0-Alchemist-0/Game_Consoles/Assets/RPSLS_game/ChatGPT Image May 15, 2026, 11_23_18 PM (2).png

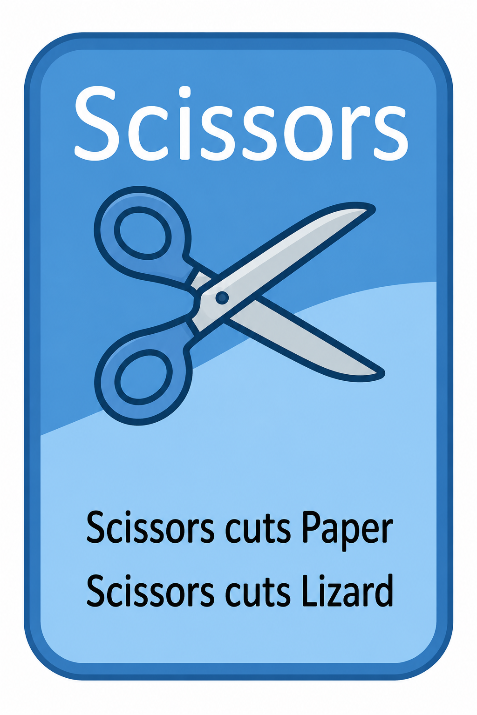
Assets/RPSLS_game/ChatGPT Image May 15, 2026, 11_23_18 PM (2).png
