0-Alchemist-0/Game_Consoles/Assets/RPSLS_game/Gemini_Generated_Image_hztmo1hztmo1hztm.png

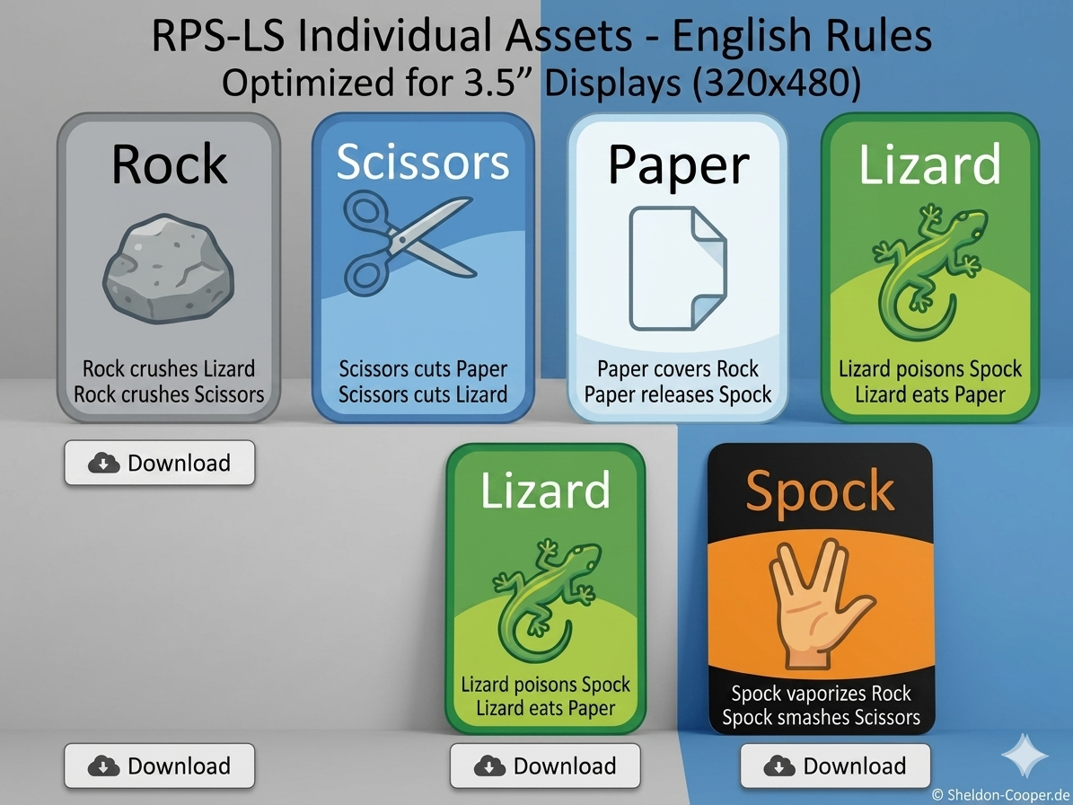
Assets/RPSLS_game/Gemini_Generated_Image_hztmo1hztmo1hztm.png
