0-Alchemist-0/Game_Consoles/CAD/Reference 18650 Cell - 1029881/images/18650_Refrence_Cell.png

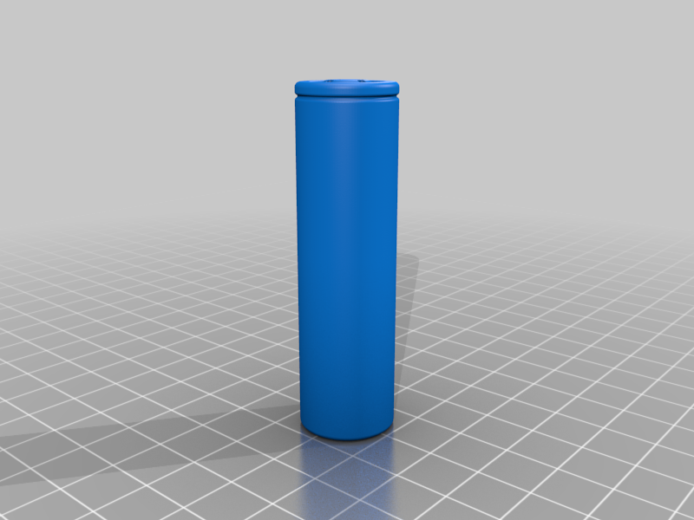
CAD/Reference 18650 Cell - 1029881/images/18650_Refrence_Cell.png
