0-Alchemist-0/Game_Consoles/CAD/Reference 18650 Cell - 1029881/images/ice_screenshot_20150923-011706.png

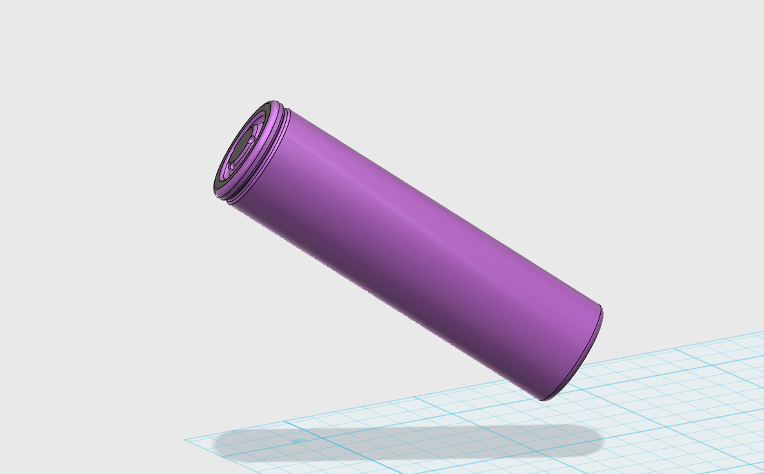
CAD/Reference 18650 Cell - 1029881/images/ice_screenshot_20150923-011706.png
