0-Alchemist-0/Game_Consoles/Pics&Videos/00002_LowerCase.png

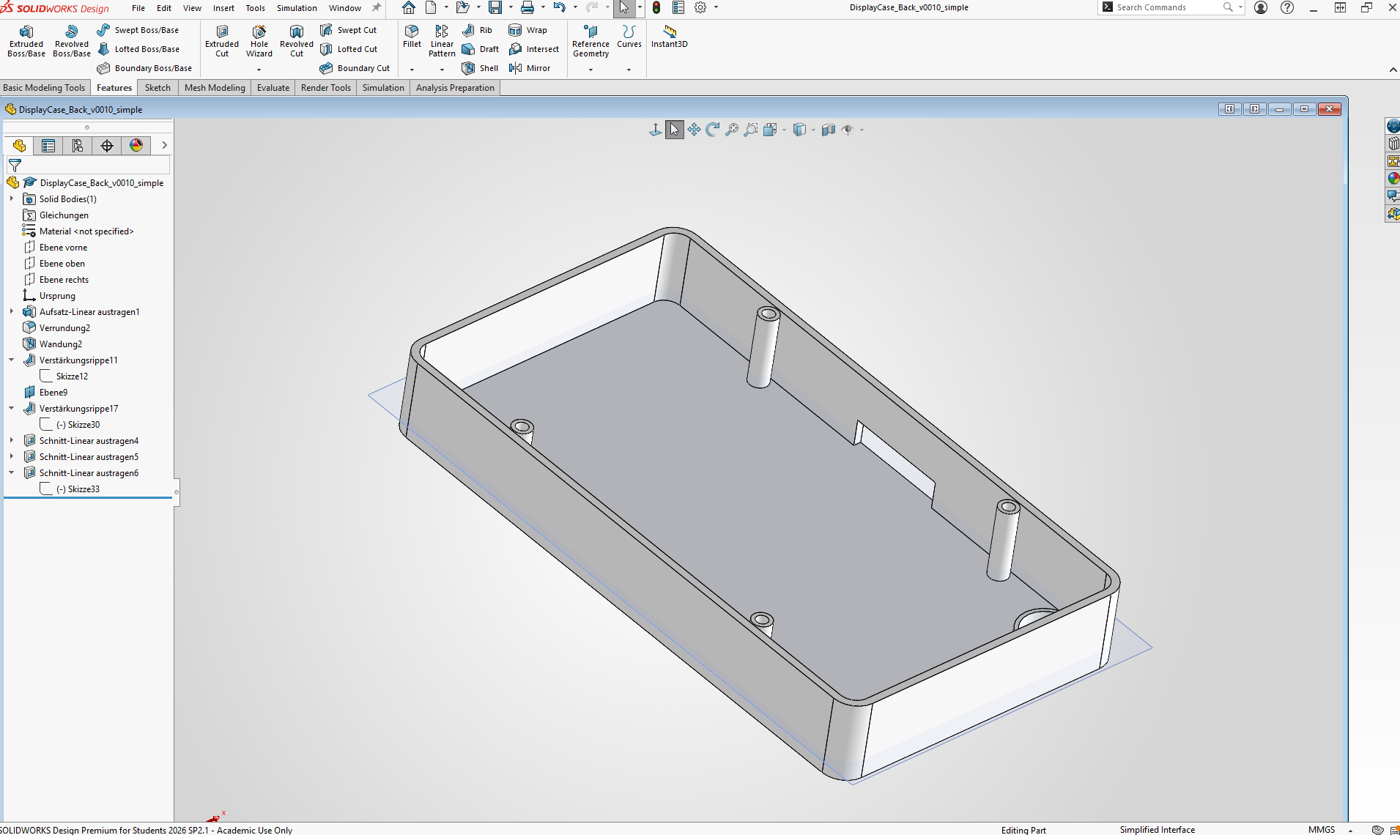
Pics&Videos/00002_LowerCase.png
