0-Alchemist-0/Game_Consoles/Pics&Videos/00003_TopCoverCase.png

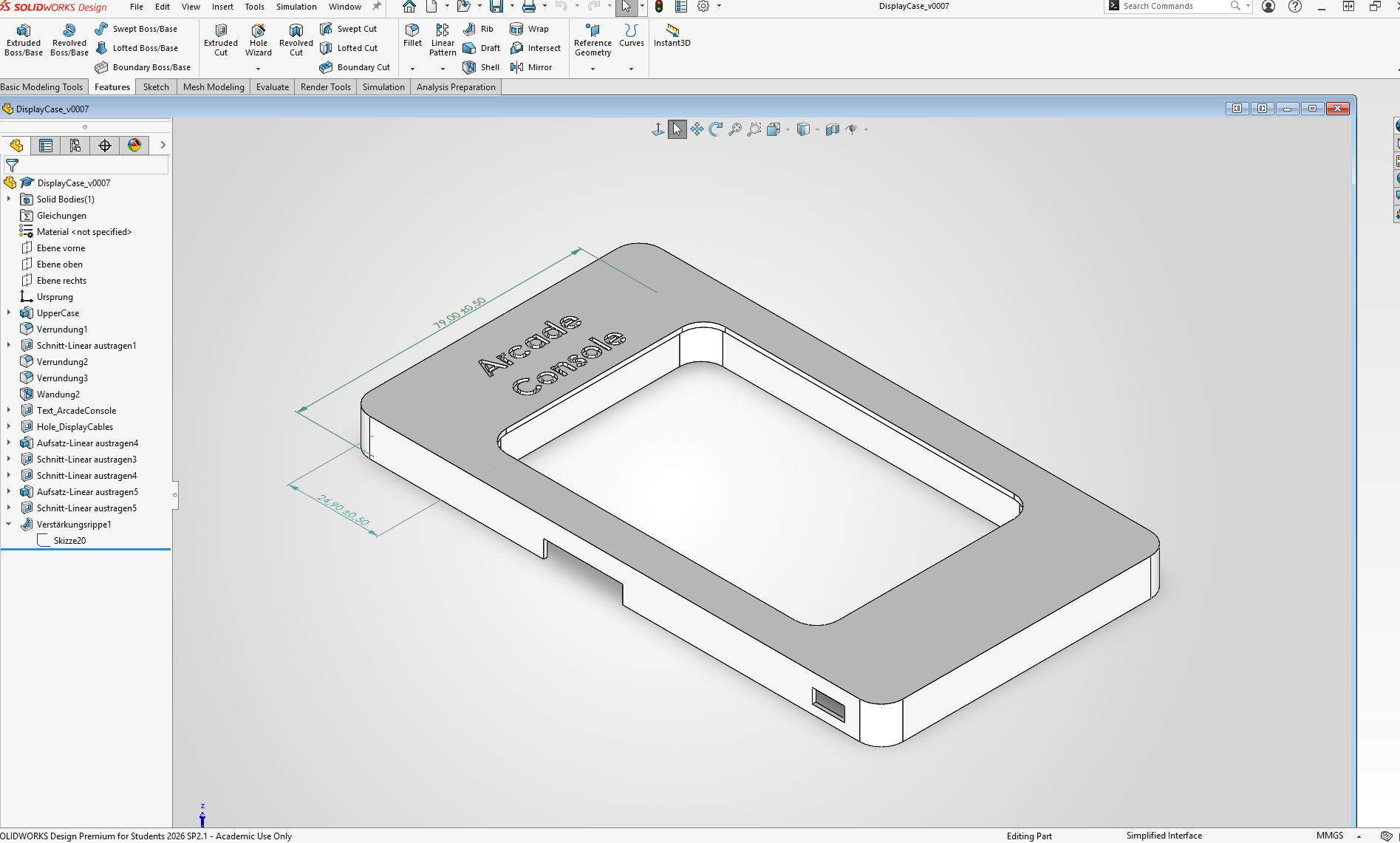
Pics&Videos/00003_TopCoverCase.png
