0-Alchemist-0/Game_Consoles/Pics&Videos/0004_Internal 18650 battery holder.png

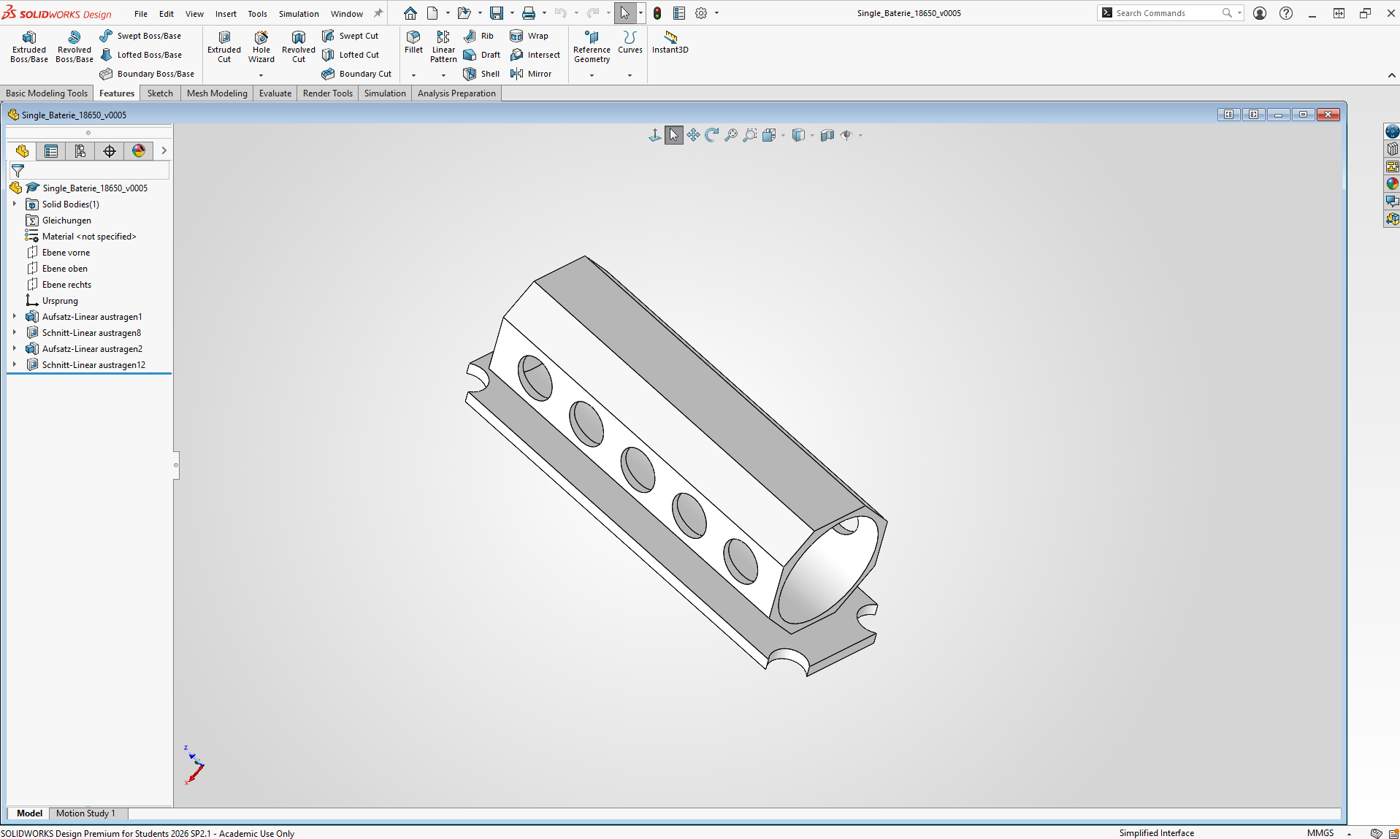
Pics&Videos/0004_Internal 18650 battery holder.png
