0-Alchemist-0/Game_Consoles/Pics&Videos/0005_PCB_Supprt.png

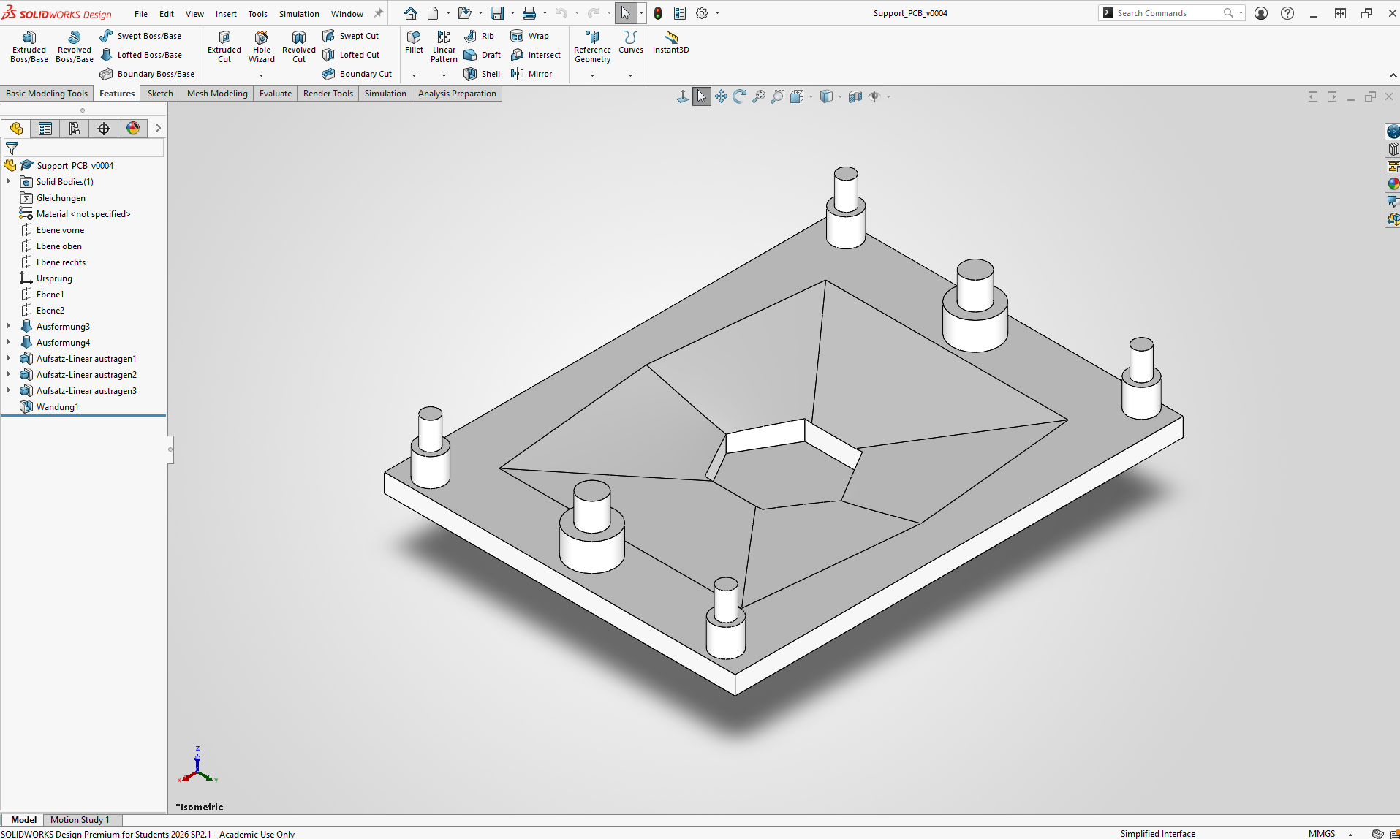
Pics&Videos/0005_PCB_Supprt.png
