0-Alchemist-0/Game_Consoles/Pics&Videos/0006_Support part for the Arduino Nano ESP32 board.png

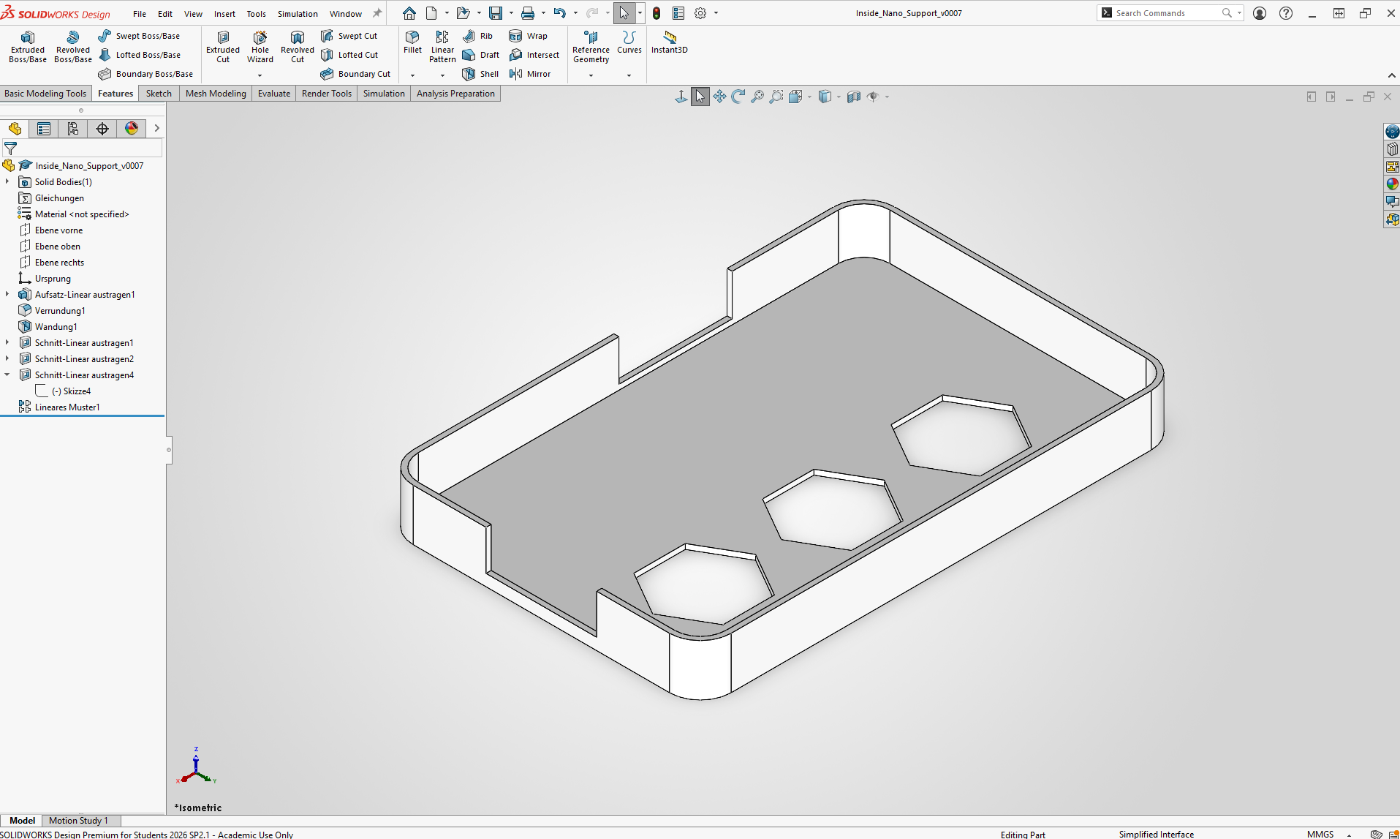
Pics&Videos/0006_Support part for the Arduino Nano ESP32 board.png
