0-Alchemist-0/Game_Consoles/Pics&Videos/0009_Top-down open view of the console.jpeg

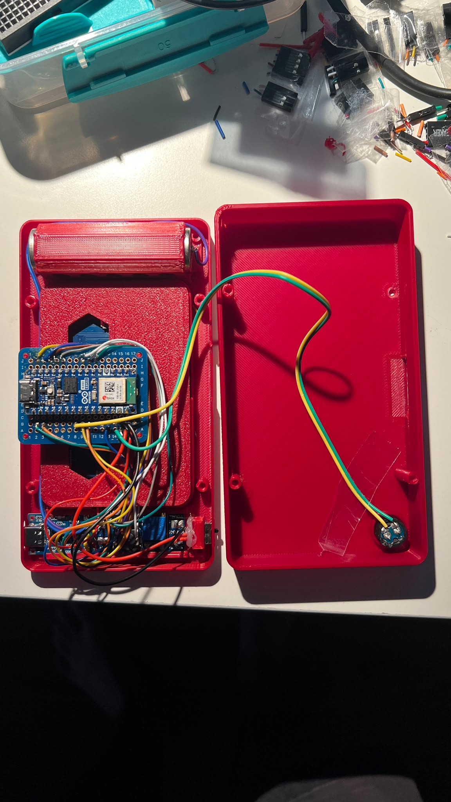
Pics&Videos/0009_Top-down open view of the console.jpeg
