0-Alchemist-0/Game_Consoles/SD_card/games_screen/games_background.png

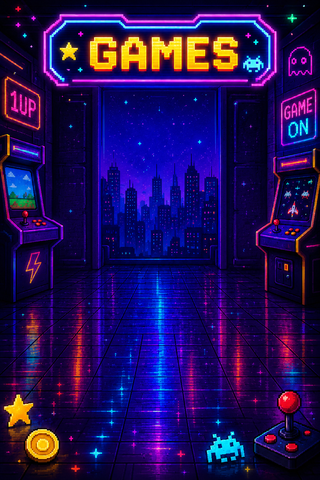
SD_card/games_screen/games_background.png
