0-Alchemist-0/Game_Consoles/SD_card/home_screen/background_preview.png

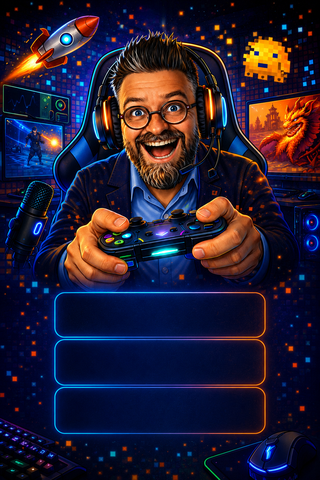
SD_card/home_screen/background_preview.png
