0-Alchemist-0/Game_Consoles/SD_card/intro/frame_000_preview.png

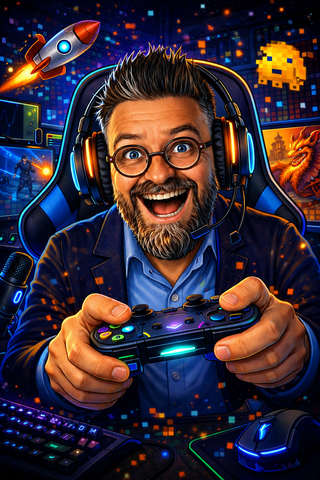
SD_card/intro/frame_000_preview.png
