0-Alchemist-0/Game_Consoles/SD_card/RPSLS_game/general/RockPapercissors.png

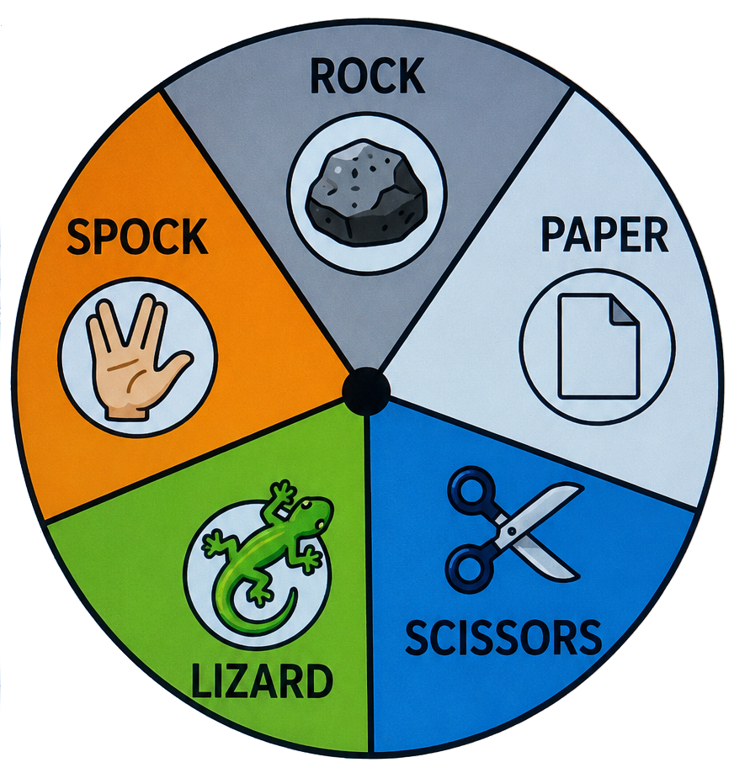
SD_card/RPSLS_game/general/RockPapercissors.png
