0-Alchemist-0/Game_Consoles/SD_card/RPSLS_game/general/rpsls_wheel_preview.png

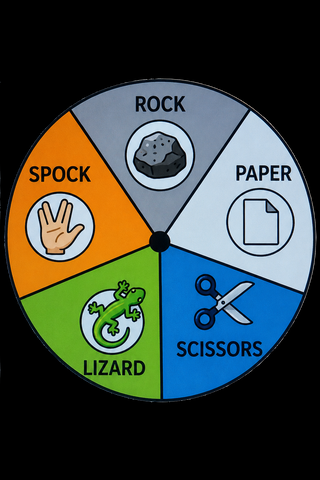
SD_card/RPSLS_game/general/rpsls_wheel_preview.png
