0-Alchemist-0/Game_Consoles/SD_card/RPSLS_game/local/draw/draw_spock_preview.png

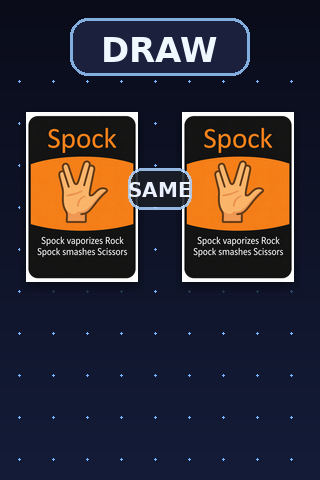
SD_card/RPSLS_game/local/draw/draw_spock_preview.png
