0-Alchemist-0/Game_Consoles/SD_card/RPSLS_game/local/player1_wins/win_lizard_eats_paper_preview.png

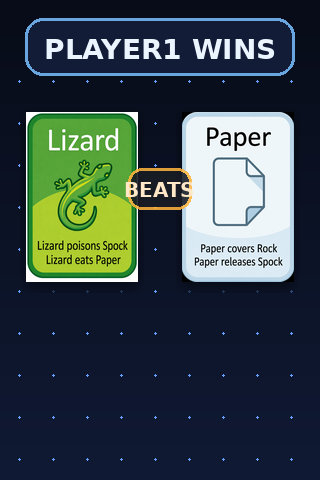
SD_card/RPSLS_game/local/player1_wins/win_lizard_eats_paper_preview.png
