0-Alchemist-0/Game_Consoles/SD_card/RPSLS_game/lose/lose_lizard_to_rock_preview.png

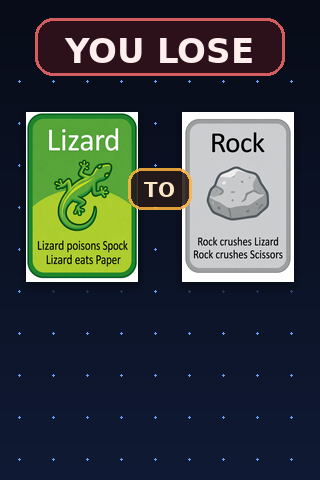
SD_card/RPSLS_game/lose/lose_lizard_to_rock_preview.png
