0-Alchemist-0/Game_Consoles/SD_card/RPSLS_game/lose/lose_rock_to_spock_preview.png

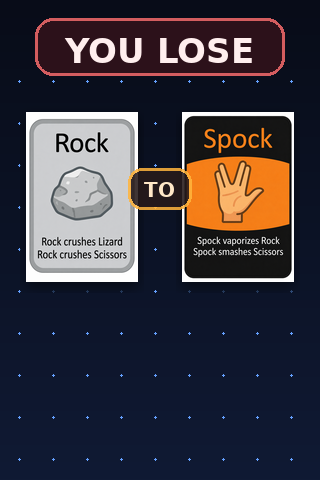
SD_card/RPSLS_game/lose/lose_rock_to_spock_preview.png
