0-Alchemist-0/Game_Consoles/SD_card/RPSLS_game/lose/lose_spock_to_lizard_preview.png

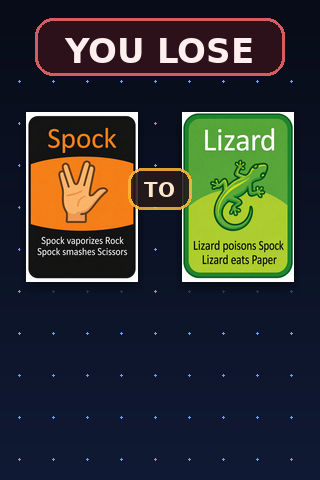
SD_card/RPSLS_game/lose/lose_spock_to_lizard_preview.png
