0-Alchemist-0/Game_Consoles/SD_card/RPSLS_game/main_screen/rock_paper_scissors_background.png

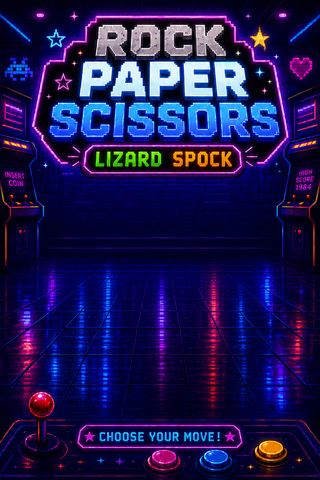
SD_card/RPSLS_game/main_screen/rock_paper_scissors_background.png
