0-Alchemist-0/Game_Consoles/SD_card/tictactoe_game/tictactoe_background.png

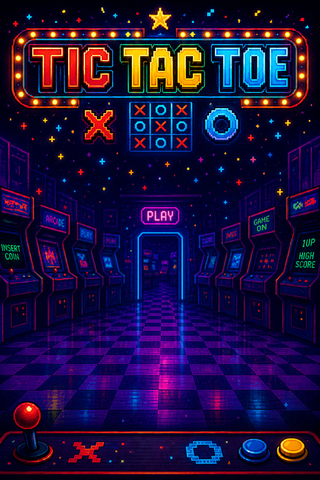
SD_card/tictactoe_game/tictactoe_background.png
