0-Alchemist-0/Game_Consoles/CAD/Carcasa_v0001-BodyFillet.step

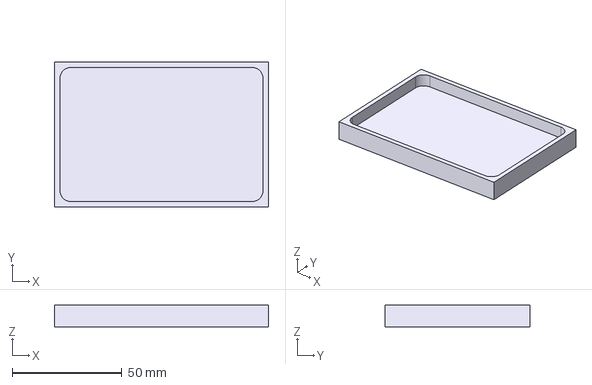
[picture p62: CAD file, 2026-05-14]
CAD/Carcasa_v0001-BodyFillet.step
97.6 x 66.2 x 10.0 mm
