0-Alchemist-0/Game_Consoles/SolidWorks/DisplayCase_Back_v0011_simple.SLDPRT

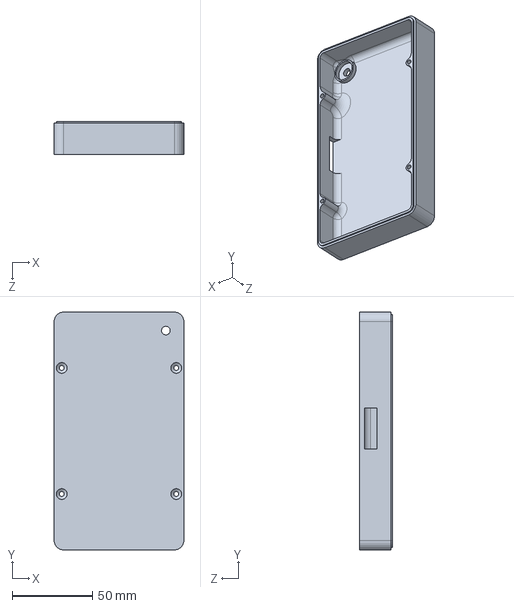
[picture p63: CAD file, 2026-07-01]
SolidWorks/DisplayCase_Back_v0011_simple.SLDPRT
81.0 x 148.4 x 20.6 mm
