0-Alchemist-0/Game_Consoles/SolidWorks/DisplayCase_v0008.SLDPRT

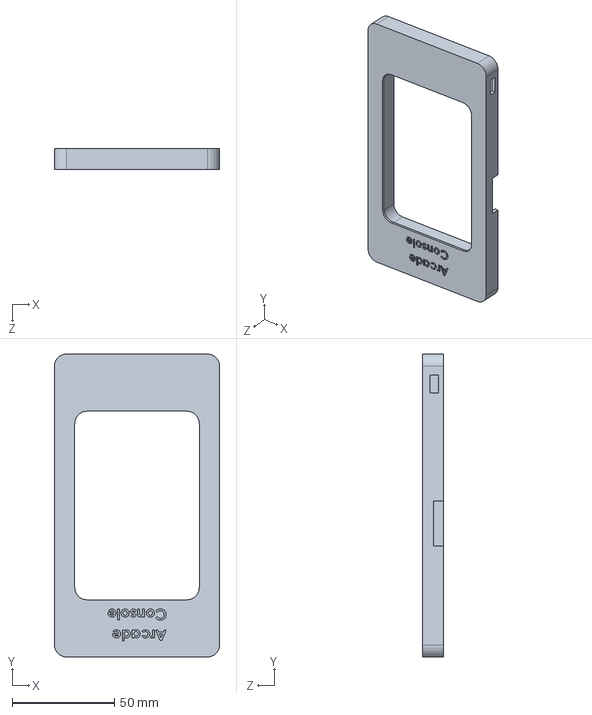
[picture p64: CAD file, 2026-07-01]
SolidWorks/DisplayCase_v0008.SLDPRT
81.0 x 148.4 x 10.3 mm
