0-Alchemist-0/Game_Consoles/SolidWorks/Single_Baterie_18650_v0006_simple.SLDPRT

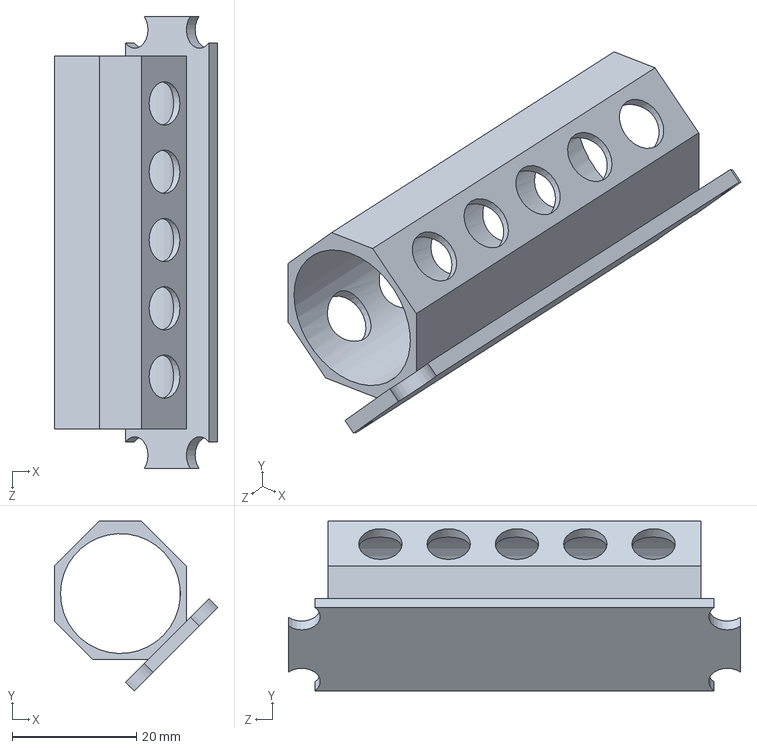
[picture p66: CAD file, 2026-07-01]
SolidWorks/Single_Baterie_18650_v0006_simple.SLDPRT
26.3 x 27.3 x 72.8 mm
