0-Alchemist-0/Game_Consoles/SolidWorks/DisplayCase_v0010_simple.SLDPRT

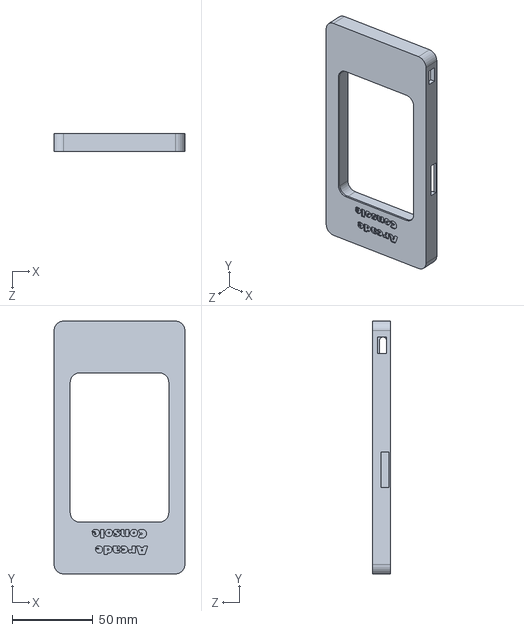
[picture p67: CAD file, 2026-07-01]
SolidWorks/DisplayCase_v0010_simple.SLDPRT
81.0 x 156.4 x 11.3 mm
