0-Alchemist-0/Game_Consoles/SolidWorks/MT3608_4056_v0002.SLDPRT

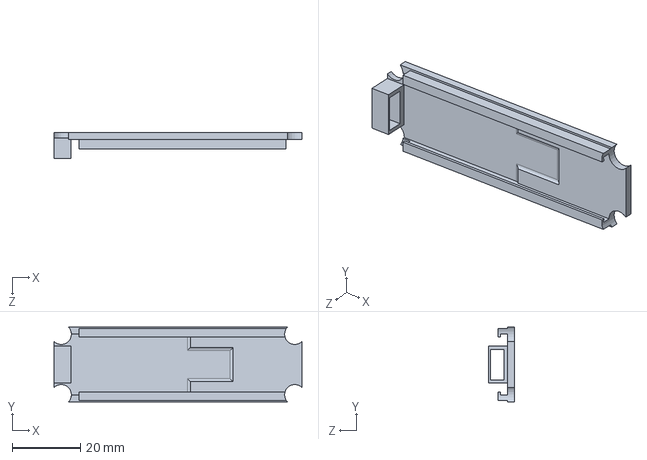
[picture p68: CAD file, 2026-06-27]
SolidWorks/MT3608_4056_v0002.SLDPRT
72.8 x 22.0 x 7.50 mm
