0-Alchemist-0/Game_Consoles/SolidWorks/Support_PCB_v0003.SLDPRT

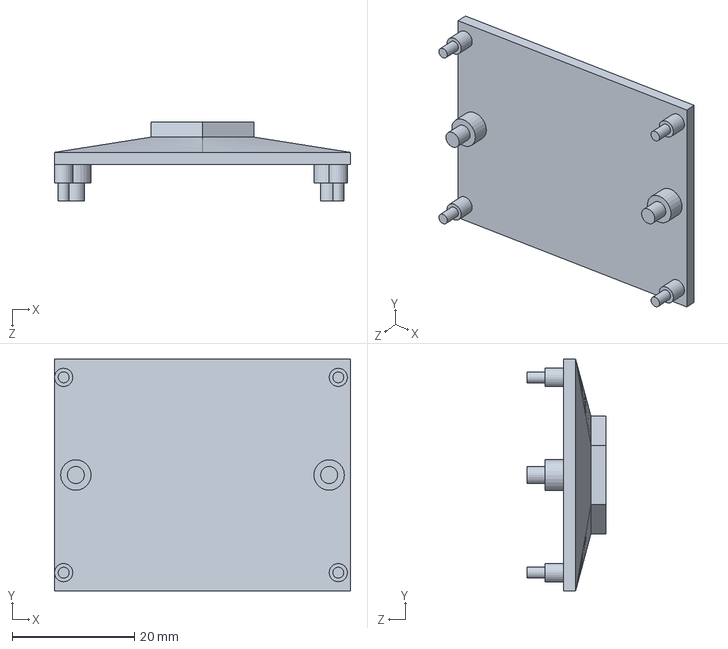
[picture p69: CAD file, 2026-06-27]
SolidWorks/Support_PCB_v0003.SLDPRT
48.5 x 38.0 x 13.0 mm
