0-Alchemist-0/Game_Consoles/SolidWorks/016_Suport_OLED_PCB-PCB_EPȘZON.step

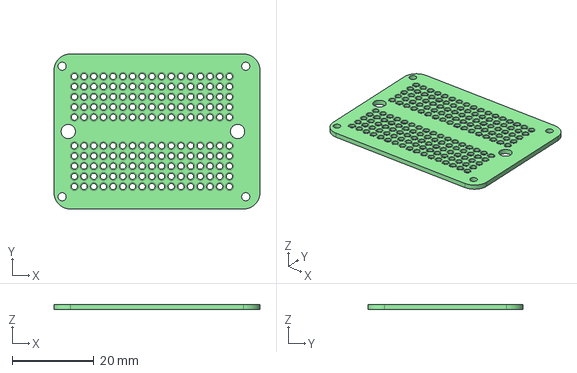
[picture p70: CAD file, 2026-06-27]
SolidWorks/016_Suport_OLED_PCB-PCB_EPȘZON.step
50.5 x 38.0 x 1.30 mm
