0-Alchemist-0/Game_Consoles/SolidWorks/Single_Baterie_18650_v0005.SLDPRT

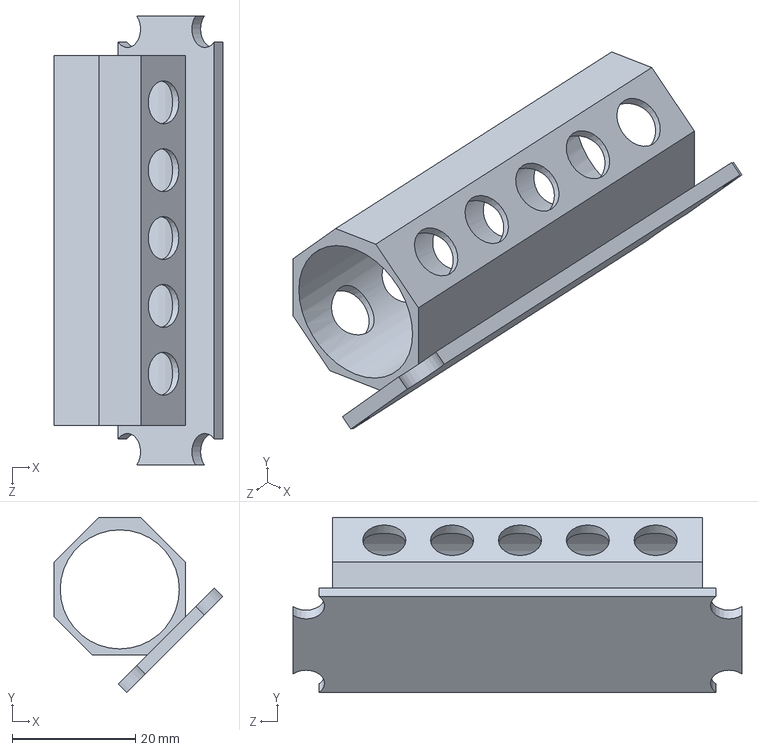
[picture p71: CAD file, 2026-06-27]
SolidWorks/Single_Baterie_18650_v0005.SLDPRT
27.4 x 28.4 x 72.8 mm
