0-Alchemist-0/Game_Consoles/SolidWorks/MT3608_4056_v0001.SLDPRT

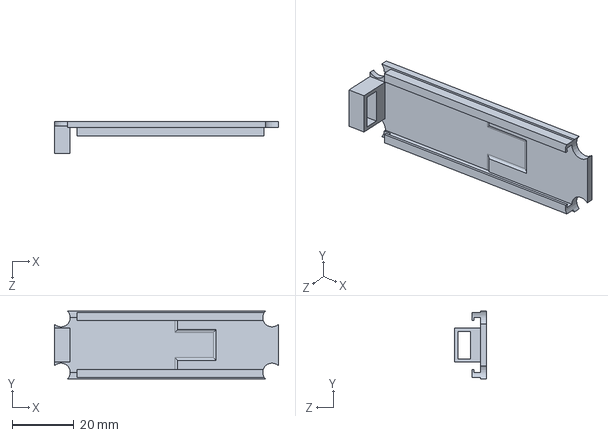
[picture p72: CAD file, 2026-06-27]
SolidWorks/MT3608_4056_v0001.SLDPRT
72.8 x 22.0 x 10.5 mm
