0-Alchemist-0/Game_Consoles/SolidWorks/DisplayCase_v0003.SLDPRT

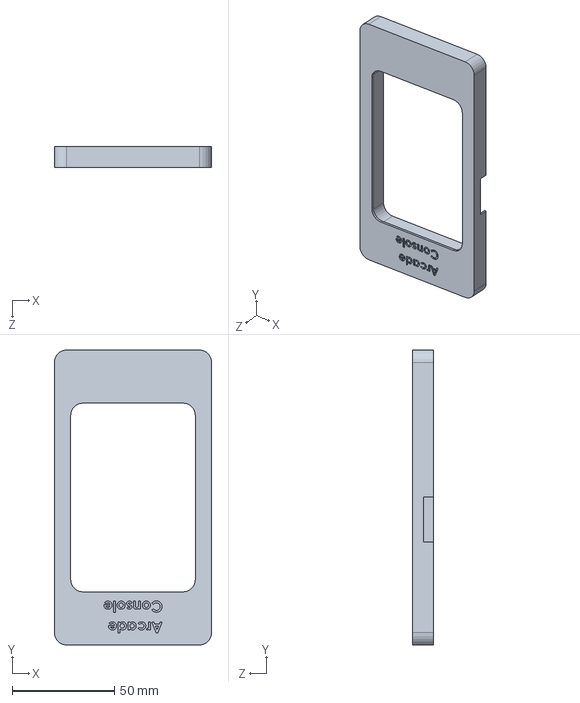
[picture p73: CAD file, 2026-06-27]
SolidWorks/DisplayCase_v0003.SLDPRT
77.0 x 144.4 x 10.3 mm
