0-Alchemist-0/Game_Consoles/SolidWorks/DisplayCase_Back_v0002.SLDPRT

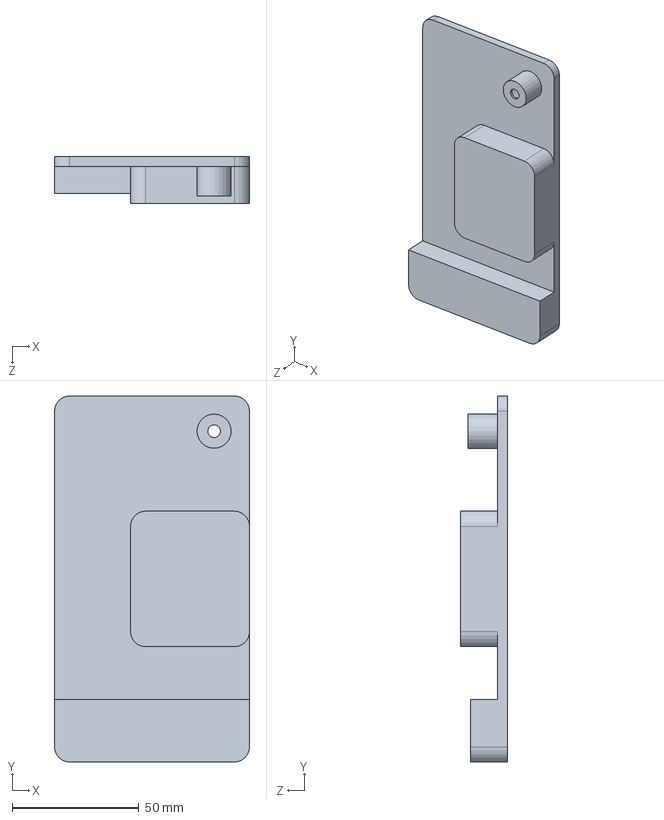
[picture p74: CAD file, 2026-06-27]
SolidWorks/DisplayCase_Back_v0002.SLDPRT
77.0 x 144.4 x 18.6 mm
