0-Alchemist-0/Game_Consoles/SolidWorks/Single_Baterie_18650.SLDPRT

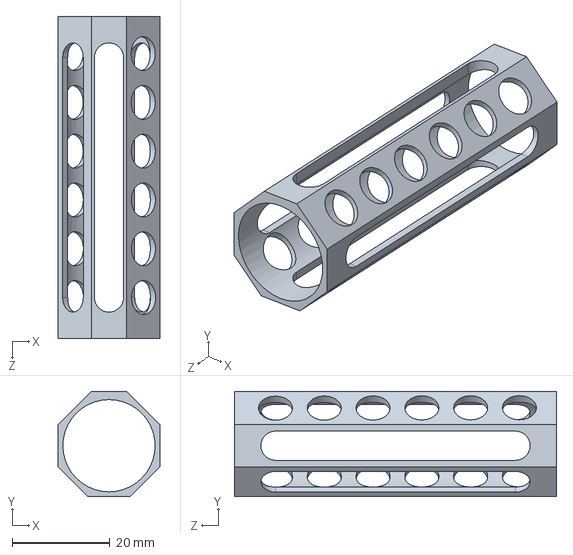
[picture p75: CAD file, 2026-06-27]
SolidWorks/Single_Baterie_18650.SLDPRT
20.9 x 21.6 x 66.0 mm
