0-Alchemist-0/Game_Consoles/SolidWorks/Inside_Nano_Support_v0006.SLDPRT

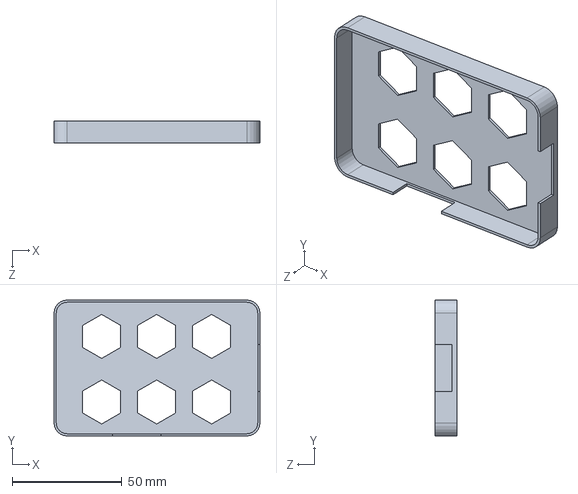
[picture p76: CAD file, 2026-06-27]
SolidWorks/Inside_Nano_Support_v0006.SLDPRT
93.6 x 61.8 x 10.0 mm
