0-Alchemist-0/Game_Consoles/SolidWorks/DisplayCase_Back_v0004.SLDPRT

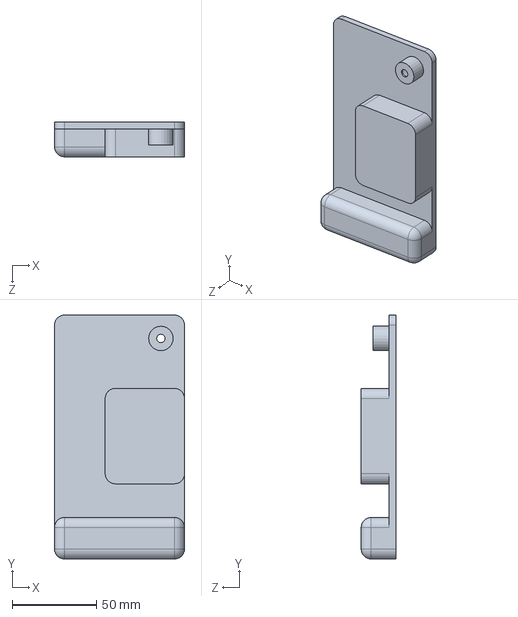
[picture p77: CAD file, 2026-06-27]
SolidWorks/DisplayCase_Back_v0004.SLDPRT
77.0 x 144.4 x 20.6 mm
