0-Alchemist-0/Game_Consoles/SolidWorks/MT3608 HW-045 DC-DC Step-Up.stl

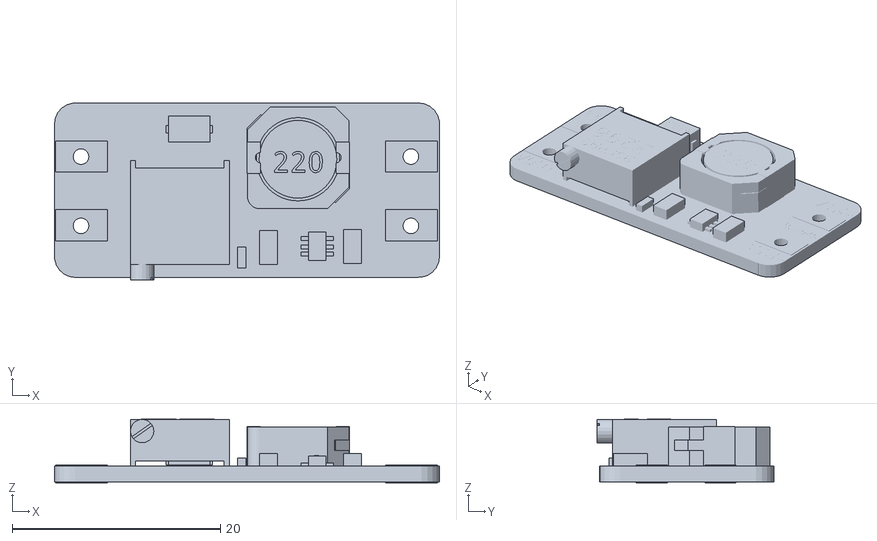
[picture p78: CAD file, 2026-06-27]
SolidWorks/MT3608 HW-045 DC-DC Step-Up.stl
37.0 x 17.0 x 6.12
