0-Alchemist-0/Game_Consoles/SolidWorks/Inside_Nano_Support_v0001.SLDPRT

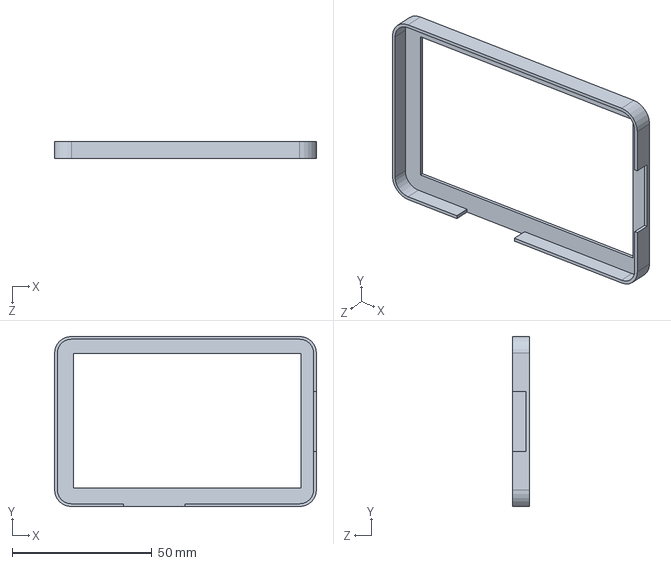
[picture p79: CAD file, 2026-06-27]
SolidWorks/Inside_Nano_Support_v0001.SLDPRT
93.6 x 60.8 x 6.00 mm
