0-Alchemist-0/Game_Consoles/SolidWorks/Double_Pack_Baterie_18650.SLDPRT

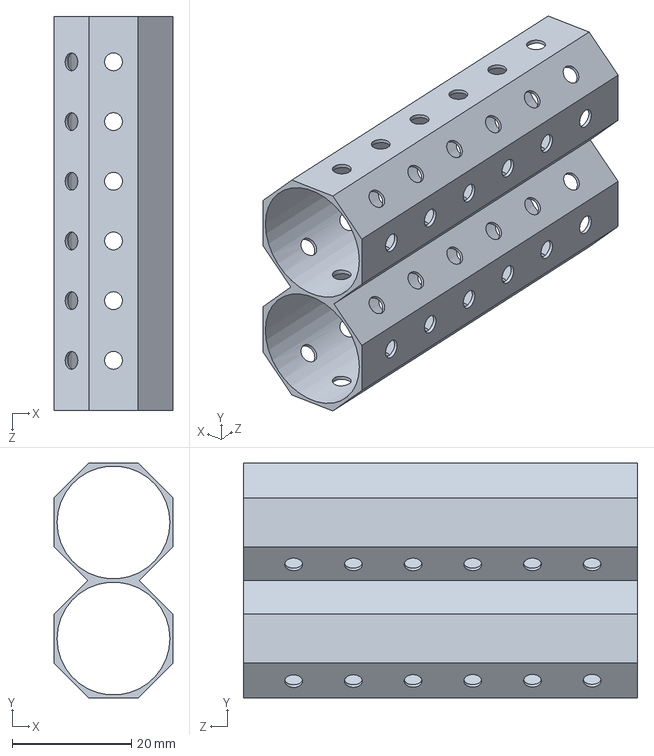
[picture p81: CAD file, 2026-06-27]
SolidWorks/Double_Pack_Baterie_18650.SLDPRT
19.9 x 39.3 x 66.0 mm
