0-Alchemist-0/Game_Consoles/SolidWorks/DisplayCase_Back_v0006.SLDPRT

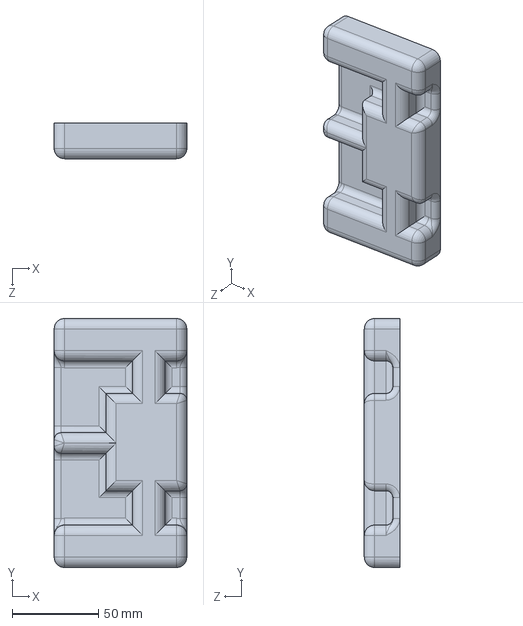
[picture p82: CAD file, 2026-06-27]
SolidWorks/DisplayCase_Back_v0006.SLDPRT
77.0 x 144.4 x 20.6 mm
