0-Alchemist-0/Game_Consoles/SolidWorks/MT3608_4056_v0003.SLDPRT

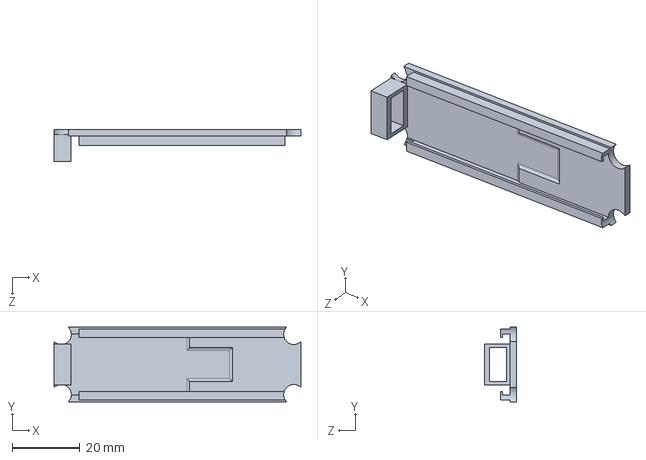
[picture p83: CAD file, 2026-06-27]
SolidWorks/MT3608_4056_v0003.SLDPRT
72.8 x 22.0 x 9.50 mm
