0-Alchemist-0/Game_Consoles/SolidWorks/016_Suport_OLED_PCB-Support_OLED.step

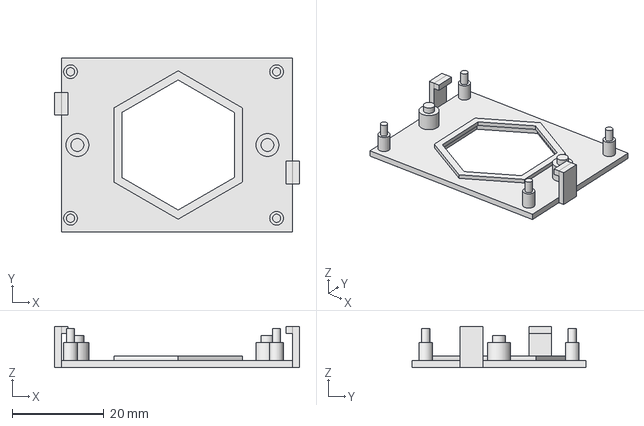
[picture p84: CAD file, 2026-06-27]
SolidWorks/016_Suport_OLED_PCB-Support_OLED.step
53.5 x 38.0 x 9.00 mm
