0-Alchemist-0/Game_Consoles/SolidWorks/Inside_Nano_Support_v0004.SLDPRT

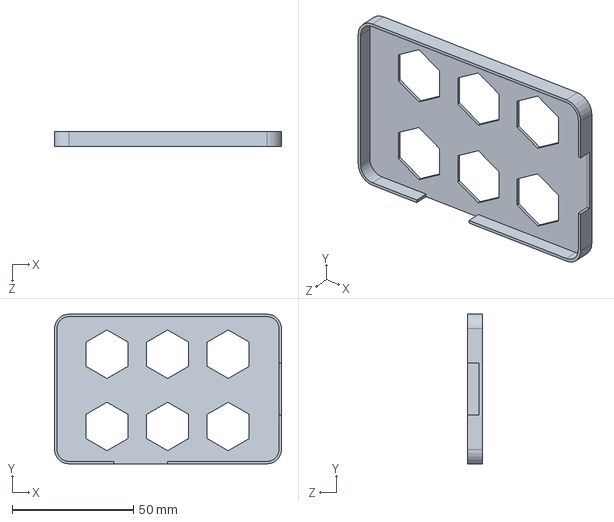
[picture p85: CAD file, 2026-06-27]
SolidWorks/Inside_Nano_Support_v0004.SLDPRT
93.6 x 61.8 x 6.00 mm
