0-Alchemist-0/Game_Consoles/SolidWorks/Support_PCB.SLDPRT

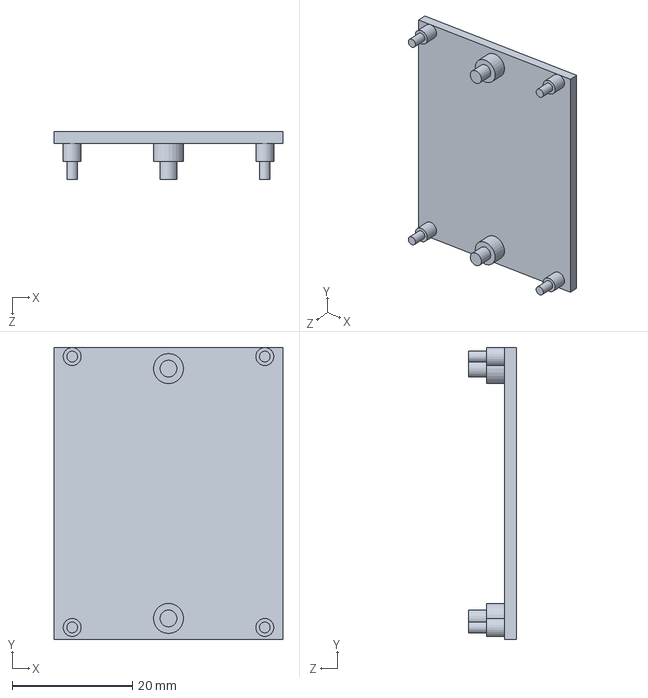
[picture p86: CAD file, 2026-06-27]
SolidWorks/Support_PCB.SLDPRT
38.0 x 48.5 x 8.00 mm
