0-Alchemist-0/Game_Consoles/SolidWorks/Inside_Nano_Support_v0002.SLDPRT

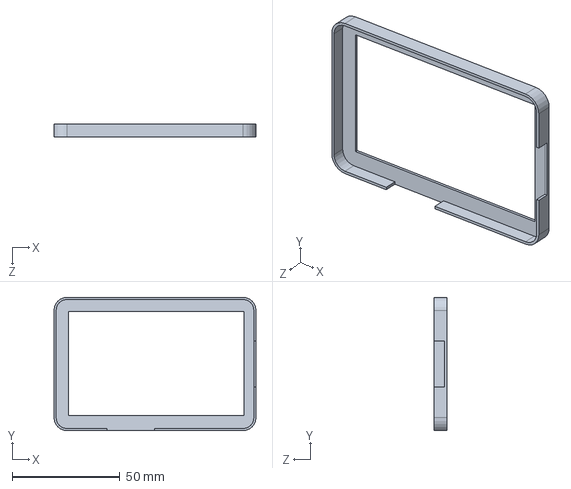
[picture p87: CAD file, 2026-06-27]
SolidWorks/Inside_Nano_Support_v0002.SLDPRT
93.6 x 61.8 x 6.00 mm
