0-Alchemist-0/Game_Consoles/SolidWorks/DisplayCase_Back_v0009.SLDPRT

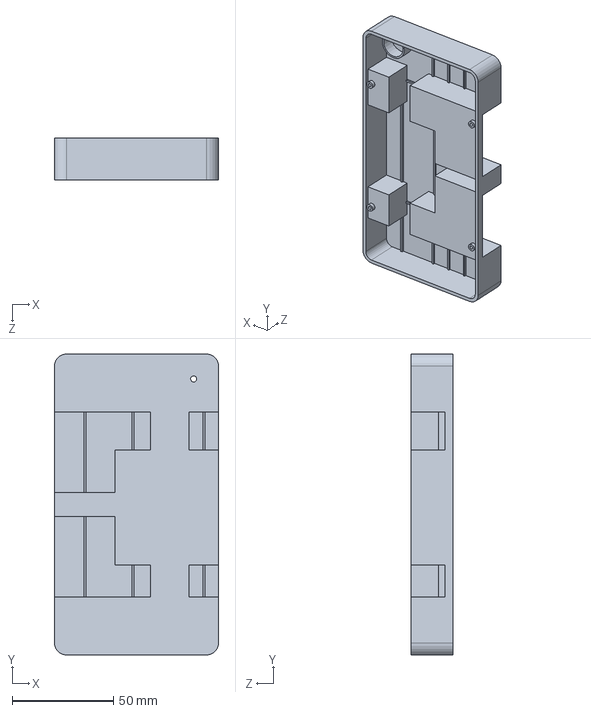
[picture p88: CAD file, 2026-06-27]
SolidWorks/DisplayCase_Back_v0009.SLDPRT
81.0 x 148.4 x 20.6 mm
