0-Alchemist-0/Game_Consoles/SolidWorks/DisplayCase_Back_v0010_simple.SLDPRT

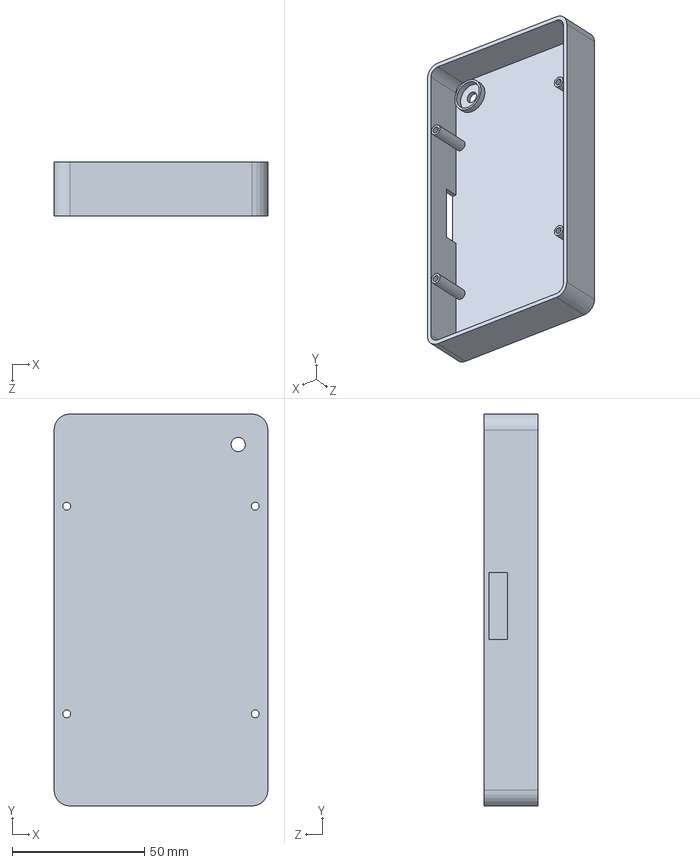
[picture p89: CAD file, 2026-06-27]
SolidWorks/DisplayCase_Back_v0010_simple.SLDPRT
81.0 x 148.4 x 20.6 mm
