0-Alchemist-0/Game_Consoles/SolidWorks/Single_Baterie_18650_v0003.SLDPRT

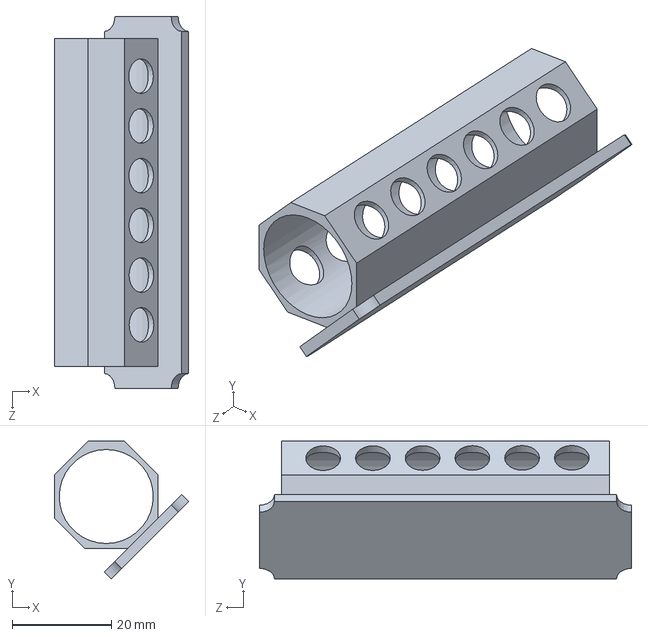
[picture p90: CAD file, 2026-06-27]
SolidWorks/Single_Baterie_18650_v0003.SLDPRT
27.0 x 27.7 x 74.8 mm
