0-Alchemist-0/Game_Consoles/SolidWorks/Single_Baterie_18650_v0002.SLDPRT

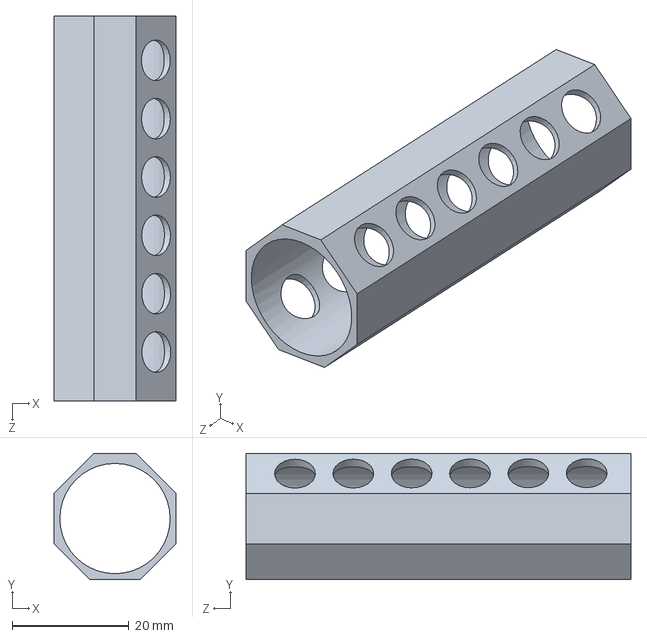
[picture p91: CAD file, 2026-06-27]
SolidWorks/Single_Baterie_18650_v0002.SLDPRT
20.9 x 21.6 x 66.0 mm
