0-Alchemist-0/Game_Consoles/SolidWorks/DisplayCase_v0006.SLDPRT

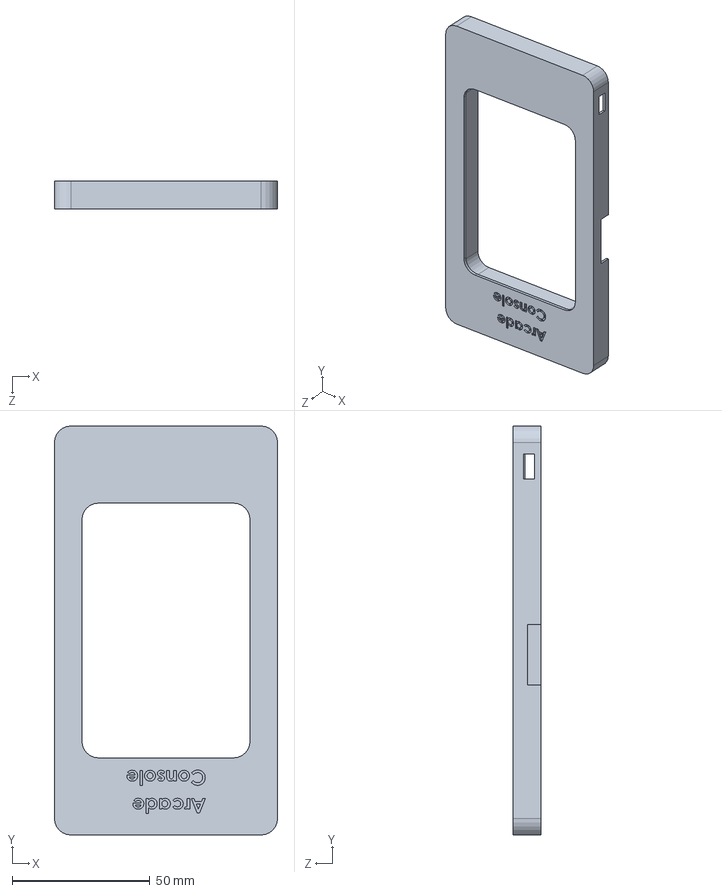
[picture p92: CAD file, 2026-06-27]
SolidWorks/DisplayCase_v0006.SLDPRT
81.0 x 148.4 x 10.3 mm
