0-Alchemist-0/Game_Consoles/SolidWorks/PiezoSpeaker.SLDPRT

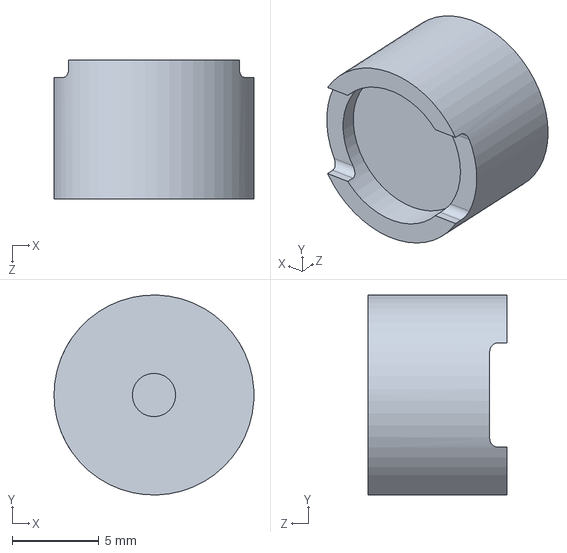
[picture p93: CAD file, 2026-06-27]
SolidWorks/PiezoSpeaker.SLDPRT
11.5 x 11.5 x 8.00 mm
