0-Alchemist-0/Game_Consoles/SolidWorks/On_Off_Switch.SLDPRT

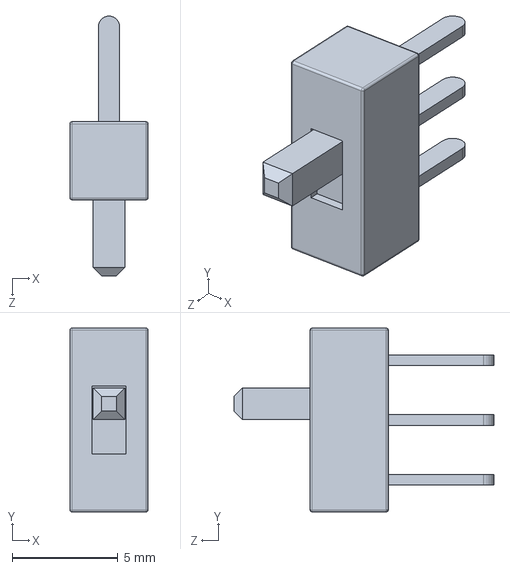
[picture p94: CAD file, 2026-06-27]
SolidWorks/On_Off_Switch.SLDPRT
3.70 x 8.70 x 12.3 mm
