0-Alchemist-0/Game_Consoles/Pics&Videos/0001_Assembly.png

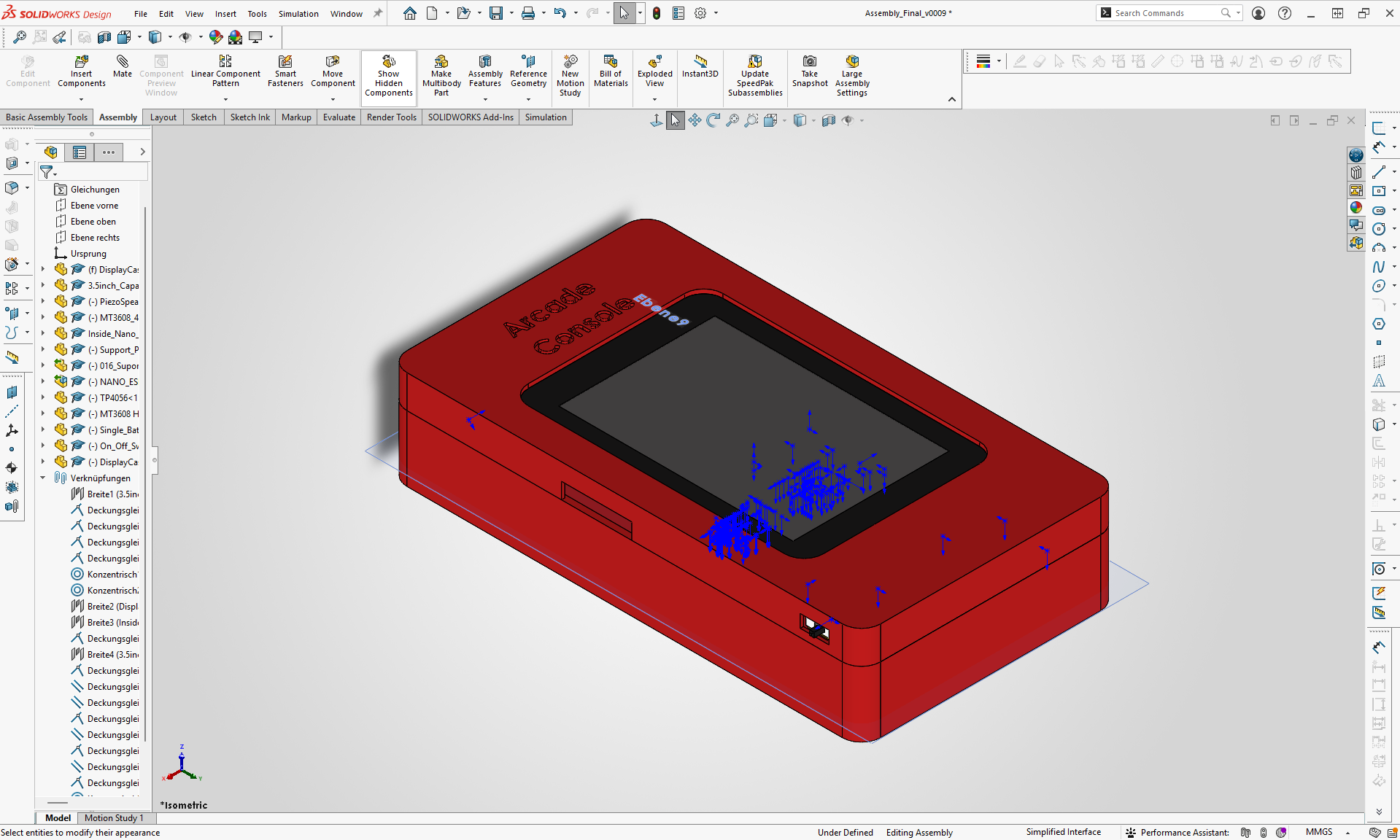
Pics&Videos/0001_Assembly.png
