0-Alchemist-0/Game_Consoles/Pics&Videos/0008_Physical assembly of the console prototype.jpeg

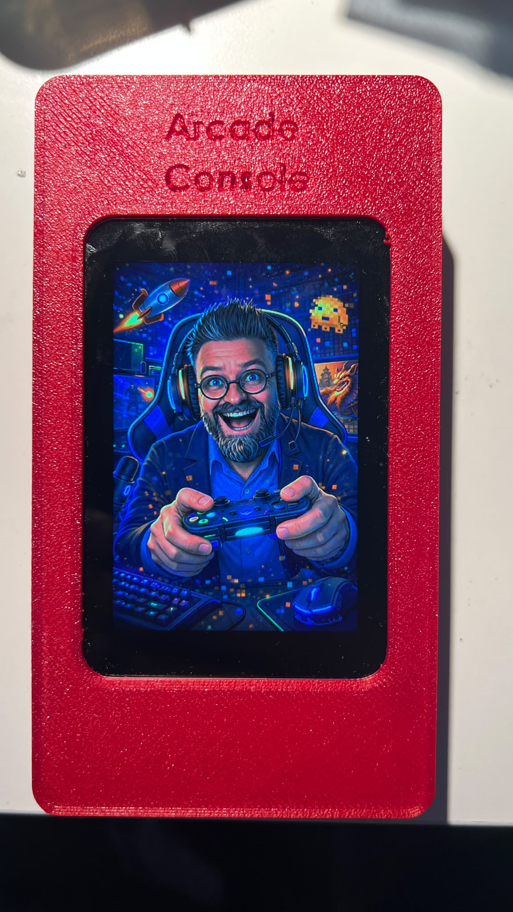
Pics&Videos/0008_Physical assembly of the console prototype.jpeg
