0-Alchemist-0/Game_Consoles/Game_Consoles.ino

// ============================================================================
// CHANGELOG
// ============================================================================
// Version 9.5 - 2026-07-01 - Stabilized Tic Tac Toe network joining by
// preferring configured or known Host SSIDs, throttling Join TCP retries, and
// disabling WiFi sleep/TCP buffering during peer games.
// Version 9.4 - 2026-07-01 - Expanded source block comments with game
// ownership notes so each major code area explains its purpose.
// Version 9.3 - 2026-07-01 - Removed the hour from every changelog entry and
// standardized changelog dates to use date-only format.
// Version 9.2 - 2026-07-01 - Added network Hex Pipes gameplay with a
// shared puzzle seed, visible P1/P2 move counters, solve-time race logic, and
// less-moves tie breaker.
// Version 9.1 - 2026-07-01 - Added Hex Pipes to the Games menu with a
// dedicated game menu, hexapipes.vercel.app reference, local playable puzzle,
// best-score storage, and Host/Join placeholders.
// Version 9.0 - 2026-07-01 - Added Reset Score buttons and high-score
// display lines to every game main menu, with persistent high scores for
// Breakout, Pong, and Snake.
// Version 8.9 - 2026-07-01 - Converted remaining menu and page UI text
// to English across Tic Tac Toe, shared network screens, and result screens.
// Version 8.8 - 2026-07-01 - Reworked Home Settings into Music and WiFi
// subpages, with Music ON/OFF, SFX ON/OFF, editable Host IP, and persisted
// default WiFi SSID selection.
// Version 8.7 - 2026-07-01 - Added a looping non-game background
// chiptune inspired by the attached arcade melody, with automatic mute during
// gameplay and short audio cues taking priority.
// Version 8.6 - 2026-06-19 - Switched Frogger Host/Join to use the standard
// WiFi TCP flow (same as Tic Tac Toe) instead of ESP-NOW.  Both players run
// traffic locally, exchange frog-state/goal/over messages over TCP, and the
// FROG_STATE parsing is now symmetric so both host and join apply remote state.
// Version 8.5 - 2026-06-18 - Reworked Frogger Host/Join to use the
// attached ESP-NOW peer-to-peer concept with local frog simulation, HELLO/ACK/
// START pairing, and compact frog, goal, and game-over packets.
// Version 8.4 - 2026-06-18 - Reworked Frogger network gameplay using the
// attached local-simulation model: each console moves its own frog and exchanges
// compact frog states over the existing TCP link.
// Version 8.3 - 2026-06-18 - Reverted Frogger JOIN local lane animation
// changes after they broke second-console gameplay.
// Version 8.2 - 2026-06-18 - Prevented Frogger JOIN lane position jumps
// by using remote lane coordinates only during full redraw synchronization.
// Version 8.1 - 2026-06-18 - Reduced Frogger JOIN flicker by animating
// lanes locally and using remote states only for sync plus player redraws.
// Version 8.0 - 2026-06-18 - Reduced Frogger network state backlog and
// added input sequence tracking so P2 movement is not overwritten by old states.
// Version 7.9 - 2026-06-18 - Fixed Frogger network controls by forcing
// P1/P2 player roles, immediate network respawn, and lighter remote input redraws.
// Version 7.8 - 2026-06-18 - Fixed Frogger network movement feedback by
// redrawing player inputs immediately and moving the first road car off-center.
// Version 7.7 - 2026-06-18 - Fixed the Frogger network compile error by
// declaring sendFroggerState before updateFroggerGame uses it.
// Version 7.6 - 2026-06-18 - Added host-authoritative Frogger network
// gameplay with two visible colored players sharing the same lanes and logs.
// Version 7.5 - 2026-06-18 - Added Frogger to the Games menu with a
// dedicated mode menu and local playable road, river, logs, cars, goals, and
// high score gameplay.
// Version 7.4 - 2026-06-18 - Added host-authoritative Ranch Rush network
// gameplay with two visible differently colored players and synced ranch state.
// Version 7.3 - 2026-06-18 - Fixed Ranch Rush lasso persistence by using
// a gameplay cowboy sprite without the decorative menu lasso loop.
// Version 7.2 - 2026-06-18 - Implemented local Ranch Rush gameplay with
// lane movement, lasso catching, animal spawning, lives, levels, high score,
// dirty-rect rendering, restart, and menu return.
// Version 7.1 - 2026-06-18 - Added Ranch Rush to the Games menu with a
// ranch-themed mode menu, Local/Host/Join/Back navigation, and shared network
// setup placeholders.
// Version 7.0 - 2026-06-18 - Added network Snake gameplay with
// host-authoritative two-player movement, synced state packets, shared food,
// different snake colors, and remote direction control.
// Version 6.9 - 2026-06-18 - Reduced Snake movement flicker by switching
// from full-board redraws to incremental cell updates during movement.
// Version 6.8 - 2026-06-18 - Implemented local Snake gameplay with a
// timed grid loop, food spawning, collision detection, score HUD, touch
// direction controls, restart, and menu return.
// Version 6.7 - 2026-06-18 - Added Snake to the Games menu with a
// dedicated Local, Host, Join, and Back mode menu wired into the shared
// network setup flow.
// Version 6.6 - 2026-06-18 - Improved network Pong Player 2 paddle
// collision by preserving client-owned paddle state, adding remote-paddle hit
// forgiveness, and predicting local bounce.
// Version 6.5 - 2026-06-17 - Smoothed network Pong ball movement by
// sending velocity in PN_STATE, throttling host broadcasts, and predicting
// ball motion locally between received state packets.
// Version 6.4 - 2026-06-17 - Added Host/Join network gameplay for
// Pong with host-authoritative ball physics and synced paddle/score state.
// Version 6.3 - 2026-06-17 - Added Pong to the Games menu with a
// local playable portrait paddle game and arcade-style menu.
// Version 6.2 - 2026-06-17 - Added Host/Join network gameplay for
// Breakout where the first player to lose all three lives loses the match.
// Version 6.1 - 2026-06-17 - Matched Breakout menu buttons to the
// Tic Tac Toe transparent arcade text style by removing extra slot panels.
// Version 6.0 - 2026-06-17 - Added a generated arcade fallback
// background for the Breakout menu and switched its menu buttons to the
// transparent Tic Tac Toe arcade text style.
// Version 5.9 - 2026-06-17 - Implemented local portrait Breakout
// gameplay with bricks, paddle, touch controls, lives, score, and restart.
// Version 5.8 - 2026-06-17 - Added a generated arcade fallback
// background for the Tanks Wars menu and switched its menu buttons to the
// transparent Tic Tac Toe arcade text style.
// Version 5.7 - 2026-06-17 - Added a second Games page with Breakout and
// a Breakout mode menu containing Local, Host, Join, and Back.
// Version 5.6 - 2026-06-17 - Added Host/Join network gameplay for Tanks
// Wars with synced terrain seed, controls, turns, and firing.
// Version 5.5 - 2026-06-17 - Added a generated arcade HOME fallback
// screen when SD home assets are missing.
// Version 5.4 - 2026-06-16 - Renamed user-facing artillery game text to
// Tanks Wars across menus, placeholders, and screen titles.
// Version 5.3 - 2026-06-03 - Added SD-loaded Rock-Paper-Scissors menu
// background support from /RPSLS_game/main_screen/rock_paper_scissors_background.raw.
// Version 5.2 - 2026-06-03 - Ported the Rock-Paper-Scissors arcade menu
// background and switched its menu to the transparent arcade text buttons.
// Version 5.1 - 2026-06-03 - Changed Games and Tic Tac Toe menu buttons
// to transparent arcade text buttons with consistent two-color lettering.
// Version 5.0 - 2026-06-03 - Added SD-loaded Tic Tac Toe menu background
// support from /tictactoe_game/tictactoe_background.raw with generated fallback.
// Version 4.9 - 2026-06-03 - Added SD-loaded Games screen background
// support from /games_screen/games_background.raw with generated fallback.
// Version 4.8 - 2026-06-03 - Added an arcade background and marquee title
// to the Games selection screen, reusing the neon button text style.
// Version 4.7 - 2026-06-03 - Ported the arcade Tic Tac Toe menu artwork
// and changed shared UI buttons to the same neon arcade style.
// Version 4.6 - 2026-06-03 - Added Arduino Nano ESP32 board-label and
// physical-header comments for each configured GPIO.
// Version 4.5 - 2026-05-28 - Added explanatory comments across the main
// source blocks to make hardware, UI, networking, and game logic easier to read.
// Version 4.4 - 2026-05-27 - Added randomized Tanks Wars terrain
// generation for each new local round.
// Version 4.3 - 2026-05-27 - Removed Tanks Wars full-screen redraws
// from angle and power controls to reduce UI flicker.
// Version 4.2 - 2026-05-27 - Smoothed Tanks Wars projectile animation
// by redrawing only the projectile area with a fixed frame time.
// Version 4.1 - 2026-05-27 - Replaced Battleship with a Tanks Wars
// menu and added first local artillery gameplay with destructible terrain.
// Version 4.0 - 2026-05-27 - Added viewpoint-specific RPSLS network
// result images from /RPSLS_game/win and /RPSLS_game/lose.
// Version 3.9 - 2026-05-27 - Added network Host/Join gameplay for RPSLS
// using the same WiFi setup flow and hidden-choice result logic as local play.
// Version 3.8 - 2026-05-27 - Changed game mode menu Home buttons to Back
// buttons that return to the Games selection screen.
// Version 3.7 - 2026-05-20 - Added SD-loaded RPSLS draw screens based on
// the shared choice selected by both players.
// Version 3.6 - 2026-05-20 - Added SD-loaded RPSLS winning screens based
// on the exact winning choice combination for Player 1 and Player 2.
// Version 3.5 - 2026-05-20 - Added Home screen version/build metadata
// and defined the Build ID format based on version plus date/hour.
// Version 3.4 - 2026-05-20 - Removed timezone offsets from changelog
// timestamps and standardized future changelog entries to omit them.
// Version 3.3 - 2026-05-20 - Added version numbers to all
// changelog entries, starting at Version 1.0 and incrementing by 0.1 per change.
// Version 3.2 - 2026-05-20 - Switched the RPSLS choice screen to use the
// SD-loaded /RPSLS_game/general/rpsls_wheel.raw image while keeping invisible
// touch segments for selection.
// Version 3.1 - 2026-05-15 - Added the missing RGB888 to RGB565 helper used by
// the Rock-Paper-Scissors wheel colors.
// Version 3.0 - 2026-05-15 - Replaced the Rock-Paper-Scissors placeholder with
// a local Rock-Paper-Scissors-Lizard-Spock flow, menu, scores, and result page.
// Version 2.9 - 2026-05-15 - Added a Games hub page with Tic Tac Toe,
// Rock-Paper-Scissors, Battleship, and Home navigation.
// Version 2.8 - 2026-05-14 - Expanded Join WiFi selection to show eight SSIDs
// per page and added MORE pagination for additional scanned networks.
// Version 2.7 - 2026-05-14 - Added "Connect and Die" and "The LAN of the Free"
// to the selectable Host SSID list.
// Version 2.6 - 2026-05-14 - Expanded the Host Select SSID page to show eight
// SSID options per page.
// Version 2.5 - 2026-05-14 - Changed the frame_000.raw intro hold from 4 seconds
// to 1 second.
// Version 2.4 - 2026-05-14 - Finalized Host Select SSID layout with four visible
// SSIDs per page, compact list text, and larger Host waiting SSID/IP display.
// Version 2.3 - 2026-05-14 - Added two-step Host setup: select an epic SSID,
// confirm Host IP with keypad, then start AP mode with password Alchemist2026.
// Version 2.2 - 2026-05-14 - Added two-step Join setup: select scanned WiFi
// network, confirm Host IP with keypad, then connect with password Alchemist2026.
// Version 2.1 - 2026-05-14 - Added an IP settings page with four editable fields,
// numeric keypad input, persistent storage, and default IP 192.168.10.1.
// Version 2.0 - 2026-05-11 - Moved the Tic Tac Toe Home button to the game mode
// menu page with Local, Host, Join, and Reset Score.
// Version 1.9 - 2026-05-11 - Changed the home screen Exit button to reboot the
// ESP32 instead of blanking the display.
// Version 1.8 - 2026-05-11 - Scaled the home screen RAW buttons to fit the
// button slots defined in background.raw.
// Version 1.7 - 2026-05-11 - Added an SD-loaded home screen after the intro with
// background and Games, Settings, and Exit RAW buttons.
// Version 1.6 - 2026-05-11 - Added a 4 second hold on frame_000.raw before the
// rest of the RAW intro animation plays.
// Version 1.5 - 2026-05-11 - Finalized RAW565 portrait intro playback at normal
// rotation, starting from frame_000.raw.
// Version 1.4 - 2026-05-11 - Enabled inverted display colors through a dedicated
// display setting.
// Version 1.3 - 2026-05-11 - Added microSD support for boot intro and SD-loaded
// UI assets while keeping local and WiFi gameplay modes.
// Version 1.2 - 2026-05-11 - Removed the duplicate sketch compile conflict by
// keeping Game_Consoles.ino as the active Arduino sketch file.
// Version 1.1 - 2026-05-11 - Rebuilt the sketch with a clean structure while
// keeping local play, WiFi host/join play, persistent score, touch input, and UI.
// Version 1.0 - 2026-05-11 - Added local play mode with a main menu option,
// allowing X and O to play on the same device without WiFi.

#include <Arduino_GFX_Library.h>
#include <Wire.h>
#include <WiFi.h>
#include <Preferences.h>
#include <SPI.h>
#include <SD.h>
#include <FS.h>
#include <math.h>
#include <string.h>
#include <esp_now.h>
#include <esp_wifi.h>
#include <esp_system.h>

// ============================================================================
// HARDWARE CONFIG
// ============================================================================
// Board wiring for Arduino Nano ESP32 + ILI9488 display, FT6336 touch,
// microSD card, and buzzer. Keep these values aligned with the physical wiring.
// The sketch uses ESP32 GPIO numbering. Comments also show the Arduino Nano
// ESP32 board label and physical header position.
static const int PIN_LCD_CS   = 21;  // GPIO21, Arduino D10, physical header JP2-3.
static const int PIN_LCD_DC   = 18;  // GPIO18, Arduino D9, physical header JP2-4.
static const int PIN_LCD_RST  = 17;  // GPIO17, Arduino D8, physical header JP2-5.

static const int PIN_LCD_MOSI = 38;  // GPIO38, Arduino D11/MOSI, physical header JP2-2.
static const int PIN_LCD_MISO = 47;  // GPIO47, Arduino D12/MISO, physical header JP2-1.
static const int PIN_LCD_SCLK = 48;  // GPIO48, Arduino D13/SCK, physical header JP1-1.

static const int PIN_SD_CS    = 8;   // GPIO8, Arduino D5, physical header JP2-8.
static const int SD_SPI_FREQ  = 49000000;

static const int PIN_TP_INT   = 6;   // GPIO6, Arduino D3, physical header JP2-10.
static const int PIN_TP_RST   = 7;   // GPIO7, Arduino D4, physical header JP2-9.

static const int PIN_SDA      = 11;  // GPIO11, Arduino A4/SDA, physical header JP1-8.
static const int PIN_SCL      = 12;  // GPIO12, Arduino A5/SCL, physical header JP1-9.

static const int PIN_BUZZER   = 4;   // GPIO4, Arduino A3, physical header JP1-7.

static const uint8_t FT6336_ADDR = 0x38;

// Keep these in sync with the newest CHANGELOG entry.
// Build ID format: GC-V<major><minor>-<YYYYMMDDHH>.
const char *APP_VERSION_TEXT = "Version 9.5";
const char *APP_BUILD_ID_TEXT = "Build ID GC-V95-2026070121";



// ============================================================================
// NETWORK CONFIG
// ============================================================================
// Shared network settings used by all WiFi game modes. The host creates an
// access point, and the join device connects to it using the fixed password.
const char *AP_SSID = "TicTacToe_ESP32";
const char *AP_PASS = "Alchemist2026";
const char *JOIN_WIFI_PASS = "Alchemist2026";

// Human-friendly SSID options shown on the Host setup page.
const char *epicSSIDList[] = {
  "Searching for Network...",
  "404 Wi-Fi Not Found",
  "Martin Router King",
  "Wu-Tang LAN",
  "Tell My Wi-Fi Love Her",
  "Virus.exe",
  "The Promised LAN",
  "Drop It Like It's Hotspot",
  "Wi-Fi: Art or Sacrifice?",
  "Pretty Fly for a Wi-Fi",
  "Surveillance Camera #04",
  "FBI Surveillance Van",
  "Loading...",
  "Connecting...",
  "Winternet is Coming",
  "It Hurts When IP",
  "Obi-Wan Kenobi",
  "Silence of the LANs",
  "Buy Your Own Internet",
  "Password is 1234... or not",
  "Bill Wi the Science Fi",
  "The LAN Before Time",
  "Lord of the Pings",
  "Skynet Global Defense",
  "Paid Network (5$/min)",
  "I Can Haz Wireless?",
  "No Free Wi-Fi Here",
  "Get your own Wi-Fi!",
  "Searching for Signal...",
  "The Golden Wi-Fi",
  "Connect and Die",
  "The LAN of the Free"
};

const int EPIC_SSID_COUNT = sizeof(epicSSIDList) / sizeof(epicSSIDList[0]);

const uint16_t NET_PORT = 3333;
IPAddress HOST_IP(192, 168, 10, 1);

WiFiServer gameServer(NET_PORT);
WiFiClient netClient;

// ============================================================================
// DISPLAY / STORAGE
// ============================================================================
// Global display, persistent flash storage, and SD readiness state shared by
// Home, Settings, and every game.
Preferences prefs;
const bool INVERT_DISPLAY_COLORS = true;

Arduino_DataBus *bus = new Arduino_HWSPI(
  PIN_LCD_DC,
  PIN_LCD_CS,
  PIN_LCD_SCLK,
  PIN_LCD_MOSI,
  PIN_LCD_MISO
);

Arduino_GFX *gfx = new Arduino_ILI9488_18bit(bus, PIN_LCD_RST, 0, false);

bool sdReady = false;
bool musicEnabled = true;
bool sfxEnabled = true;

// ============================================================================
// APP STATE
// ============================================================================
// Every screen has one AppState so the touch router can dispatch input to the
// correct handler without guessing from what was last drawn. These states cover
// Home/Games, Settings, shared WiFi setup, and all game screens.
enum AppState {
  STATE_HOME,
  STATE_GAMES,
  STATE_GAMES_MORE,
  STATE_GAMES_EXTRA,
  STATE_ROCK_PAPER_SCISSORS,
  STATE_RPS_CHOICE_P1,
  STATE_RPS_CHOICE_P2,
  STATE_RPS_WAITING_CHOICE,
  STATE_RPS_RESULT,
  STATE_RPS_PLACEHOLDER,
  STATE_POCKET_TANKS,
  STATE_PT_PLAYING,
  STATE_PT_RESULT,
  STATE_PT_PLACEHOLDER,
  STATE_BREAKOUT,
  STATE_BREAKOUT_PLAYING,
  STATE_BREAKOUT_PLACEHOLDER,
  STATE_PONG,
  STATE_PONG_PLAYING,
  STATE_PONG_PLACEHOLDER,
  STATE_SNAKE,
  STATE_SNAKE_PLAYING,
  STATE_SNAKE_PLACEHOLDER,
  STATE_RANCH_RUSH,
  STATE_RR_PLAYING,
  STATE_RR_PLACEHOLDER,
  STATE_FROGGER,
  STATE_FROGGER_PLAYING,
  STATE_FROGGER_PLACEHOLDER,
  STATE_HEX_PIPES,
  STATE_HEX_PIPES_PLAYING,
  STATE_HEX_PIPES_SOLVED,
  STATE_HEX_PIPES_PLACEHOLDER,
  STATE_EMPTY_GAME,
  STATE_MENU,
  STATE_SETTINGS,
  STATE_SETTINGS_MUSIC,
  STATE_SETTINGS_WIFI,
  STATE_EXIT,
  STATE_HOST_SETUP,
  STATE_HOST_IP,
  STATE_JOIN_SETUP,
  STATE_JOIN_IP,
  STATE_WAITING_HOST,
  STATE_CONNECTING_JOIN,
  STATE_PLAYING,
  STATE_RESULT
};

AppState appState = STATE_HOME;

// The WiFi setup screens are shared by all network-capable games. This value
// tells the connection code which game should start after Host/Join connects.
enum NetworkGameType {
  NETWORK_GAME_TTT,
  NETWORK_GAME_RPS,
  NETWORK_GAME_PT,
  NETWORK_GAME_BREAKOUT,
  NETWORK_GAME_PONG,
  NETWORK_GAME_SNAKE,
  NETWORK_GAME_RANCH_RUSH,
  NETWORK_GAME_FROGGER,
  NETWORK_GAME_HEX_PIPES
};

NetworkGameType activeNetworkGame = NETWORK_GAME_TTT;

// Tic Tac Toe round state.
char board[3][3];
char currentPlayer = 'X';
bool gameOver = false;
char winner = ' ';

// Shared local/network role flags. Tic Tac Toe, RPSLS, Tanks Wars, Breakout,
// Pong, Snake, Ranch Rush, Frogger, and Hex Pipes all use these to decide who
// may act and which menu should be restored after leaving a game.
bool localGame = false;
bool isHost = false;
bool networkConnected = false;
char myPlayer = ' ';
bool myTurn = false;

// Host SSID selector state.
static const int MAX_HOST_SSID_VISIBLE = 8;
int selectedHostSSIDIndex = 0;
int hostSSIDListOffset = 0;

// Join scan list state. The scan is copied into this array so the UI can page
// through it without holding WiFi scan resources open.
static const int MAX_JOIN_NETWORKS = 24;
static const int MAX_JOIN_NETWORKS_VISIBLE = 8;
String joinNetworks[MAX_JOIN_NETWORKS];
int joinNetworkCount = 0;
int selectedJoinNetwork = -1;
int joinNetworkListOffset = 0;
unsigned long joinWifiStartedAt = 0;
unsigned long joinTcpLastAttempt = 0;
int joinTcpAttemptCount = 0;
static const unsigned long JOIN_TCP_RETRY_MS = 850;
static const unsigned long JOIN_WIFI_RETRY_MS = 15000;

// Editable IP fields shared by Settings, Host IP, and Join IP screens.
uint8_t ipParts[4] = {192, 168, 10, 1};
char ipFieldText[4][4] = {"192", "168", "10", "1"};
int activeIpField = 0;
bool activeIpFieldNeedsClear = true;

// Tic Tac Toe persistent score values.
int scoreX = 0;
int scoreO = 0;
int scoreDraw = 0;

// RPSLS uses numeric choices internally:
// 0 Rock, 1 Paper, 2 Scissors, 3 Lizard, 4 Spock.
const char *rpsChoiceLabels[] = {
  "ROCK",
  "PAPER",
  "SCISSORS",
  "LIZARD",
  "SPOCK"
};

int rpsP1Choice = -1;
int rpsP2Choice = -1;
int rpsWinner = 0;
int rpsScoreP1 = 0;
int rpsScoreP2 = 0;
int rpsScoreDraw = 0;
const char *rpsPlaceholderTitle = "RPS";

// Tanks Wars keeps one terrain height per screen column. Tanks sit on this
// height map, and explosions modify it directly.
static const int PT_TERRAIN_W = 320;
int ptTerrain[PT_TERRAIN_W];
int ptTankX[2] = {42, 278};
int ptCurrentPlayer = 0;
int ptAngle[2] = {45, 45};
int ptPower[2] = {62, 62};
int ptScoreP1 = 0;
int ptScoreP2 = 0;
int ptWinner = 0;
unsigned long ptNetworkSeed = 1;
const char *ptPlaceholderTitle = "Tanks Wars";

// Breakout is implemented in portrait mode for the current 320x480 setup.
// The bottom strip is reserved for touch controls, keeping gameplay above it.
static const int BREAKOUT_SCREEN_W = 320;
static const int BREAKOUT_SCREEN_H = 480;
static const int BREAKOUT_HUD_H = 34;
static const int BREAKOUT_PLAY_BOTTOM = 396;
static const int BREAKOUT_BRICK_COLS = 8;
static const int BREAKOUT_BRICK_ROWS = 6;
static const int BREAKOUT_BRICK_W = 34;
static const int BREAKOUT_BRICK_H = 16;
static const int BREAKOUT_BRICK_GAP = 3;
static const int BREAKOUT_BRICK_X0 = 20;
static const int BREAKOUT_BRICK_Y0 = 54;
static const int BREAKOUT_BALL_R = 4;
static const int BREAKOUT_PADDLE_W = 72;
static const int BREAKOUT_PADDLE_H = 10;
static const int BREAKOUT_PADDLE_Y = 360;
static const int BREAKOUT_PADDLE_SPEED = 8;
static const unsigned long BREAKOUT_FRAME_MS = 20;

const int btnBreakoutLeftX = 18;
const int btnBreakoutLeftY = 410;
const int btnBreakoutLeftW = 88;
const int btnBreakoutLeftH = 52;

const int btnBreakoutRightX = 214;
const int btnBreakoutRightY = 410;
const int btnBreakoutRightW = 88;
const int btnBreakoutRightH = 52;

const int btnBreakoutMenuX = 116;
const int btnBreakoutMenuY = 422;
const int btnBreakoutMenuW = 88;
const int btnBreakoutMenuH = 36;

bool breakoutBricks[BREAKOUT_BRICK_ROWS][BREAKOUT_BRICK_COLS];
float breakoutBallX = 0.0;
float breakoutBallY = 0.0;
float breakoutBallVX = 0.0;
float breakoutBallVY = 0.0;
int breakoutOldBallX = -1;
int breakoutOldBallY = -1;
int breakoutPaddleX = 0;
int breakoutOldPaddleX = -1;
int breakoutScore = 0;
uint32_t breakoutHiScore = 0;
int breakoutLives = 3;
bool breakoutGameOver = false;
bool breakoutWin = false;
bool breakoutNetworkLossSent = false;
bool breakoutTouchDown = false;
int breakoutTouchX = -1;
int breakoutTouchY = -1;
unsigned long breakoutLastFrame = 0;

// Pong local mode uses a bottom player paddle and a simple CPU paddle at the
// top of the portrait court. First side to five points wins the match.
static const int PONG_HUD_H = 34;
static const int PONG_PLAY_TOP = 40;
static const int PONG_PLAY_BOTTOM = 396;
static const int PONG_PADDLE_W = 76;
static const int PONG_PADDLE_H = 9;
static const int PONG_PLAYER_Y = 356;
static const int PONG_CPU_Y = 58;
static const int PONG_BALL_R = 4;
static const int PONG_SCORE_LIMIT = 5;
static const int PONG_PLAYER_SPEED = 9;
static const int PONG_CPU_SPEED = 5;
static const int PONG_REMOTE_HIT_MARGIN = 14;
static const unsigned long PONG_FRAME_MS = 20;
static const unsigned long PONG_NET_STATE_MS = 33;

const int btnPongLeftX = 18;
const int btnPongLeftY = 410;
const int btnPongLeftW = 88;
const int btnPongLeftH = 52;

const int btnPongRightX = 214;
const int btnPongRightY = 410;
const int btnPongRightW = 88;
const int btnPongRightH = 52;

const int btnPongMenuX = 116;
const int btnPongMenuY = 422;
const int btnPongMenuW = 88;
const int btnPongMenuH = 36;

float pongBallX = 0.0;
float pongBallY = 0.0;
float pongBallVX = 0.0;
float pongBallVY = 0.0;
int pongOldBallX = -1;
int pongOldBallY = -1;
int pongPlayerX = 0;
int pongCpuX = 0;
int pongOldPlayerX = -1;
int pongOldCpuX = -1;
int pongPlayerScore = 0;
int pongCpuScore = 0;
int pongWinsP1 = 0;
int pongWinsP2 = 0;
int pongWinner = 0;
bool pongGameOver = false;
bool pongPlayerWon = false;
bool pongTouchDown = false;
int pongTouchX = -1;
int pongTouchY = -1;
unsigned long pongLastFrame = 0;
int pongLastSentPaddleX = -1;
unsigned long pongLastStateSendTime = 0;

// Snake uses a 20 x 22 grid in the upper play area and a simple directional pad
// in the bottom strip. Network mode is host-authoritative with two visible
// snakes and a shared food item.
static const int SNAKE_GRID_COLS = 20;
static const int SNAKE_GRID_ROWS = 22;
static const int SNAKE_CELL = 14;
static const int SNAKE_BOARD_X = 20;
static const int SNAKE_BOARD_Y = 50;
static const int SNAKE_MAX_LEN = SNAKE_GRID_COLS * SNAKE_GRID_ROWS;
static const unsigned long SNAKE_FRAME_MS = 145;

static const int SNAKE_DIR_UP = 0;
static const int SNAKE_DIR_RIGHT = 1;
static const int SNAKE_DIR_DOWN = 2;
static const int SNAKE_DIR_LEFT = 3;

const int btnSnakeMenuX = 230;
const int btnSnakeMenuY = 6;
const int btnSnakeMenuW = 78;
const int btnSnakeMenuH = 28;

const int btnSnakeUpX = 124;
const int btnSnakeUpY = 365;
const int btnSnakeDirW = 72;
const int btnSnakeDirH = 42;
const int btnSnakeLeftX = 36;
const int btnSnakeLeftY = 412;
const int btnSnakeDownX = 124;
const int btnSnakeDownY = 412;
const int btnSnakeRightX = 212;
const int btnSnakeRightY = 412;

int snakeX[SNAKE_MAX_LEN];
int snakeY[SNAKE_MAX_LEN];
int snakeLength = 0;
int snakeDir = SNAKE_DIR_RIGHT;
int snakeNextDir = SNAKE_DIR_RIGHT;
int snakeFoodX = 0;
int snakeFoodY = 0;
int snakeScore = 0;
uint32_t snakeHiScore = 0;
bool snakeGameOver = false;
unsigned long snakeLastFrame = 0;

int snakeNetX[2][SNAKE_MAX_LEN];
int snakeNetY[2][SNAKE_MAX_LEN];
int snakeNetLength[2] = {0, 0};
int snakeNetDir[2] = {SNAKE_DIR_RIGHT, SNAKE_DIR_LEFT};
int snakeNetNextDir[2] = {SNAKE_DIR_RIGHT, SNAKE_DIR_LEFT};
int snakeNetScore[2] = {0, 0};
bool snakeNetAlive[2] = {false, false};
bool snakeNetGameOver = false;
int snakeNetWinner = 0;
uint8_t snakeDrawOwner[SNAKE_MAX_LEN];
uint8_t snakeDrawHead[SNAKE_MAX_LEN];
int snakeDrawFoodCell = -1;
bool snakeDrawReady = false;

// Ranch Rush local gameplay is a lane-based lasso game ported from the
// standalone sketch into this multi-game console shell.
static const int RR_LANES = 5;
static const int RR_MAX_ANIMALS = 10;
static const int RR_FRAME_MS = 33;
static const unsigned long RR_NET_STATE_MS = 33;
static const int RR_HUD_H = 50;
static const int RR_FIELD_TOP = 60;
static const int RR_FIELD_BOT = 400;
static const int RR_BTN_AREA_TOP = 410;
static const int RR_LANE_SPACING = 60;
static const int RR_LANE_START_Y = RR_FIELD_TOP + 35;

const int btnRrMenuX = 250;
const int btnRrMenuY = 7;
const int btnRrMenuW = 62;
const int btnRrMenuH = 30;

struct RanchAnimal {
  float x;
  int lane;
  float speed;
  bool active;
  uint8_t type;
};

struct RanchPrevAnimal {
  int x;
  int y;
  bool wasActive;
};

int rrLaneY[RR_LANES];
RanchAnimal rrAnimals[RR_MAX_ANIMALS];
RanchPrevAnimal rrPrevAnimals[RR_MAX_ANIMALS];
int rrPlayerLane = 2;
int rrPrevPlayerLane = -1;
int rrPlayerX = 45;
int rrScore = 0;
uint32_t rrHiScore = 0;
int rrLives = 3;
int rrLevel = 1;
bool rrLassoActive = false;
float rrLassoX = 0.0f;
int rrLassoLane = 0;
unsigned long rrLassoStart = 0;
float rrPrevLassoX = 0.0f;
int rrPrevLassoLane = -1;
bool rrPrevLassoActive = false;
unsigned long rrLastSpawn = 0;
unsigned long rrLastFrame = 0;
bool rrGameOver = false;
const int rrNetPlayerX[2] = {45, 96};
int rrNetPlayerLane[2] = {2, 2};
int rrNetPrevPlayerLane[2] = {-1, -1};
int rrNetScore[2] = {0, 0};
int rrNetLives[2] = {3, 3};
bool rrNetLassoActive[2] = {false, false};
float rrNetLassoX[2] = {0.0f, 0.0f};
int rrNetLassoLane[2] = {0, 0};
unsigned long rrNetLassoStart[2] = {0, 0};
float rrNetPrevLassoX[2] = {0.0f, 0.0f};
int rrNetPrevLassoLane[2] = {-1, -1};
bool rrNetPrevLassoActive[2] = {false, false};
bool rrNetGameOver = false;
int rrNetWinner = 0;
bool rrRanchSceneReady = false;
unsigned long rrLastStateSendTime = 0;

// Frogger local gameplay: cross three road lanes, ride logs through three
// water lanes, and fill all five goals to advance to the next level.
static const int FROG_ROWS = 9;
static const int FROG_LANES = 6;
static const int FROG_MAX_OBJECTS = 4;
static const int FROG_GOALS = 5;
static const int FROG_HUD_H = 46;
static const int FROG_FIELD_TOP = 48;
static const int FROG_LANE_H = 38;
static const int FROG_BTN_TOP = FROG_FIELD_TOP + FROG_ROWS * FROG_LANE_H + 2;
static const int FROG_W = 26;
static const int FROG_H = 26;
static const int FROG_STEP_X = 32;
static const unsigned long FROG_FRAME_MS = 33;
static const unsigned long FROG_NET_STATE_MS = 60;

const int btnFrogMenuX = 230;
const int btnFrogMenuY = 6;
const int btnFrogMenuW = 78;
const int btnFrogMenuH = 28;

struct FroggerObject {
  float x;
  int w;
};

struct FroggerLane {
  int row;
  float speed;
  bool isWater;
  uint16_t objColor;
  int numObj;
  FroggerObject objs[FROG_MAX_OBJECTS];
};

int frogRowY[FROG_ROWS];
int frogGoalX[FROG_GOALS];
bool frogGoalFilled[FROG_GOALS];
FroggerLane frogLanes[FROG_LANES];
float frogX = 0.0f;
int frogRow = 0;
float frogPrevX = 0.0f;
int frogPrevRow = 0;
bool frogAlive = true;
bool frogJustJumped = false;
int frogScore = 0;
int frogLives = 3;
int frogLevel = 1;
uint32_t frogHiScore = 0;
bool frogGameOver = false;
bool frogDying = false;
unsigned long frogDeathTime = 0;
unsigned long frogLastFrame = 0;
float frogNetX[2] = {0.0f, 0.0f};
float frogNetPrevX[2] = {0.0f, 0.0f};
int frogNetRow[2] = {0, 0};
int frogNetPrevRow[2] = {0, 0};
bool frogNetAlive[2] = {true, true};
bool frogNetDying[2] = {false, false};
bool frogNetJustJumped[2] = {false, false};
unsigned long frogNetDeathTime[2] = {0, 0};
int frogNetScore[2] = {0, 0};
int frogNetLives[2] = {3, 3};
bool frogNetGameOver = false;
int frogNetWinner = 0;
bool frogNetSceneReady = false;
unsigned long frogLastStateSendTime = 0;
int frogNetInputSeq[2] = {0, 0};
int frogLocalInputSeq = 0;

// Hex Pipes is a flat-top hexagonal pipe-rotation puzzle inspired by
// hexapipes.vercel.app. The local game stores best moves and best time.
static const int HEX_PIPE_COLS = 5;
static const int HEX_PIPE_ROWS = 7;
static const int HEX_PIPE_NUM_CELLS = HEX_PIPE_COLS * HEX_PIPE_ROWS;
static const int HEX_PIPE_HUD_H = 50;
static const int HEX_PIPE_BOARD_TOP = 52;
static const int HEX_PIPE_BTN_TOP = 434;
static const float HEX_PIPE_R = 28.0f;
static const float HEX_PIPE_HORIZ_SP = HEX_PIPE_R * 1.5f;
static const float HEX_PIPE_VERT_SP = HEX_PIPE_R * 1.7320508f;
static const float HEX_PIPE_APOTHEM = HEX_PIPE_R * 0.8660254f;
static const float HEX_PIPE_ORIGIN_X = 76.0f;
static const float HEX_PIPE_ORIGIN_Y = 82.0f;

static const int8_t HEX_PIPE_DCOL_EVEN[6] = {0, 1, 1, 0, -1, -1};
static const int8_t HEX_PIPE_DROW_EVEN[6] = {-1, -1, 0, 1, 0, -1};
static const int8_t HEX_PIPE_DCOL_ODD[6] = {0, 1, 1, 0, -1, -1};
static const int8_t HEX_PIPE_DROW_ODD[6] = {-1, 0, 1, 1, 1, 0};
static const int8_t HEX_PIPE_OPP[6] = {3, 4, 5, 0, 1, 2};

float hexPipeVX[6];
float hexPipeVY[6];
float hexPipeDirDX[6];
float hexPipeDirDY[6];
float hexPipeCellCX[HEX_PIPE_ROWS][HEX_PIPE_COLS];
float hexPipeCellCY[HEX_PIPE_ROWS][HEX_PIPE_COLS];
uint8_t hexPipeMask[HEX_PIPE_ROWS][HEX_PIPE_COLS];

int hexPipeMoves = 0;
int hexPipeElapsedSec = 0;
int hexPipeLastDrawnSec = -1;
int hexPipeLastDrawnMoves = -1;
uint32_t hexPipeBestMoves = 0;
uint32_t hexPipeBestTimeSec = 0;
unsigned long hexPipeStartTime = 0;
unsigned long hexPipeSolvedAt = 0;
const char *hexPipesPlaceholderTitle = "HEX PIPES";
unsigned long hexPipeNetworkSeed = 1;
int hexPipePlayerMoves[2] = {0, 0};
int hexPipePlayerTime[2] = {0, 0};
bool hexPipePlayerSolved[2] = {false, false};
int hexPipeSolveMoves[2] = {0, 0};
int hexPipeSolveTime[2] = {0, 0};
bool hexPipeNetworkGameOver = false;
bool hexPipePendingResult = false;
unsigned long hexPipePendingResultSince = 0;
int hexPipeWinner = 0;
int hexPipeLastSentMoves = -1;
int hexPipeLastSentSec = -1;

int hexPipesLocalPlayerIndex();
void prepareHexPipesNetworkSeed();
void sendNetMessage(const String &msg);

// Frogger uses ESP-NOW for Host/Join because it needs fast symmetric movement:
// each console simulates its own frog and only broadcasts compact events/state.
static const uint8_t FROG_PKT_HELLO = 0;
static const uint8_t FROG_PKT_ACK = 1;
static const uint8_t FROG_PKT_START = 2;
static const uint8_t FROG_PKT_STATE = 3;
static const uint8_t FROG_PKT_GOAL = 4;
static const uint8_t FROG_PKT_OVER = 5;
static const int FROG_ESPNOW_CHANNEL = 1;
static const int FROG_ESPNOW_RX_SIZE = 16;
static const int FROG_ESPNOW_MAX_PACKET = 24;

#pragma pack(push, 1)
struct FrogEspNowHelloPacket {
  uint8_t type;
};

struct FrogEspNowAckPacket {
  uint8_t type;
};

struct FrogEspNowStartPacket {
  uint8_t type;
  uint8_t level;
};

struct FrogEspNowStatePacket {
  uint8_t type;
  uint8_t player;
  float x;
  uint8_t row;
  int16_t score;
  uint8_t lives;
  uint8_t alive;
};

struct FrogEspNowGoalPacket {
  uint8_t type;
  uint8_t slot;
  uint8_t player;
};

struct FrogEspNowOverPacket {
  uint8_t type;
  uint8_t winner;
  int16_t score0;
  int16_t score1;
};
#pragma pack(pop)

struct FrogEspNowRxEntry {
  uint8_t data[FROG_ESPNOW_MAX_PACKET];
  uint8_t mac[6];
  int len;
};

volatile int frogEspRxHead = 0;
volatile int frogEspRxTail = 0;
FrogEspNowRxEntry frogEspRxBuffer[FROG_ESPNOW_RX_SIZE];
uint8_t frogEspPeerMac[6] = {0, 0, 0, 0, 0, 0};
uint8_t frogEspBroadcastMac[6] = {0xFF, 0xFF, 0xFF, 0xFF, 0xFF, 0xFF};
bool frogEspReady = false;
bool frogEspPeerKnown = false;
unsigned long frogEspLastHelloTime = 0;
unsigned long frogEspLastPeerRxTime = 0;

// Touch edge detection and debounce. Touch actions fire once per press, not on
// every loop while the finger is still down.
bool touchWasDown = false;
unsigned long lastTouchTime = 0;
const unsigned long touchDebounceMs = 80;

// ============================================================================
// LAYOUT
// ============================================================================
// All UI geometry lives here so button hitboxes match the drawings and can be
// adjusted without hunting through the touch handlers.
const int screenW = 320;
const int screenH = 480;

const int topBarH = 90;

const int boardX = 20;
const int boardY = 110;
const int boardSize = 280;
const int cellSize = boardSize / 3;

// Shared game menu buttons. Tic Tac Toe, RPSLS, Tanks Wars, Breakout, Pong,
// Snake, Ranch Rush, Frogger, and Hex Pipes all reuse this Local/Host/Join/
// Reset/Back layout so the touch routing stays consistent across games.
const int btnLocalX = 30;
const int btnLocalY = 150;
const int btnLocalW = 260;
const int btnLocalH = 54;

const int btnHostX = 30;
const int btnHostY = 210;
const int btnHostW = 260;
const int btnHostH = 54;

const int btnJoinX = 30;
const int btnJoinY = 270;
const int btnJoinW = 260;
const int btnJoinH = 54;

const int btnResetScoreX = 30;
const int btnResetScoreY = 330;
const int btnResetScoreW = 260;
const int btnResetScoreH = 54;

const int btnMenuX = 90;
const int btnMenuY = 420;
const int btnMenuW = 140;
const int btnMenuH = 40;

const int btnPlayAgainX = 50;
const int btnPlayAgainY = 330;
const int btnPlayAgainW = 220;
const int btnPlayAgainH = 45;

const int btnResultMenuX = 50;
const int btnResultMenuY = 390;
const int btnResultMenuW = 220;
const int btnResultMenuH = 45;

const int btnTttHomeX = 30;
const int btnTttHomeY = 390;
const int btnTttHomeW = 260;
const int btnTttHomeH = 54;

// Games hub page buttons. The hub is paged, so these constants are shared by
// page 1, page 2, and the extra page that contains Hex Pipes and Frogger.
const int btnGamesX = 35;
const int btnGamesTttY = 135;
const int btnGamesRpsY = 205;
const int btnGamesPocketTanksY = 275;
const int btnGamesHomeY = 390;
const int btnGamesW = 250;
const int btnGamesH = 52;
const int btnGamesHomeH = 45;
const int btnGamesNavLeftX = 35;
const int btnGamesNavRightX = 170;
const int btnGamesNavW = 115;
const int btnGamesSnakeY = 135;
const int btnGamesBreakoutY = 205;
const int btnGamesPongY = 275;
const int btnGamesRanchRushY = 335;

const int btnEmptyBackX = 90;
const int btnEmptyBackY = 420;
const int btnEmptyBackW = 140;
const int btnEmptyBackH = 40;

// RPSLS choice wheel geometry and SD image folders. The wheel image is visible,
// while the five choice sectors are invisible touch targets calculated from it.
const int rpsWheelCenterX = 160;
const int rpsWheelCenterY = 250;
const int rpsWheelRadius = 145;
const char *rpsWheelImagePath = "/RPSLS_game/general/rpsls_wheel.raw";
const char *rpsPlayer1WinsPath = "/RPSLS_game/local/player1_wins";
const char *rpsPlayer2WinsPath = "/RPSLS_game/local/player2_wins";
const char *rpsDrawPath = "/RPSLS_game/local/draw";
const char *rpsNetworkWinPath = "/RPSLS_game/win";
const char *rpsNetworkLosePath = "/RPSLS_game/lose";
const int btnRpsMenuX = 90;
const int btnRpsMenuY = 420;
const int btnRpsMenuW = 140;
const int btnRpsMenuH = 40;

// Tanks Wars artillery geometry. These values define terrain, tank sprites,
// projectile animation, explosion damage, and the angle/power/fire controls.
const int ptFieldTop = 0;
const int ptFieldBottom = 355;
const int ptTankW = 22;
const int ptTankH = 12;
const int ptExplosionRadius = 24;
const int ptProjectileRadius = 3;
const unsigned long ptProjectileFrameMs = 24;

const int btnPtAngleDownX = 8;
const int btnPtAngleDownY = 370;
const int btnPtAngleUpX = 86;
const int btnPtAngleUpY = 370;
const int btnPtPowerDownX = 164;
const int btnPtPowerDownY = 370;
const int btnPtPowerUpX = 242;
const int btnPtPowerUpY = 370;
const int btnPtControlW = 70;
const int btnPtControlH = 36;

const int btnPtFireX = 20;
const int btnPtFireY = 424;
const int btnPtFireW = 130;
const int btnPtFireH = 40;

const int btnPtMenuX = 170;
const int btnPtMenuY = 424;
const int btnPtMenuW = 130;
const int btnPtMenuH = 40;

// Home screen RAW asset layout. The background and three button images are read
// from SD when present; the same hitboxes are used by the fallback drawing.
const int homeButtonRawW = 320;
const int homeButtonRawH = 90;

const int homeButtonSlotX = 54;
const int homeButtonSlotW = 213;
const int homeButtonSlotH = 47;

const int homeGamesRawX = homeButtonSlotX;
const int homeGamesRawY = 291;
const int homeSettingsRawX = homeButtonSlotX;
const int homeSettingsRawY = 340;
const int homeExitRawX = homeButtonSlotX;
const int homeExitRawY = 388;

const int homeTouchX = 35;
const int homeTouchW = 250;
const int homeTouchH = 55;
const int homeGamesTouchY = 287;
const int homeSettingsTouchY = 336;
const int homeExitTouchY = 384;

// Settings, Host IP, and Join IP editor geometry. The four fields hold one IP
// octet each, and the same numeric keypad is reused on all IP-entry pages.
const int settingsFieldX = 18;
const int settingsFieldY = 92;
const int settingsFieldW = 62;
const int settingsFieldH = 44;
const int settingsFieldGap = 14;

const int keyPadX = 35;
const int keyPadY = 165;
const int keyPadW = 70;
const int keyPadH = 42;
const int keyPadGapX = 15;
const int keyPadGapY = 11;

const int btnSettingsHomeX = 20;
const int btnSettingsHomeY = 420;
const int btnSettingsHomeW = 130;
const int btnSettingsHomeH = 40;

const int btnSettingsSaveX = 170;
const int btnSettingsSaveY = 420;
const int btnSettingsSaveW = 130;
const int btnSettingsSaveH = 40;

const int btnSettingsMusicX = 60;
const int btnSettingsMusicY = 165;
const int btnSettingsMusicW = 200;
const int btnSettingsMusicH = 56;

const int btnSettingsWifiX = 60;
const int btnSettingsWifiY = 245;
const int btnSettingsWifiW = 200;
const int btnSettingsWifiH = 56;

const int btnMusicToggleX = 45;
const int btnMusicToggleY = 150;
const int btnMusicToggleW = 230;
const int btnMusicToggleH = 62;

const int btnSfxToggleX = 45;
const int btnSfxToggleY = 250;
const int btnSfxToggleW = 230;
const int btnSfxToggleH = 62;

const int btnWifiPrevX = 12;
const int btnWifiSsidY = 54;
const int btnWifiPrevW = 62;
const int btnWifiSsidX = 80;
const int btnWifiSsidW = 160;
const int btnWifiNextX = 246;
const int btnWifiNextW = 62;
const int btnWifiSsidH = 30;

// Join setup geometry. The first page lists scanned WiFi networks, then the
// Join IP page confirms the host address before opening the TCP connection.
const int joinNetworkX = 20;
const int joinNetworkY = 112;
const int joinNetworkW = 280;
const int joinNetworkH = 32;
const int joinNetworkGap = 5;

const int joinKeyPadX = 35;
const int joinKeyPadY = 282;
const int joinKeyPadW = 70;
const int joinKeyPadH = 30;
const int joinKeyPadGapX = 15;
const int joinKeyPadGapY = 6;

const int btnJoinBackX = 4;
const int btnJoinBackY = 430;
const int btnJoinBackW = 74;
const int btnJoinBackH = 38;

const int btnJoinScanX = 83;
const int btnJoinScanY = 430;
const int btnJoinScanW = 74;
const int btnJoinScanH = 38;

const int btnJoinMoreX = 162;
const int btnJoinMoreY = 430;
const int btnJoinMoreW = 74;
const int btnJoinMoreH = 38;

const int btnJoinConnectX = 241;
const int btnJoinConnectY = 430;
const int btnJoinConnectW = 74;
const int btnJoinConnectH = 38;

const int btnJoinIpBackX = 20;
const int btnJoinIpBackY = 420;
const int btnJoinIpBackW = 130;
const int btnJoinIpBackH = 40;

const int btnJoinIpConnectX = 170;
const int btnJoinIpConnectY = 420;
const int btnJoinIpConnectW = 130;
const int btnJoinIpConnectH = 40;

// Host setup geometry. The first page selects the AP SSID, and the second page
// confirms the host IP used by all network games.
const int hostSSIDX = 20;
const int hostSSIDY = 112;
const int hostSSIDW = 280;
const int hostSSIDH = 32;
const int hostSSIDGap = 5;

const int btnHostBackX = 12;
const int btnHostBackY = 430;
const int btnHostBackW = 90;
const int btnHostBackH = 38;

const int btnHostMoreX = 115;
const int btnHostMoreY = 430;
const int btnHostMoreW = 90;
const int btnHostMoreH = 38;

const int btnHostNextX = 218;
const int btnHostNextY = 430;
const int btnHostNextW = 90;
const int btnHostNextH = 38;

const int btnHostIpBackX = 20;
const int btnHostIpBackY = 420;
const int btnHostIpBackW = 130;
const int btnHostIpBackH = 40;

const int btnHostIpStartX = 170;
const int btnHostIpStartY = 420;
const int btnHostIpStartW = 130;
const int btnHostIpStartH = 40;

// ============================================================================
// RAW565 VIDEO PLAYER - /intro/frame_000.raw ... /intro/frame_074.raw
// ============================================================================
// RAW565 assets are stored as RGB565 pixels without headers. Drawing in small
// line blocks keeps RAM usage low while still streaming directly from SD. This
// loader is shared by the boot intro, Home/Games backgrounds, game menu
// backgrounds, RPSLS result screens, and fallback UI assets.
static const int VIDEO_W = 320;
static const int VIDEO_H = 480;
static const int RAW_BLOCK_LINES = 32;
static const int RAW_FRAME_SIZE = VIDEO_W * VIDEO_H * 2;
static const int INTRO_FIRST_FRAME = 0;
static const int INTRO_TOTAL_FRAMES = 75;
static const int INTRO_TARGET_FPS = 65;
static const int INTRO_ROTATION = 0;
static const unsigned long INTRO_FIRST_FRAME_HOLD_MS = 1000;
static const char *GAMES_BACKGROUND_PATH = "/games_screen/games_background.raw";
static const char *TTT_BACKGROUND_PATH = "/tictactoe_game/tictactoe_background.raw";
static const char *RPS_BACKGROUND_PATH = "/RPSLS_game/main_screen/rock_paper_scissors_background.raw";

static uint16_t rawDrawBuffer[VIDEO_W * RAW_BLOCK_LINES];
static uint16_t rawScaleSourceBuffer[homeButtonRawW * homeButtonRawH];
static uint16_t rawScaleLineBuffer[screenW];

// Draws one unscaled RAW565 image. Used for full-screen backgrounds, intro
// frames, and result screens.
bool drawRaw565ImageFromSD(const char *filename, int16_t x, int16_t y, int imageW, int imageH) {
  File rawFile = SD.open(filename, FILE_READ);

  if (!rawFile) {
    Serial.print("Cannot open RAW: ");
    Serial.println(filename);
    return false;
  }

  uint32_t expectedSize = (uint32_t)imageW * imageH * 2;

  if (rawFile.size() != expectedSize) {
    Serial.print("Invalid RAW size: ");
    Serial.print(filename);
    Serial.print(" size=");
    Serial.println(rawFile.size());
    rawFile.close();
    return false;
  }

  if (imageW > VIDEO_W) {
    Serial.print("RAW image is too wide: ");
    Serial.println(filename);
    rawFile.close();
    return false;
  }

  for (int blockY = 0; blockY < imageH; blockY += RAW_BLOCK_LINES) {
    int linesThisBlock = RAW_BLOCK_LINES;

    if (blockY + linesThisBlock > imageH) {
      linesThisBlock = imageH - blockY;
    }

    int bytesToRead = imageW * linesThisBlock * 2;

    digitalWrite(PIN_LCD_CS, HIGH);

    int bytesRead = rawFile.read((uint8_t *)rawDrawBuffer, bytesToRead);

    if (bytesRead != bytesToRead) {
      rawFile.close();
      return false;
    }

    digitalWrite(PIN_SD_CS, HIGH);
    gfx->draw16bitRGBBitmap(x, y + blockY, rawDrawBuffer, imageW, linesThisBlock);
  }

  rawFile.close();
  return true;
}

bool drawRaw565FromSD(const char *filename, int16_t x, int16_t y) {
  return drawRaw565ImageFromSD(filename, x, y, VIDEO_W, VIDEO_H);
}

// Used by the home screen buttons. The source button RAWs are larger than the
// slots in background.raw, so they are nearest-neighbor scaled line by line.
bool drawScaledRaw565ImageFromSD(const char *filename, int16_t x, int16_t y,
                                 int sourceW, int sourceH,
                                 int destW, int destH) {
  if (destW > screenW) return false;
  if (sourceW != homeButtonRawW || sourceH != homeButtonRawH) return false;

  File rawFile = SD.open(filename, FILE_READ);

  if (!rawFile) {
    Serial.print("Cannot open RAW: ");
    Serial.println(filename);
    return false;
  }

  uint32_t expectedSize = (uint32_t)sourceW * sourceH * 2;

  if (rawFile.size() != expectedSize) {
    Serial.print("Invalid RAW size: ");
    Serial.print(filename);
    Serial.print(" size=");
    Serial.println(rawFile.size());
    rawFile.close();
    return false;
  }

  int bytesRead = rawFile.read((uint8_t *)rawScaleSourceBuffer, expectedSize);
  rawFile.close();

  if (bytesRead != (int)expectedSize) {
    Serial.print("RAW read failed: ");
    Serial.println(filename);
    return false;
  }

  for (int dy = 0; dy < destH; dy++) {
    int sy = ((long)dy * sourceH) / destH;

    for (int dx = 0; dx < destW; dx++) {
      int sx = ((long)dx * sourceW) / destW;
      rawScaleLineBuffer[dx] = rawScaleSourceBuffer[sy * sourceW + sx];
    }

    digitalWrite(PIN_SD_CS, HIGH);
    gfx->draw16bitRGBBitmap(x, y + dy, rawScaleLineBuffer, destW, 1);
  }

  return true;
}

void playVideoRaw(const char *folder, int totalFrames, int targetFps) {
  if (!sdReady) return;

  char path[64];
  unsigned long frameTime = 1000UL / targetFps;
  int lastFrame = INTRO_FIRST_FRAME + totalFrames - 1;

  for (int i = INTRO_FIRST_FRAME; i <= lastFrame; i++) {
    unsigned long frameStart = millis();

    snprintf(path, sizeof(path), "%s/frame_%03d.raw", folder, i);
    drawRaw565FromSD(path, 0, 0);

    if (i == INTRO_FIRST_FRAME) {
      delay(INTRO_FIRST_FRAME_HOLD_MS);
    }

    unsigned long used = millis() - frameStart;

    if (used < frameTime) {
      delay(frameTime - used);
    }
  }
}

void playBootIntro() {
  // Intro files are already generated in portrait orientation.
  gfx->setRotation(INTRO_ROTATION);
  gfx->fillScreen(RGB565_BLACK);

  delay(50);
  playVideoRaw("/intro", INTRO_TOTAL_FRAMES, INTRO_TARGET_FPS);

  gfx->setRotation(0);
  gfx->fillScreen(RGB565_BLACK);
}

// ============================================================================
// SCORE STORAGE
// ============================================================================
// Each game has its own Preferences namespace so score resets do not affect
// other games.
// Tic Tac Toe: persistent wins for X, wins for O, and draws.
void loadScore() {
  prefs.begin("ttt_score", true);
  scoreX = prefs.getInt("x", 0);
  scoreO = prefs.getInt("o", 0);
  scoreDraw = prefs.getInt("d", 0);
  prefs.end();
}

void saveScore() {
  prefs.begin("ttt_score", false);
  prefs.putInt("x", scoreX);
  prefs.putInt("o", scoreO);
  prefs.putInt("d", scoreDraw);
  prefs.end();
}

void resetScore() {
  scoreX = 0;
  scoreO = 0;
  scoreDraw = 0;
  saveScore();
}

// Rock-Paper-Scissors-Lizard-Spock: persistent P1 wins, P2 wins, and draws.
void loadRpsScore() {
  prefs.begin("rps_score", true);
  rpsScoreP1 = prefs.getInt("p1", 0);
  rpsScoreP2 = prefs.getInt("p2", 0);
  rpsScoreDraw = prefs.getInt("d", 0);
  prefs.end();
}

void saveRpsScore() {
  prefs.begin("rps_score", false);
  prefs.putInt("p1", rpsScoreP1);
  prefs.putInt("p2", rpsScoreP2);
  prefs.putInt("d", rpsScoreDraw);
  prefs.end();
}

void resetRpsScore() {
  rpsScoreP1 = 0;
  rpsScoreP2 = 0;
  rpsScoreDraw = 0;
  saveRpsScore();
}

// Tanks Wars: persistent match wins for Player 1 and Player 2.
void loadPocketTanksScore() {
  prefs.begin("pt_score", true);
  ptScoreP1 = prefs.getInt("p1", 0);
  ptScoreP2 = prefs.getInt("p2", 0);
  prefs.end();
}

void savePocketTanksScore() {
  prefs.begin("pt_score", false);
  prefs.putInt("p1", ptScoreP1);
  prefs.putInt("p2", ptScoreP2);
  prefs.end();
}

void resetPocketTanksScore() {
  ptScoreP1 = 0;
  ptScoreP2 = 0;
  savePocketTanksScore();
}

// Breakout: persistent single-player high score.
void loadBreakoutScore() {
  prefs.begin("breakout", true);
  breakoutHiScore = prefs.getULong("hiscore", 0);
  prefs.end();
}

void saveBreakoutScore() {
  prefs.begin("breakout", false);
  prefs.putULong("hiscore", breakoutHiScore);
  prefs.end();
}

void resetBreakoutScore() {
  breakoutHiScore = 0;
  saveBreakoutScore();
}

// Pong: persistent match wins for Player 1 and Player 2.
void loadPongScore() {
  prefs.begin("pong_score", true);
  pongWinsP1 = prefs.getInt("p1", 0);
  pongWinsP2 = prefs.getInt("p2", 0);
  prefs.end();
}

void savePongScore() {
  prefs.begin("pong_score", false);
  prefs.putInt("p1", pongWinsP1);
  prefs.putInt("p2", pongWinsP2);
  prefs.end();
}

void resetPongScore() {
  pongWinsP1 = 0;
  pongWinsP2 = 0;
  savePongScore();
}

// Snake: persistent single-player high score.
void loadSnakeScore() {
  prefs.begin("snake", true);
  snakeHiScore = prefs.getULong("hiscore", 0);
  prefs.end();
}

void saveSnakeScore() {
  prefs.begin("snake", false);
  prefs.putULong("hiscore", snakeHiScore);
  prefs.end();
}

void resetSnakeScore() {
  snakeHiScore = 0;
  saveSnakeScore();
}

// Ranch Rush: persistent single-player high score.
void loadRanchRushScore() {
  prefs.begin("ranch", true);
  rrHiScore = prefs.getULong("hiscore_ranch", 0);
  prefs.end();
}

void saveRanchRushScore() {
  prefs.begin("ranch", false);
  prefs.putULong("hiscore_ranch", rrHiScore);
  prefs.end();
}

void resetRanchRushScore() {
  rrHiScore = 0;
  saveRanchRushScore();
}

// Frogger: persistent single-player high score.
void loadFroggerScore() {
  prefs.begin("frogger", true);
  frogHiScore = prefs.getULong("hiscore_frog", 0);
  prefs.end();
}

void saveFroggerScore() {
  prefs.begin("frogger", false);
  prefs.putULong("hiscore_frog", frogHiScore);
  prefs.end();
}

void resetFroggerScore() {
  frogHiScore = 0;
  saveFroggerScore();
}

// Hex Pipes: persistent best move count and best completion time.
void loadHexPipesScore() {
  prefs.begin("pipes", true);
  hexPipeBestMoves = prefs.getUInt("best_moves", 0);
  hexPipeBestTimeSec = prefs.getUInt("best_time", 0);
  prefs.end();
}

void saveHexPipesScore() {
  prefs.begin("pipes", false);
  prefs.putUInt("best_moves", hexPipeBestMoves);
  prefs.putUInt("best_time", hexPipeBestTimeSec);
  prefs.end();
}

void resetHexPipesScore() {
  hexPipeBestMoves = 0;
  hexPipeBestTimeSec = 0;
  saveHexPipesScore();
}

// ============================================================================
// NETWORK SETTINGS
// ============================================================================
// The four editable text fields are the source of truth while the keypad is
// open. Saving clamps them to 0..255 and updates HOST_IP. Settings, Host setup,
// and Join setup all use this same IP editor.
void updateHostIpFromParts() {
  HOST_IP = IPAddress(ipParts[0], ipParts[1], ipParts[2], ipParts[3]);
}

void updateIpTextFromParts() {
  for (int i = 0; i < 4; i++) {
    snprintf(ipFieldText[i], sizeof(ipFieldText[i]), "%u", ipParts[i]);
  }
}

uint8_t parseIpFieldValue(int field) {
  if (field < 0 || field > 3) return 0;

  int value = atoi(ipFieldText[field]);

  if (value < 0) value = 0;
  if (value > 255) value = 255;

  return (uint8_t)value;
}

void applyIpTextToParts() {
  for (int i = 0; i < 4; i++) {
    ipParts[i] = parseIpFieldValue(i);
  }

  updateIpTextFromParts();
  updateHostIpFromParts();
}

void loadNetworkSettings() {
  prefs.begin("ttt_cfg", true);
  ipParts[0] = prefs.getUChar("ip0", 192);
  ipParts[1] = prefs.getUChar("ip1", 168);
  ipParts[2] = prefs.getUChar("ip2", 10);
  ipParts[3] = prefs.getUChar("ip3", 1);
  selectedHostSSIDIndex = prefs.getUChar("ssid", 0);
  prefs.end();

  if (selectedHostSSIDIndex < 0 || selectedHostSSIDIndex >= EPIC_SSID_COUNT) {
    selectedHostSSIDIndex = 0;
  }

  hostSSIDListOffset = (selectedHostSSIDIndex / MAX_HOST_SSID_VISIBLE) * MAX_HOST_SSID_VISIBLE;

  updateIpTextFromParts();
  updateHostIpFromParts();
}

void saveNetworkSettings() {
  applyIpTextToParts();

  prefs.begin("ttt_cfg", false);
  prefs.putUChar("ip0", ipParts[0]);
  prefs.putUChar("ip1", ipParts[1]);
  prefs.putUChar("ip2", ipParts[2]);
  prefs.putUChar("ip3", ipParts[3]);
  prefs.putUChar("ssid", (uint8_t)selectedHostSSIDIndex);
  prefs.end();
}

void loadConsoleSettings() {
  prefs.begin("console", true);
  musicEnabled = prefs.getBool("music", true);
  sfxEnabled = prefs.getBool("sfx", true);
  prefs.end();
}

void saveConsoleSettings() {
  prefs.begin("console", false);
  prefs.putBool("music", musicEnabled);
  prefs.putBool("sfx", sfxEnabled);
  prefs.end();
}

// ============================================================================
// AUDIO
// ============================================================================
// Short audio cues and menu music all share the buzzer, so cue tones briefly
// mute the menu loop instead of fighting it. Menu music is used on non-game
// pages; SFX is used by every game and menu button.
struct MenuMusicNote {
  uint16_t freq;
  uint16_t durationMs;
  uint16_t gapMs;
};

const MenuMusicNote menuMusic[] = {
  {659, 115, 25}, {784, 115, 25}, {988, 145, 35}, {784, 95, 25},
  {880, 115, 25}, {1047, 115, 25}, {1175, 155, 35}, {1047, 95, 25},
  {988, 130, 25}, {880, 110, 25}, {784, 140, 35}, {0, 80, 20},
  {523, 105, 25}, {659, 105, 25}, {784, 125, 25}, {988, 165, 45},
  {1047, 120, 25}, {988, 105, 25}, {880, 120, 25}, {784, 160, 40},
  {659, 120, 25}, {784, 120, 25}, {880, 120, 25}, {1047, 170, 45},
  {1175, 105, 25}, {1319, 105, 25}, {1175, 120, 25}, {988, 165, 45},
  {784, 120, 25}, {880, 120, 25}, {988, 120, 25}, {1319, 210, 80},
  {0, 160, 30}
};

const int menuMusicNoteCount = sizeof(menuMusic) / sizeof(menuMusic[0]);
int menuMusicIndex = 0;
bool menuMusicActive = false;
unsigned long menuMusicNextTime = 0;
unsigned long menuMusicMutedUntil = 0;

bool isGameplayStateForMenuMusic() {
  switch (appState) {
    case STATE_PLAYING:
    case STATE_RPS_CHOICE_P1:
    case STATE_RPS_CHOICE_P2:
    case STATE_RPS_WAITING_CHOICE:
    case STATE_PT_PLAYING:
    case STATE_BREAKOUT_PLAYING:
    case STATE_PONG_PLAYING:
    case STATE_SNAKE_PLAYING:
    case STATE_RR_PLAYING:
    case STATE_FROGGER_PLAYING:
    case STATE_HEX_PIPES_PLAYING:
    case STATE_HEX_PIPES_SOLVED:
      return true;
    default:
      return false;
  }
}

void stopMenuMusic() {
  if (menuMusicActive) {
    noTone(PIN_BUZZER);
    menuMusicActive = false;
  }

  menuMusicNextTime = millis() + 120;
}

void updateMenuMusic() {
  unsigned long now = millis();

  if (!musicEnabled) {
    stopMenuMusic();
    menuMusicIndex = 0;
    return;
  }

  if (isGameplayStateForMenuMusic()) {
    stopMenuMusic();
    menuMusicIndex = 0;
    return;
  }

  if (now < menuMusicMutedUntil) {
    if (menuMusicActive) {
      noTone(PIN_BUZZER);
      menuMusicActive = false;
    }

    return;
  }

  if (now < menuMusicNextTime) return;

  const MenuMusicNote &note = menuMusic[menuMusicIndex];

  if (note.freq == 0) {
    noTone(PIN_BUZZER);
    menuMusicActive = false;
  } else {
    tone(PIN_BUZZER, note.freq, note.durationMs);
    menuMusicActive = true;
  }

  menuMusicNextTime = now + note.durationMs + note.gapMs;
  menuMusicIndex++;

  if (menuMusicIndex >= menuMusicNoteCount) {
    menuMusicIndex = 0;
  }
}

void playPriorityTone(uint16_t freq, uint16_t durationMs) {
  if (!sfxEnabled) return;

  menuMusicActive = false;
  menuMusicMutedUntil = millis() + durationMs + 90;
  tone(PIN_BUZZER, freq, durationMs);
}

// Short audio cues. They are intentionally non-blocking tone() calls.
void beepMove()  { playPriorityTone(1000, 40); }
void beepStart() { playPriorityTone(1400, 70); }
void beepWin()   { playPriorityTone(2200, 180); }
void beepDraw()  { playPriorityTone(1200, 150); }
void beepClick() { playPriorityTone(1600, 60); }

// ============================================================================
// TOUCH
// ============================================================================
// FT6336 touch controller helpers. The raw controller coordinates are mapped
// into the current portrait screen coordinate system.
uint8_t tpReadReg(uint8_t reg) {
  Wire.beginTransmission(FT6336_ADDR);
  Wire.write(reg);
  if (Wire.endTransmission(false) != 0) return 0;

  Wire.requestFrom((int)FT6336_ADDR, 1);
  if (Wire.available()) return Wire.read();

  return 0;
}

bool readTouchScreen(int &sx, int &sy) {
  uint8_t points = tpReadReg(0x02) & 0x0F;
  if (points == 0) return false;

  uint8_t xh = tpReadReg(0x03);
  uint8_t xl = tpReadReg(0x04);
  uint8_t yh = tpReadReg(0x05);
  uint8_t yl = tpReadReg(0x06);

  uint16_t rx = ((xh & 0x0F) << 8) | xl;
  uint16_t ry = ((yh & 0x0F) << 8) | yl;

  sx = map(rx, 0, 320, 0, screenW);
  sy = map(ry, 0, 480, 0, screenH);

  if (sx < 0) sx = 0;
  if (sx >= screenW) sx = screenW - 1;
  if (sy < 0) sy = 0;
  if (sy >= screenH) sy = screenH - 1;

  return true;
}

// ============================================================================
// DRAW HELPERS
// ============================================================================
// Shared primitive drawing helpers used by every screen and every game.
uint16_t rgb888to565(uint8_t r, uint8_t g, uint8_t b) {
  return ((r & 0xF8) << 8) |
         ((g & 0xFC) << 3) |
         (b >> 3);
}

bool inRect(int x, int y, int rx, int ry, int rw, int rh) {
  return (x >= rx && x < rx + rw && y >= ry && y < ry + rh);
}

bool inBoard(int x, int y) {
  return inRect(x, y, boardX, boardY, boardSize, boardSize);
}

void drawCenteredText(const char *txt, int y, int size, uint16_t color) {
  int16_t x1, y1;
  uint16_t w, h;

  gfx->setTextSize(size);
  gfx->getTextBounds((char *)txt, 0, y, &x1, &y1, &w, &h);

  int x = (screenW - w) / 2;

  gfx->setCursor(x, y);
  gfx->setTextColor(color);
  gfx->print(txt);
}

void drawCenteredTextWithShadow(const char *txt, int y, int size, uint16_t color, uint16_t shadowColor) {
  int16_t x1, y1;
  uint16_t w, h;

  gfx->setTextSize(size);
  gfx->getTextBounds((char *)txt, 0, y, &x1, &y1, &w, &h);

  int x = (screenW - w) / 2;

  gfx->setCursor(x + 1, y + 1);
  gfx->setTextColor(shadowColor);
  gfx->print(txt);

  gfx->setCursor(x, y);
  gfx->setTextColor(color);
  gfx->print(txt);
}

void drawPixelText(const char *txt, int x, int y, int size, uint16_t mainColor, uint16_t shadowColor) {
  gfx->setTextSize(size);

  gfx->setCursor(x + 3, y + 3);
  gfx->setTextColor(shadowColor);
  gfx->print(txt);

  gfx->setCursor(x, y);
  gfx->setTextColor(mainColor);
  gfx->print(txt);
}

void drawNeonRect(int x, int y, int w, int h, uint16_t coreColor) {
  uint16_t arcadeBlue = rgb888to565(0, 65, 210);
  uint16_t arcadeOrange = rgb888to565(255, 128, 0);

  gfx->drawRoundRect(x - 3, y - 3, w + 6, h + 6, 8, RGB565_CYAN);
  gfx->drawRoundRect(x - 2, y - 2, w + 4, h + 4, 7, arcadeBlue);
  gfx->drawRoundRect(x - 1, y - 1, w + 2, h + 2, 6, RGB565_WHITE);
  gfx->drawRoundRect(x, y, w, h, 6, coreColor);

  if (w > 8 && h > 8) {
    gfx->drawRoundRect(x + 2, y + 2, w - 4, h - 4, 5, arcadeOrange);
  }
}

void fillArcadeGradient() {
  for (int y = 0; y < screenH; y++) {
    uint8_t b = map(y, 0, screenH, 28, 4);
    uint8_t r = map(y, 0, screenH, 8, 0);
    uint8_t g = map(y, 0, screenH, 5, 0);

    gfx->drawLine(0, y, screenW - 1, y, rgb888to565(r, g, b));
  }
}

void drawArcadeStars() {
  for (int i = 0; i < 100; i++) {
    int x = (i * 47 + 23) % screenW;
    int y = (i * 71 + 11) % 145;
    uint16_t color;

    switch (i % 5) {
      case 0: color = RGB565_YELLOW; break;
      case 1: color = RGB565_CYAN; break;
      case 2: color = RGB565_RED; break;
      case 3: color = rgb888to565(255, 0, 180); break;
      default: color = RGB565_WHITE; break;
    }

    gfx->drawPixel(x, y, color);

    if (i % 7 == 0) {
      gfx->drawLine(x - 2, y, x + 2, y, color);
      gfx->drawLine(x, y - 2, x, y + 2, color);
    }
  }
}

void drawArcadeCabinets() {
  uint16_t cabinetFill = rgb888to565(18, 8, 42);
  uint16_t arcadeBlue = rgb888to565(0, 65, 210);
  uint16_t arcadeMagenta = rgb888to565(255, 0, 180);
  uint16_t arcadeGreen = rgb888to565(0, 255, 90);

  gfx->fillRect(0, 220, 35, 180, cabinetFill);
  gfx->drawRect(0, 220, 35, 180, arcadeMagenta);
  gfx->drawLine(35, 220, 55, 260, arcadeBlue);
  gfx->drawLine(35, 400, 55, 440, arcadeBlue);
  gfx->drawRect(6, 250, 22, 28, RGB565_CYAN);
  gfx->setTextSize(1);
  gfx->setTextColor(arcadeGreen);
  gfx->setCursor(5, 285);
  gfx->print("INSERT");
  gfx->setCursor(8, 295);
  gfx->print("COIN");

  gfx->fillRect(285, 220, 35, 180, cabinetFill);
  gfx->drawRect(285, 220, 35, 180, arcadeMagenta);
  gfx->drawLine(285, 220, 265, 260, arcadeBlue);
  gfx->drawLine(285, 400, 265, 440, arcadeBlue);
  gfx->drawRect(292, 250, 22, 28, RGB565_CYAN);
  gfx->setTextColor(arcadeGreen);
  gfx->setCursor(291, 285);
  gfx->print("1UP");
  gfx->setCursor(289, 295);
  gfx->print("HIGH");
  gfx->setCursor(289, 305);
  gfx->print("SCORE");
}

void drawArcadeFloor() {
  int horizon = 365;
  uint16_t floorLine = rgb888to565(45, 15, 90);
  uint16_t rayLine = rgb888to565(30, 20, 85);

  for (int y = horizon; y < screenH; y += 16) {
    gfx->drawLine(0, y, screenW - 1, y, floorLine);
  }

  for (int x = -120; x < screenW + 120; x += 28) {
    gfx->drawLine(screenW / 2, horizon, x, screenH - 1, rayLine);
  }

  gfx->drawLine(0, horizon, screenW - 1, horizon, rgb888to565(0, 65, 210));
}

void drawJoystickDecor() {
  uint16_t arcadeOrange = rgb888to565(255, 128, 0);
  uint16_t arcadeGray = rgb888to565(150, 150, 170);
  uint16_t darkBase = rgb888to565(20, 20, 40);

  gfx->fillCircle(32, 430, 12, RGB565_RED);
  gfx->drawCircle(32, 430, 13, arcadeOrange);
  gfx->drawLine(32, 442, 28, 465, arcadeGray);
  gfx->drawLine(32, 442, 36, 465, arcadeGray);
  gfx->fillRoundRect(10, 458, 44, 16, 8, darkBase);
  gfx->drawRoundRect(10, 458, 44, 16, 8, RGB565_CYAN);

  gfx->fillCircle(250, 438, 12, rgb888to565(0, 65, 210));
  gfx->drawCircle(250, 438, 13, RGB565_CYAN);
  gfx->fillCircle(285, 438, 12, arcadeOrange);
  gfx->drawCircle(285, 438, 13, RGB565_YELLOW);

  gfx->setTextSize(3);
  gfx->setTextColor(RGB565_RED);
  gfx->setCursor(72, 430);
  gfx->print("X");

  gfx->setTextColor(RGB565_CYAN);
  gfx->setCursor(185, 430);
  gfx->print("O");
}

void drawArcadeTitle() {
  uint16_t signFill = rgb888to565(12, 12, 35);
  uint16_t arcadeOrange = rgb888to565(255, 128, 0);
  uint16_t arcadeBlue = rgb888to565(0, 65, 210);

  gfx->fillRoundRect(13, 20, 294, 74, 10, signFill);
  gfx->drawRoundRect(13, 20, 294, 74, 10, arcadeOrange);
  gfx->drawRoundRect(17, 24, 286, 66, 8, RGB565_CYAN);
  gfx->drawRoundRect(20, 27, 280, 60, 7, RGB565_YELLOW);

  for (int x = 30; x < 292; x += 17) {
    gfx->fillCircle(x, 31, 3, arcadeOrange);
    gfx->drawCircle(x, 31, 4, RGB565_YELLOW);
    gfx->fillCircle(x, 82, 3, arcadeOrange);
    gfx->drawCircle(x, 82, 4, RGB565_YELLOW);
  }

  drawPixelText("TIC", 31, 42, 4, RGB565_RED, RGB565_YELLOW);
  drawPixelText("TAC", 114, 42, 4, RGB565_YELLOW, RGB565_RED);
  drawPixelText("TOE", 207, 42, 4, RGB565_CYAN, arcadeBlue);

  gfx->setTextSize(3);
  gfx->setTextColor(RGB565_YELLOW);
  gfx->setCursor(145, 0);
  gfx->print("*");

  gfx->setTextSize(4);
  gfx->setTextColor(RGB565_RED);
  gfx->setCursor(85, 105);
  gfx->print("X");

  gfx->setTextColor(RGB565_CYAN);
  gfx->setCursor(210, 105);
  gfx->print("O");

  int miniX = 132;
  int miniY = 103;
  int miniCell = 17;
  const char *miniMarks = "XOXXOXOXO";

  gfx->drawRect(miniX, miniY, miniCell * 3, miniCell * 3, RGB565_CYAN);
  gfx->drawLine(miniX + miniCell, miniY, miniX + miniCell, miniY + miniCell * 3, RGB565_CYAN);
  gfx->drawLine(miniX + miniCell * 2, miniY, miniX + miniCell * 2, miniY + miniCell * 3, RGB565_CYAN);
  gfx->drawLine(miniX, miniY + miniCell, miniX + miniCell * 3, miniY + miniCell, RGB565_CYAN);
  gfx->drawLine(miniX, miniY + miniCell * 2, miniX + miniCell * 3, miniY + miniCell * 2, RGB565_CYAN);

  gfx->setTextSize(2);

  for (int i = 0; i < 9; i++) {
    int cellX = miniX + (i % 3) * miniCell + 3;
    int cellY = miniY + (i / 3) * miniCell + 2;

    gfx->setCursor(cellX, cellY);
    gfx->setTextColor(miniMarks[i] == 'X' ? RGB565_RED : RGB565_CYAN);
    gfx->print(miniMarks[i]);
  }
}

void drawGamesArcadeTitle() {
  uint16_t signFill = rgb888to565(12, 12, 35);
  uint16_t arcadeOrange = rgb888to565(255, 128, 0);
  uint16_t arcadeBlue = rgb888to565(0, 65, 210);
  uint16_t arcadeMagenta = rgb888to565(255, 0, 180);

  gfx->fillRoundRect(18, 18, 284, 82, 10, signFill);
  gfx->drawRoundRect(18, 18, 284, 82, 10, arcadeMagenta);
  gfx->drawRoundRect(22, 22, 276, 74, 8, RGB565_CYAN);
  gfx->drawRoundRect(26, 26, 268, 66, 7, arcadeOrange);

  for (int x = 36; x < 286; x += 18) {
    gfx->fillCircle(x, 29, 3, arcadeOrange);
    gfx->drawCircle(x, 29, 4, RGB565_YELLOW);
    gfx->fillCircle(x, 89, 3, arcadeBlue);
    gfx->drawCircle(x, 89, 4, RGB565_CYAN);
  }

  drawPixelText("GAMES", 100, 43, 4, RGB565_YELLOW, RGB565_RED);
  drawPixelText("SELECT GAME", 70, 108, 2, RGB565_CYAN, arcadeBlue);

  gfx->fillCircle(46, 114, 7, RGB565_RED);
  gfx->drawCircle(46, 114, 8, RGB565_YELLOW);
  gfx->fillCircle(274, 114, 7, arcadeBlue);
  gfx->drawCircle(274, 114, 8, RGB565_CYAN);
}

void drawHomeArcadeTitle() {
  uint16_t signFill = rgb888to565(12, 12, 35);
  uint16_t arcadeOrange = rgb888to565(255, 128, 0);
  uint16_t arcadeBlue = rgb888to565(0, 65, 210);
  uint16_t arcadeMagenta = rgb888to565(255, 0, 180);

  gfx->fillRoundRect(18, 18, 284, 82, 10, signFill);
  gfx->drawRoundRect(18, 18, 284, 82, 10, arcadeMagenta);
  gfx->drawRoundRect(22, 22, 276, 74, 8, RGB565_CYAN);
  gfx->drawRoundRect(26, 26, 268, 66, 7, arcadeOrange);

  for (int x = 36; x < 286; x += 18) {
    gfx->fillCircle(x, 29, 3, arcadeOrange);
    gfx->drawCircle(x, 29, 4, RGB565_YELLOW);
    gfx->fillCircle(x, 89, 3, arcadeBlue);
    gfx->drawCircle(x, 89, 4, RGB565_CYAN);
  }

  drawPixelText("HOME", 112, 43, 4, RGB565_YELLOW, RGB565_RED);
  drawPixelText("MAIN MENU", 106, 108, 2, RGB565_CYAN, arcadeBlue);

  gfx->fillCircle(46, 114, 7, RGB565_RED);
  gfx->drawCircle(46, 114, 8, RGB565_YELLOW);
  gfx->fillCircle(274, 114, 7, arcadeBlue);
  gfx->drawCircle(274, 114, 8, RGB565_CYAN);
}

// Tic Tac Toe menu background. Prefer the SD asset, then fall back to generated
// arcade art so the game menu still works without the card files.
void drawTicTacToeArcadeHome() {
  if (sdReady && SD.exists(TTT_BACKGROUND_PATH)) {
    if (drawRaw565ImageFromSD(TTT_BACKGROUND_PATH, 0, 0, screenW, screenH)) {
      return;
    }
  }

  fillArcadeGradient();
  drawArcadeStars();
  drawArcadeCabinets();
  drawArcadeFloor();
  drawJoystickDecor();
  drawArcadeTitle();
}

// Games hub background. Used by every Games page before drawing the game list.
void drawGamesArcadeBackground() {
  if (sdReady && SD.exists(GAMES_BACKGROUND_PATH)) {
    if (drawRaw565ImageFromSD(GAMES_BACKGROUND_PATH, 0, 0, screenW, screenH)) {
      return;
    }
  }

  fillArcadeGradient();
  drawArcadeStars();
  drawArcadeCabinets();
  drawArcadeFloor();
  drawGamesArcadeTitle();
}

// Main Home background fallback. Used only when /home_screen RAW assets are
// missing or the SD card is unavailable.
void drawHomeArcadeBackground() {
  fillArcadeGradient();
  drawArcadeStars();
  drawArcadeCabinets();
  drawArcadeFloor();
  drawHomeArcadeTitle();
}

// RPSLS menu background helpers. These draw the fallback Rock-Paper-Scissors
// game menu when the SD-provided background is not available.
void drawRpsHomeGradientBackground() {
  for (int y = 0; y < screenH; y++) {
    uint8_t r = map(y, 0, screenH, 5, 0);
    uint8_t g = map(y, 0, screenH, 6, 0);
    uint8_t b = map(y, 0, screenH, 45, 8);

    gfx->drawLine(0, y, screenW - 1, y, rgb888to565(r, g, b));
  }
}

void drawRpsHomeStars() {
  for (int i = 0; i < 130; i++) {
    int x = (i * 41 + 19) % screenW;
    int y = (i * 67 + 11) % screenH;
    uint16_t color;

    switch (i % 6) {
      case 0: color = RGB565_CYAN; break;
      case 1: color = rgb888to565(255, 0, 180); break;
      case 2: color = RGB565_YELLOW; break;
      case 3: color = RGB565_RED; break;
      case 4: color = RGB565_GREEN; break;
      default: color = RGB565_BLUE; break;
    }

    gfx->drawPixel(x, y, color);

    if (i % 13 == 0) {
      gfx->drawLine(x - 3, y, x + 3, y, color);
      gfx->drawLine(x, y - 3, x, y + 3, color);
    }

    if (i % 29 == 0) {
      gfx->fillRect(x, y, 3, 3, color);
    }
  }
}

void drawRpsBackWall() {
  for (int y = 120; y < 260; y += 14) {
    gfx->drawLine(42, y, 277, y, rgb888to565(10, 10, 42));
  }

  for (int y = 128; y < 260; y += 28) {
    for (int x = 50; x < 275; x += 34) {
      gfx->drawLine(x, y, x, y + 14, rgb888to565(8, 8, 35));
    }
  }

  gfx->drawLine(35, 263, 285, 263, rgb888to565(15, 25, 80));
  gfx->drawLine(35, 265, 285, 265, RGB565_BLUE);
}

void drawRpsHomeFloor() {
  int horizon = 270;
  int centerX = screenW / 2;

  for (int y = horizon; y < screenH; y++) {
    uint8_t b = map(y, horizon, screenH, 30, 5);
    gfx->drawLine(0, y, screenW - 1, y, rgb888to565(0, 3, b));
  }

  for (int y = horizon; y < screenH; y += 17) {
    gfx->drawLine(0, y, screenW - 1, y, rgb888to565(20, 20, 90));
  }

  for (int x = -130; x < screenW + 130; x += 27) {
    gfx->drawLine(centerX, horizon, x, screenH - 1, rgb888to565(20, 15, 85));
  }

  for (int i = 0; i < 28; i++) {
    int x = (i * 37 + 7) % screenW;
    int y = 285 + (i * 31) % 170;
    uint16_t color = (i % 3 == 0) ? rgb888to565(255, 0, 180) :
                     (i % 3 == 1) ? RGB565_CYAN : RGB565_BLUE;

    gfx->drawLine(x, y, x + 16 + (i % 5) * 6, y, color);
  }

  for (int y = 286; y < 410; y += 6) {
    gfx->drawLine(150, y, 170, y, rgb888to565(0, 30, 110));
    gfx->drawLine(156, y, 164, y, RGB565_CYAN);
  }
}

void drawRpsLeftCabinet() {
  int x = 0;
  int y = 132;
  uint16_t magenta = rgb888to565(255, 0, 180);
  uint16_t orange = rgb888to565(255, 128, 0);
  uint16_t gray = rgb888to565(150, 150, 170);

  gfx->fillRoundRect(x, y, 42, 150, 4, rgb888to565(5, 5, 24));
  gfx->drawRoundRect(x, y, 42, 150, 4, magenta);
  gfx->drawLine(42, y, 58, y + 32, RGB565_BLUE);
  gfx->drawLine(42, y + 150, 58, y + 118, RGB565_BLUE);
  gfx->fillRect(7, y + 24, 28, 38, rgb888to565(0, 8, 40));
  gfx->drawRect(7, y + 24, 28, 38, RGB565_CYAN);

  gfx->setTextSize(1);
  gfx->setTextColor(magenta);
  gfx->setCursor(6, y + 6);
  gfx->print("INSERT");
  gfx->setCursor(10, y + 17);
  gfx->print("COIN");

  gfx->drawLine(11, y + 55, 30, y + 36, RGB565_GREEN);
  gfx->fillCircle(21, y + 83, 5, RGB565_RED);
  gfx->drawLine(21, y + 88, 21, y + 103, gray);
  gfx->fillCircle(14, y + 112, 3, RGB565_RED);
  gfx->fillCircle(25, y + 113, 3, orange);
  gfx->fillRect(10, y + 128, 22, 16, rgb888to565(2, 3, 18));
  gfx->drawRect(10, y + 128, 22, 16, RGB565_BLUE);
}

void drawRpsRightCabinet() {
  int x = 278;
  int y = 132;
  uint16_t magenta = rgb888to565(255, 0, 180);
  uint16_t orange = rgb888to565(255, 128, 0);
  uint16_t gray = rgb888to565(150, 150, 170);

  gfx->fillRoundRect(x, y, 42, 150, 4, rgb888to565(5, 5, 24));
  gfx->drawRoundRect(x, y, 42, 150, 4, RGB565_BLUE);
  gfx->drawLine(x, y, x - 16, y + 32, magenta);
  gfx->drawLine(x, y + 150, x - 16, y + 118, magenta);
  gfx->fillRect(x + 7, y + 24, 28, 38, rgb888to565(0, 8, 40));
  gfx->drawRect(x + 7, y + 24, 28, 38, RGB565_CYAN);

  gfx->setTextSize(1);
  gfx->setTextColor(magenta);
  gfx->setCursor(x + 8, y + 6);
  gfx->print("HIGH");
  gfx->setCursor(x + 6, y + 17);
  gfx->print("SCORE");
  gfx->setCursor(x + 10, y + 28);
  gfx->print("1984");

  gfx->fillTriangle(x + 22, y + 39, x + 15, y + 58, x + 29, y + 58, RGB565_RED);
  gfx->fillRect(x + 18, y + 54, 8, 7, RGB565_WHITE);
  gfx->fillCircle(x + 22, y + 83, 5, RGB565_RED);
  gfx->drawLine(x + 22, y + 88, x + 22, y + 103, gray);
  gfx->fillCircle(x + 14, y + 112, 3, RGB565_BLUE);
  gfx->fillCircle(x + 28, y + 113, 3, RGB565_YELLOW);
  gfx->fillRect(x + 10, y + 128, 22, 16, rgb888to565(2, 3, 18));
  gfx->drawRect(x + 10, y + 128, 22, 16, RGB565_BLUE);
}

void drawRpsSideDecorations() {
  uint16_t magenta = rgb888to565(255, 0, 180);

  gfx->setTextSize(2);
  gfx->setTextColor(RGB565_CYAN);
  gfx->setCursor(10, 58);
  gfx->print("*");
  gfx->setTextColor(magenta);
  gfx->setCursor(286, 70);
  gfx->print("<3");
  gfx->setTextColor(RGB565_YELLOW);
  gfx->setCursor(270, 22);
  gfx->print("*");
  gfx->setTextColor(RGB565_CYAN);
  gfx->setCursor(36, 18);
  gfx->print("*");
}

void drawRpsOuterTitleFrame(int x, int y, int w, int h) {
  uint16_t magenta = rgb888to565(255, 0, 180);

  gfx->fillRoundRect(x, y, w, h, 12, rgb888to565(3, 2, 25));
  gfx->drawRoundRect(x - 5, y - 5, w + 10, h + 10, 13, magenta);
  gfx->drawRoundRect(x - 3, y - 3, w + 6, h + 6, 12, magenta);
  gfx->drawRoundRect(x - 1, y - 1, w + 2, h + 2, 11, magenta);
  gfx->drawRoundRect(x + 6, y + 6, w - 12, h - 12, 10, RGB565_CYAN);
  gfx->drawRoundRect(x + 9, y + 9, w - 18, h - 18, 8, RGB565_BLUE);
  gfx->fillRect(x + 5, y + 52, 12, 42, rgb888to565(0, 0, 20));
  gfx->fillRect(x + w - 17, y + 52, 12, 42, rgb888to565(0, 0, 20));
  gfx->drawLine(x + 28, y + h - 14, x + w - 28, y + h - 14, magenta);
}

void drawRpsTitleSign() {
  int x = 42;
  int y = 18;
  int w = 236;
  int h = 122;
  uint16_t magenta = rgb888to565(255, 0, 180);
  uint16_t orange = rgb888to565(255, 128, 0);
  uint16_t gray = rgb888to565(150, 150, 170);

  drawRpsOuterTitleFrame(x, y, w, h);
  drawPixelText("ROCK", 91, 32, 4, gray, RGB565_BLACK);
  drawPixelText("PAPER", 64, 64, 4, RGB565_WHITE, RGB565_BLUE);
  drawPixelText("SCISSORS", 46, 96, 3, RGB565_CYAN, RGB565_BLUE);

  gfx->fillRoundRect(87, 133, 146, 25, 6, rgb888to565(4, 2, 12));
  gfx->drawRoundRect(87, 133, 146, 25, 6, magenta);
  gfx->drawRoundRect(90, 136, 140, 19, 5, RGB565_BLUE);

  gfx->setTextSize(2);
  gfx->setTextColor(RGB565_GREEN);
  gfx->setCursor(102, 139);
  gfx->print("LIZARD");
  gfx->setTextColor(orange);
  gfx->setCursor(178, 139);
  gfx->print("SPOCK");
}

void drawRpsBottomRail() {
  uint16_t magenta = rgb888to565(255, 0, 180);
  uint16_t orange = rgb888to565(255, 128, 0);
  uint16_t gray = rgb888to565(150, 150, 170);

  gfx->fillRect(0, 410, screenW, 70, rgb888to565(3, 4, 16));
  gfx->drawLine(0, 410, screenW - 1, 410, magenta);
  gfx->drawLine(0, 413, screenW - 1, 413, RGB565_BLUE);

  gfx->drawLine(45, 430, 45, 462, gray);
  gfx->drawLine(46, 430, 46, 462, RGB565_WHITE);
  gfx->fillCircle(45, 426, 14, RGB565_RED);
  gfx->drawCircle(45, 426, 15, orange);
  gfx->fillCircle(40, 420, 3, RGB565_WHITE);
  gfx->fillRoundRect(17, 456, 56, 18, 9, rgb888to565(5, 7, 22));
  gfx->drawRoundRect(17, 456, 56, 18, 9, RGB565_BLUE);
  gfx->drawRoundRect(25, 459, 40, 12, 6, magenta);

  gfx->fillCircle(252, 452, 12, magenta);
  gfx->drawCircle(252, 452, 13, RGB565_WHITE);
  gfx->fillCircle(286, 452, 12, RGB565_BLUE);
  gfx->drawCircle(286, 452, 13, RGB565_CYAN);
}

void drawRpsArcadeHome() {
  if (sdReady && SD.exists(RPS_BACKGROUND_PATH)) {
    if (drawRaw565ImageFromSD(RPS_BACKGROUND_PATH, 0, 0, screenW, screenH)) {
      return;
    }
  }

  drawRpsHomeGradientBackground();
  drawRpsHomeStars();
  drawRpsBackWall();
  drawRpsHomeFloor();
  drawRpsLeftCabinet();
  drawRpsRightCabinet();
  drawRpsSideDecorations();
  drawRpsTitleSign();
  drawRpsBottomRail();
  gfx->drawRoundRect(2, 2, screenW - 4, screenH - 4, 10, rgb888to565(10, 20, 80));
  gfx->drawRoundRect(5, 5, screenW - 10, screenH - 10, 8, rgb888to565(30, 0, 70));
}

void drawTanksWarsTitleSign() {
  uint16_t signFill = rgb888to565(12, 10, 28);
  uint16_t arcadeOrange = rgb888to565(255, 128, 0);
  uint16_t arcadeBlue = rgb888to565(0, 65, 210);
  uint16_t arcadeMagenta = rgb888to565(255, 0, 180);
  uint16_t tankGreen = rgb888to565(80, 180, 70);

  gfx->fillRoundRect(16, 18, 288, 96, 10, signFill);
  gfx->drawRoundRect(16, 18, 288, 96, 10, tankGreen);
  gfx->drawRoundRect(20, 22, 280, 88, 8, RGB565_CYAN);
  gfx->drawRoundRect(24, 26, 272, 80, 7, arcadeOrange);

  for (int x = 36; x < 286; x += 20) {
    gfx->fillCircle(x, 31, 3, arcadeOrange);
    gfx->drawCircle(x, 31, 4, RGB565_YELLOW);
    gfx->fillCircle(x, 101, 3, arcadeBlue);
    gfx->drawCircle(x, 101, 4, RGB565_CYAN);
  }

  drawPixelText("TANKS", 66, 39, 4, RGB565_YELLOW, RGB565_RED);
  drawPixelText("WARS", 92, 73, 4, RGB565_CYAN, arcadeBlue);

  gfx->fillCircle(44, 120, 6, arcadeMagenta);
  gfx->drawCircle(44, 120, 7, RGB565_YELLOW);
  gfx->fillCircle(276, 120, 6, arcadeMagenta);
  gfx->drawCircle(276, 120, 7, RGB565_YELLOW);
}

void drawTanksWarsTankDecor(int x, int y, bool facingRight, uint16_t bodyColor) {
  int dir = facingRight ? 1 : -1;
  uint16_t trackColor = rgb888to565(22, 24, 28);

  gfx->fillRoundRect(x - 22, y + 8, 44, 10, 5, trackColor);
  gfx->drawRoundRect(x - 22, y + 8, 44, 10, 5, RGB565_WHITE);

  for (int i = -14; i <= 14; i += 14) {
    gfx->fillCircle(x + i, y + 13, 4, rgb888to565(70, 80, 80));
  }

  gfx->fillRoundRect(x - 16, y, 32, 12, 4, bodyColor);
  gfx->drawRoundRect(x - 16, y, 32, 12, 4, RGB565_WHITE);
  gfx->fillCircle(x, y, 6, RGB565_YELLOW);

  for (int offset = -1; offset <= 1; offset++) {
    gfx->drawLine(x, y - 1 + offset, x + dir * 28, y - 16 + offset, RGB565_YELLOW);
  }
}

void drawTanksWarsBattlefieldDecor() {
  uint16_t ridgeA = rgb888to565(28, 78, 48);
  uint16_t ridgeB = rgb888to565(42, 118, 58);
  uint16_t arcadeBlue = rgb888to565(0, 65, 210);

  for (int x = 0; x < screenW; x += 8) {
    int y = 338 + (int)(sin((float)x * 0.055f) * 12.0f);
    gfx->fillRect(x, y, 8, 28, (x % 16 == 0) ? ridgeA : ridgeB);
  }

  for (int x = 0; x < screenW; x += 22) {
    gfx->drawLine(160, 365, x, screenH - 1, rgb888to565(18, 22, 70));
  }

  gfx->drawLine(0, 365, screenW - 1, 365, arcadeBlue);

  drawTanksWarsTankDecor(58, 320, true, RGB565_RED);
  drawTanksWarsTankDecor(262, 320, false, RGB565_BLUE);

  for (int i = 0; i < 14; i++) {
    int px = 86 + i * 11;
    int py = 260 - (int)(sin((float)i * 0.24f) * 24.0f);
    gfx->drawPixel(px, py, RGB565_YELLOW);

    if (i % 3 == 0) {
      gfx->drawCircle(px, py, 2, RGB565_RED);
    }
  }
}

void drawTanksWarsArcadeHome() {
  fillArcadeGradient();
  drawArcadeStars();
  drawArcadeCabinets();
  drawArcadeFloor();
  drawTanksWarsBattlefieldDecor();
  drawTanksWarsTitleSign();
}

void drawBreakoutTitleSign() {
  uint16_t signFill = rgb888to565(12, 10, 28);
  uint16_t arcadeOrange = rgb888to565(255, 128, 0);
  uint16_t arcadeBlue = rgb888to565(0, 65, 210);
  uint16_t arcadeMagenta = rgb888to565(255, 0, 180);

  gfx->fillRoundRect(16, 18, 288, 96, 10, signFill);
  gfx->drawRoundRect(16, 18, 288, 96, 10, arcadeMagenta);
  gfx->drawRoundRect(20, 22, 280, 88, 8, RGB565_CYAN);
  gfx->drawRoundRect(24, 26, 272, 80, 7, arcadeOrange);

  for (int x = 36; x < 286; x += 20) {
    gfx->fillCircle(x, 31, 3, arcadeOrange);
    gfx->drawCircle(x, 31, 4, RGB565_YELLOW);
    gfx->fillCircle(x, 101, 3, arcadeBlue);
    gfx->drawCircle(x, 101, 4, RGB565_CYAN);
  }

  drawPixelText("BREAK", 51, 38, 4, RGB565_YELLOW, RGB565_RED);
  drawPixelText("OUT", 116, 72, 4, RGB565_CYAN, arcadeBlue);
}

void drawBreakoutBrickWallDecor() {
  uint16_t brickColors[] = {
    rgb888to565(230, 40, 30),
    rgb888to565(240, 130, 20),
    rgb888to565(240, 220, 20),
    rgb888to565(30, 220, 40),
    rgb888to565(20, 90, 220)
  };

  int brickW = 38;
  int brickH = 14;
  int startY = 128;

  for (int row = 0; row < 5; row++) {
    int offset = (row % 2 == 0) ? 10 : 30;

    for (int x = offset; x < screenW - 10; x += brickW + 4) {
      uint16_t color = brickColors[row];
      gfx->fillRoundRect(x, startY + row * 18, brickW, brickH, 3, color);
      gfx->drawRoundRect(x, startY + row * 18, brickW, brickH, 3, RGB565_BLACK);
      gfx->drawLine(x + 3, startY + row * 18 + 2, x + brickW - 5,
                    startY + row * 18 + 2, RGB565_WHITE);
    }
  }
}

void drawBreakoutPlayfieldDecor() {
  uint16_t arcadeBlue = rgb888to565(0, 65, 210);
  uint16_t arcadeMagenta = rgb888to565(255, 0, 180);
  uint16_t darkPanel = rgb888to565(3, 5, 22);

  gfx->fillRoundRect(40, 224, 240, 118, 8, darkPanel);
  gfx->drawRoundRect(40, 224, 240, 118, 8, arcadeBlue);
  gfx->drawRoundRect(44, 228, 232, 110, 7, arcadeMagenta);

  for (int i = 0; i < 8; i++) {
    int x = 72 + i * 24;
    int y = 250 + (int)(sin((float)i * 0.75f) * 28.0f);
    gfx->drawPixel(x, y, RGB565_WHITE);
    gfx->drawCircle(x, y, 2, RGB565_CYAN);
  }

  gfx->fillCircle(222, 244, 7, RGB565_WHITE);
  gfx->drawCircle(222, 244, 8, RGB565_YELLOW);

  gfx->fillRoundRect(112, 315, 96, 12, 6, RGB565_RED);
  gfx->drawRoundRect(112, 315, 96, 12, 6, RGB565_WHITE);
  gfx->fillRect(124, 318, 72, 5, RGB565_YELLOW);

  gfx->setTextSize(1);
  gfx->setTextColor(RGB565_CYAN);
  gfx->setCursor(81, 118);
  gfx->print("BRICK SMASHER  1UP");
}

void drawBreakoutArcadeHome() {
  fillArcadeGradient();
  drawArcadeStars();
  drawArcadeCabinets();
  drawArcadeFloor();
  drawBreakoutBrickWallDecor();
  drawBreakoutPlayfieldDecor();
  drawBreakoutTitleSign();
}

void drawPongTitleSign() {
  uint16_t signFill = rgb888to565(12, 10, 28);
  uint16_t arcadeOrange = rgb888to565(255, 128, 0);
  uint16_t arcadeBlue = rgb888to565(0, 65, 210);
  uint16_t arcadeMagenta = rgb888to565(255, 0, 180);

  gfx->fillRoundRect(18, 18, 284, 92, 10, signFill);
  gfx->drawRoundRect(18, 18, 284, 92, 10, arcadeBlue);
  gfx->drawRoundRect(22, 22, 276, 84, 8, RGB565_CYAN);
  gfx->drawRoundRect(26, 26, 268, 76, 7, arcadeOrange);

  for (int x = 38; x < 286; x += 20) {
    gfx->fillCircle(x, 30, 3, arcadeMagenta);
    gfx->drawCircle(x, 30, 4, RGB565_YELLOW);
    gfx->fillCircle(x, 98, 3, arcadeBlue);
    gfx->drawCircle(x, 98, 4, RGB565_CYAN);
  }

  drawPixelText("PONG", 84, 48, 5, RGB565_YELLOW, RGB565_RED);
}

void drawPongCourtDecor() {
  uint16_t courtLine = RGB565_CYAN;
  uint16_t arcadeMagenta = rgb888to565(255, 0, 180);
  uint16_t darkPanel = rgb888to565(2, 4, 18);

  gfx->fillRoundRect(42, 132, 236, 210, 8, darkPanel);
  gfx->drawRoundRect(42, 132, 236, 210, 8, courtLine);
  gfx->drawRoundRect(47, 137, 226, 200, 6, arcadeMagenta);

  for (int x = 58; x < 262; x += 22) {
    gfx->drawLine(x, 235, x + 10, 235, RGB565_WHITE);
  }

  gfx->fillRoundRect(122, 155, 76, 9, 4, RGB565_RED);
  gfx->drawRoundRect(122, 155, 76, 9, 4, RGB565_WHITE);
  gfx->fillRoundRect(122, 310, 76, 9, 4, RGB565_GREEN);
  gfx->drawRoundRect(122, 310, 76, 9, 4, RGB565_WHITE);

  gfx->fillCircle(160, 234, 7, RGB565_WHITE);
  gfx->drawCircle(160, 234, 8, RGB565_YELLOW);

  gfx->setTextSize(1);
  gfx->setTextColor(RGB565_CYAN);
  gfx->setCursor(92, 118);
  gfx->print("CPU VS PLAYER");
}

void drawPongArcadeHome() {
  fillArcadeGradient();
  drawArcadeStars();
  drawArcadeCabinets();
  drawArcadeFloor();
  drawPongCourtDecor();
  drawPongTitleSign();
}

void drawSnakeTitleSign() {
  uint16_t signFill = rgb888to565(12, 10, 28);
  uint16_t arcadeOrange = rgb888to565(255, 128, 0);
  uint16_t arcadeBlue = rgb888to565(0, 65, 210);
  uint16_t arcadeMagenta = rgb888to565(255, 0, 180);

  gfx->fillRoundRect(18, 18, 284, 92, 10, signFill);
  gfx->drawRoundRect(18, 18, 284, 92, 10, RGB565_GREEN);
  gfx->drawRoundRect(22, 22, 276, 84, 8, RGB565_CYAN);
  gfx->drawRoundRect(26, 26, 268, 76, 7, arcadeOrange);

  for (int x = 38; x < 286; x += 20) {
    gfx->fillCircle(x, 30, 3, arcadeMagenta);
    gfx->drawCircle(x, 30, 4, RGB565_YELLOW);
    gfx->fillCircle(x, 98, 3, arcadeBlue);
    gfx->drawCircle(x, 98, 4, RGB565_CYAN);
  }

  drawPixelText("SNAKE", 58, 48, 5, RGB565_GREEN, arcadeBlue);
}

void drawSnakeBoardDecor() {
  uint16_t gridColor = rgb888to565(20, 90, 55);
  uint16_t darkPanel = rgb888to565(2, 14, 10);
  uint16_t foodColor = RGB565_RED;

  gfx->fillRoundRect(42, 132, 236, 210, 8, darkPanel);
  gfx->drawRoundRect(42, 132, 236, 210, 8, RGB565_GREEN);
  gfx->drawRoundRect(47, 137, 226, 200, 6, RGB565_CYAN);

  for (int x = 58; x <= 262; x += 24) {
    gfx->drawLine(x, 148, x, 326, gridColor);
  }

  for (int y = 148; y <= 326; y += 24) {
    gfx->drawLine(58, y, 262, y, gridColor);
  }

  int snakeX[] = {96, 120, 144, 168, 192, 216};
  int snakeY[] = {254, 254, 254, 230, 230, 230};

  for (int i = 0; i < 6; i++) {
    gfx->fillRoundRect(snakeX[i] - 9, snakeY[i] - 9, 18, 18, 5, RGB565_GREEN);
    gfx->drawRoundRect(snakeX[i] - 9, snakeY[i] - 9, 18, 18, 5, RGB565_WHITE);
  }

  gfx->fillCircle(216, 230, 3, RGB565_BLACK);
  gfx->fillCircle(220, 230, 3, RGB565_BLACK);
  gfx->fillCircle(108, 194, 7, foodColor);
  gfx->drawCircle(108, 194, 8, RGB565_YELLOW);

  gfx->setTextSize(1);
  gfx->setTextColor(RGB565_CYAN);
  gfx->setCursor(92, 118);
  gfx->print("GROW  SURVIVE  SCORE");
}

void drawSnakeArcadeHome() {
  fillArcadeGradient();
  drawArcadeStars();
  drawArcadeCabinets();
  drawArcadeFloor();
  drawSnakeBoardDecor();
  drawSnakeTitleSign();
}

void drawRanchRushFence(int y) {
  uint16_t fence = rgb888to565(214, 186, 170);

  gfx->fillRect(0, y, screenW, 5, fence);
  gfx->fillRect(0, y + 16, screenW, 5, fence);

  for (int x = 10; x < screenW; x += 40) {
    gfx->fillRect(x, y - 3, 5, 27, fence);
  }
}

void drawRanchRushTitleSign() {
  uint16_t signFill = rgb888to565(40, 30, 10);
  uint16_t ranchBrown = rgb888to565(138, 65, 17);
  uint16_t ranchOrange = rgb888to565(255, 160, 0);
  uint16_t ranchGreen = rgb888to565(92, 196, 100);

  gfx->fillRoundRect(18, 18, 284, 92, 10, signFill);
  gfx->drawRoundRect(18, 18, 284, 92, 10, ranchBrown);
  gfx->drawRoundRect(22, 22, 276, 84, 8, ranchOrange);
  gfx->drawRoundRect(26, 26, 268, 76, 7, ranchGreen);

  for (int x = 38; x < 286; x += 20) {
    gfx->fillCircle(x, 30, 3, ranchOrange);
    gfx->drawCircle(x, 30, 4, RGB565_YELLOW);
    gfx->fillCircle(x, 98, 3, ranchBrown);
    gfx->drawCircle(x, 98, 4, ranchOrange);
  }

  drawPixelText("RANCH", 50, 38, 4, RGB565_YELLOW, ranchBrown);
  drawPixelText("RUSH", 87, 72, 4, RGB565_WHITE, ranchOrange);
}

void drawRanchRushCowboyDecor(int x, int y) {
  uint16_t ranchBrown = rgb888to565(138, 65, 17);
  uint16_t horse = RGB565_YELLOW;
  uint16_t shirt = rgb888to565(60, 100, 255);
  uint16_t skin = rgb888to565(255, 160, 0);

  gfx->fillRect(x - 18, y + 8, 34, 14, horse);
  gfx->fillCircle(x + 14, y + 12, 7, horse);
  gfx->fillRect(x - 12, y + 21, 3, 10, horse);
  gfx->fillRect(x - 2, y + 21, 3, 10, horse);
  gfx->fillRect(x + 8, y + 21, 3, 10, horse);
  gfx->drawLine(x - 18, y + 11, x - 28, y + 4, horse);
  gfx->drawLine(x - 19, y + 13, x - 30, y + 10, horse);

  gfx->fillCircle(x - 3, y - 1, 5, skin);
  gfx->fillRect(x - 8, y + 4, 11, 12, shirt);
  gfx->fillRect(x - 13, y - 9, 20, 3, ranchBrown);
  gfx->fillRect(x - 8, y - 15, 10, 7, ranchBrown);
  gfx->drawLine(x + 3, y + 7, x + 54, y - 4, RGB565_WHITE);
  gfx->drawCircle(x + 58, y - 5, 12, RGB565_WHITE);
}

void drawRanchRushAnimalDecor(int x, int y) {
  uint16_t ranchBrown = rgb888to565(138, 65, 17);

  gfx->fillRect(x - 12, y + 8, 28, 13, ranchBrown);
  gfx->fillCircle(x + 16, y + 12, 6, ranchBrown);
  gfx->fillCircle(x + 22, y + 8, 5, ranchBrown);
  gfx->fillRect(x - 6, y + 20, 3, 10, ranchBrown);
  gfx->fillRect(x + 4, y + 20, 3, 10, ranchBrown);
  gfx->fillRect(x + 12, y + 20, 3, 10, ranchBrown);
  gfx->drawLine(x + 20, y + 4, x + 15, y - 3, RGB565_WHITE);
  gfx->drawLine(x + 24, y + 4, x + 30, y - 3, RGB565_WHITE);
  gfx->drawLine(x - 12, y + 11, x - 22, y + 5, ranchBrown);
  gfx->fillRect(x - 4, y + 10, 4, 4, RGB565_BLACK);
  gfx->fillRect(x + 8, y + 12, 3, 3, RGB565_BLACK);
}

void drawRanchRushFieldDecor() {
  uint16_t sky = rgb888to565(100, 180, 255);
  uint16_t field = rgb888to565(75, 145, 35);
  uint16_t darkField = rgb888to565(51, 100, 0);
  uint16_t green2 = rgb888to565(92, 196, 100);
  uint16_t dirt = rgb888to565(160, 120, 60);

  gfx->fillRect(0, 112, screenW, 68, sky);
  gfx->fillRect(0, 180, screenW, 190, field);
  gfx->fillRect(0, 330, screenW, 40, dirt);
  drawRanchRushFence(132);
  drawRanchRushFence(338);

  for (int i = 0; i < 5; i++) {
    int y = 190 + i * 33;
    gfx->drawLine(0, y, screenW - 1, y, green2);
  }

  for (int i = 0; i < 36; i++) {
    int x = (i * 47 + 9) % screenW;
    int y = 188 + ((i * 31 + 17) % 138);
    gfx->drawPixel(x, y, darkField);
    gfx->drawPixel(x + 1, y + 1, green2);
  }

  drawRanchRushCowboyDecor(72, 248);
  drawRanchRushAnimalDecor(230, 230);
  drawRanchRushAnimalDecor(256, 286);

  gfx->setTextSize(1);
  gfx->setTextColor(RGB565_YELLOW);
  gfx->setCursor(69, 118);
  gfx->print("LANES  LASSO  CATTLE");
}

void drawRanchRushArcadeHome() {
  fillArcadeGradient();
  drawArcadeStars();
  drawArcadeCabinets();
  drawArcadeFloor();
  drawRanchRushFieldDecor();
  drawRanchRushTitleSign();
}

void drawTransparentArcadeButton(int x, int y, int w, int h, const char *label, int textSize) {
  uint16_t mainTextColor = RGB565_YELLOW;
  uint16_t secondTextColor = RGB565_RED;

  if (strcmp(label, "BACK") == 0 || strcmp(label, "HOME") == 0) {
    mainTextColor = RGB565_CYAN;
    secondTextColor = RGB565_YELLOW;
  }

  int16_t x1, y1;
  uint16_t tw, th;
  int fittedSize = textSize;

  do {
    gfx->setTextSize(fittedSize);
    gfx->getTextBounds((char *)label, 0, 0, &x1, &y1, &tw, &th);

    if (tw <= (uint16_t)(w - 8) || fittedSize <= 1) {
      break;
    }

    fittedSize--;
  } while (true);

  int tx = x + (w - tw) / 2;
  int ty = y + (h - th) / 2 + 2;

  gfx->setCursor(tx + 2, ty + 2);
  gfx->setTextColor(secondTextColor);
  gfx->print(label);

  gfx->setCursor(tx, ty);
  gfx->setTextColor(mainTextColor);
  gfx->print(label);
}

void drawButton(int x, int y, int w, int h, uint16_t fillColor, uint16_t borderColor, uint16_t textColor, const char *label, int textSize) {
  // Shared arcade button style. The original fill color still chooses the
  // button mood, but all buttons use the same neon cabinet frame.
  uint16_t darkFill = rgb888to565(0, 6, 20);
  uint16_t coreColor = RGB565_CYAN;
  uint16_t mainTextColor = RGB565_YELLOW;
  uint16_t shadowTextColor = RGB565_RED;

  if (fillColor == RGB565_RED) {
    darkFill = rgb888to565(28, 0, 10);
    coreColor = RGB565_RED;
    mainTextColor = RGB565_YELLOW;
    shadowTextColor = RGB565_RED;
  } else if (fillColor == RGB565_GREEN) {
    darkFill = rgb888to565(0, 24, 16);
    coreColor = RGB565_GREEN;
    mainTextColor = RGB565_YELLOW;
    shadowTextColor = RGB565_RED;
  } else if (fillColor == RGB565_BLACK) {
    darkFill = RGB565_BLACK;
    coreColor = borderColor;
    mainTextColor = textColor;
    shadowTextColor = rgb888to565(0, 65, 210);
  } else {
    darkFill = rgb888to565(0, 8, 30);
    coreColor = RGB565_CYAN;
    mainTextColor = RGB565_CYAN;
    shadowTextColor = rgb888to565(0, 65, 210);
  }

  if (strcmp(label, "BACK") == 0 ||
      strcmp(label, "MENU") == 0 ||
      strcmp(label, "MENU") == 0 ||
      strcmp(label, "HOME") == 0) {
    mainTextColor = RGB565_CYAN;
    shadowTextColor = rgb888to565(0, 65, 210);
  }

  gfx->fillRoundRect(x, y, w, h, 7, darkFill);
  drawNeonRect(x, y, w, h, coreColor);

  int16_t x1, y1;
  uint16_t tw, th;
  int fittedSize = textSize;

  do {
    gfx->setTextSize(fittedSize);
    gfx->getTextBounds((char *)label, 0, 0, &x1, &y1, &tw, &th);

    if (tw <= (uint16_t)(w - 8) || fittedSize <= 1) {
      break;
    }

    fittedSize--;
  } while (true);

  int tx = x + (w - tw) / 2;
  int ty = y + (h - th) / 2 + 2;

  gfx->setCursor(tx + 2, ty + 2);
  gfx->setTextColor(shadowTextColor);
  gfx->print(label);

  gfx->setCursor(tx, ty);
  gfx->setTextColor(mainTextColor);
  gfx->print(label);
}

uint32_t highestOfTwo(uint32_t a, uint32_t b) {
  return (a > b) ? a : b;
}

uint32_t highestOfThree(uint32_t a, uint32_t b, uint32_t c) {
  return highestOfTwo(highestOfTwo(a, b), c);
}

void drawGameMenuHighScore(uint32_t highScore) {
  char line[40];
  snprintf(line, sizeof(line), "HIGH SCORE  %lu", (unsigned long)highScore);
  drawCenteredTextWithShadow(line, 462, 1, RGB565_WHITE, RGB565_BLACK);
}

void drawGameMenuScoreAndHigh(const char *scoreLine, uint32_t highScore) {
  drawCenteredTextWithShadow(scoreLine, 448, 1, RGB565_WHITE, RGB565_BLACK);
  drawGameMenuHighScore(highScore);
}

void drawTextInRect(int x, int y, int w, int h, const char *label, int textSize, uint16_t color) {
  int16_t x1, y1;
  uint16_t tw, th;

  gfx->setTextSize(textSize);
  gfx->getTextBounds((char *)label, 0, 0, &x1, &y1, &tw, &th);

  int tx = x + (w - tw) / 2;
  int ty = y + (h - th) / 2 + 2;

  gfx->setCursor(tx, ty);
  gfx->setTextColor(color);
  gfx->print(label);
}

// RPSLS fallback wheel drawing. The production wheel is a RAW image from SD,
// but these generated sectors keep Local and Network choice screens playable if
// /RPSLS_game/general/rpsls_wheel.raw is missing.
void drawRpsSegment(int centerX, int centerY, int radius, float startDeg, float endDeg, uint16_t color) {
  const float degToRad = 0.01745329252f;
  float startRad = startDeg * degToRad;
  int prevX = centerX + (int)(cos(startRad) * radius);
  int prevY = centerY + (int)(sin(startRad) * radius);

  for (float angle = startDeg + 3.0f; angle <= endDeg + 0.1f; angle += 3.0f) {
    float rad = angle * degToRad;
    int x = centerX + (int)(cos(rad) * radius);
    int y = centerY + (int)(sin(rad) * radius);

    gfx->fillTriangle(centerX, centerY, prevX, prevY, x, y, color);
    prevX = x;
    prevY = y;
  }
}

void drawRpsWheelLabel(const char *label, int x, int y, int size) {
  int16_t x1, y1;
  uint16_t w, h;

  gfx->setTextSize(size);
  gfx->getTextBounds((char *)label, 0, 0, &x1, &y1, &w, &h);
  gfx->setCursor(x - (int)w / 2, y - (int)h / 2);
  gfx->setTextColor(RGB565_BLACK);
  gfx->print(label);
}

void drawRpsWheel() {
  // Prefer the SD-rendered wheel; fall back to a simple generated wheel if the
  // asset is missing so the game remains playable.
  if (sdReady && SD.exists(rpsWheelImagePath)) {
    if (drawRaw565ImageFromSD(rpsWheelImagePath, 0, 0, screenW, screenH)) {
      return;
    }
  }

  uint16_t colors[5] = {
    rgb888to565(150, 170, 190),
    rgb888to565(210, 232, 246),
    rgb888to565(0, 135, 215),
    rgb888to565(105, 210, 45),
    rgb888to565(245, 145, 18)
  };

  drawRpsSegment(rpsWheelCenterX, rpsWheelCenterY, rpsWheelRadius, -126, -54, colors[0]);
  drawRpsSegment(rpsWheelCenterX, rpsWheelCenterY, rpsWheelRadius, -54, 18, colors[1]);
  drawRpsSegment(rpsWheelCenterX, rpsWheelCenterY, rpsWheelRadius, 18, 90, colors[2]);
  drawRpsSegment(rpsWheelCenterX, rpsWheelCenterY, rpsWheelRadius, 90, 162, colors[3]);
  drawRpsSegment(rpsWheelCenterX, rpsWheelCenterY, rpsWheelRadius, 162, 234, colors[4]);

  for (int i = 0; i < 4; i++) {
    gfx->drawCircle(rpsWheelCenterX, rpsWheelCenterY, rpsWheelRadius - i, RGB565_WHITE);
  }

  const int boundaryCount = 5;
  float boundaries[boundaryCount] = {-126, -54, 18, 90, 162};
  const float degToRad = 0.01745329252f;

  for (int i = 0; i < boundaryCount; i++) {
    float rad = boundaries[i] * degToRad;
    int x = rpsWheelCenterX + (int)(cos(rad) * rpsWheelRadius);
    int y = rpsWheelCenterY + (int)(sin(rad) * rpsWheelRadius);

    for (int offset = -1; offset <= 1; offset++) {
      gfx->drawLine(rpsWheelCenterX + offset, rpsWheelCenterY, x + offset, y, RGB565_BLACK);
    }
  }

  gfx->fillCircle(rpsWheelCenterX, rpsWheelCenterY, 14, RGB565_BLACK);

  drawRpsWheelLabel("ROCK", 160, 135, 2);
  drawRpsWheelLabel("PAPER", 243, 214, 2);
  drawRpsWheelLabel("SCISSORS", 222, 320, 2);
  drawRpsWheelLabel("LIZARD", 98, 320, 2);
  drawRpsWheelLabel("SPOCK", 77, 214, 2);
}

int rpsChoiceFromTouch(int x, int y) {
  // Invisible buttons: convert touch position to polar angle and map that angle
  // to one of the five wheel slices.
  long dx = x - rpsWheelCenterX;
  long dy = y - rpsWheelCenterY;
  long distanceSquared = dx * dx + dy * dy;
  long radiusSquared = (long)rpsWheelRadius * rpsWheelRadius;

  if (distanceSquared > radiusSquared) return -1;

  float angle = atan2((float)dy, (float)dx) * 57.2957795f;

  if (angle < -126.0f) {
    angle += 360.0f;
  }

  if (angle >= -126.0f && angle < -54.0f) return 0;
  if (angle >= -54.0f && angle < 18.0f) return 1;
  if (angle >= 18.0f && angle < 90.0f) return 2;
  if (angle >= 90.0f && angle < 162.0f) return 3;
  return 4;
}

void drawIpFields() {
  // Shared IP editor fields for Settings, Host, and Join screens.
  for (int i = 0; i < 4; i++) {
    int x = settingsFieldX + i * (settingsFieldW + settingsFieldGap);
    uint16_t fillColor = (i == activeIpField) ? RGB565_BLUE : RGB565_BLACK;
    uint16_t borderColor = (i == activeIpField) ? RGB565_YELLOW : RGB565_CYAN;

    gfx->fillRoundRect(x, settingsFieldY, settingsFieldW, settingsFieldH, 8, fillColor);
    gfx->drawRoundRect(x, settingsFieldY, settingsFieldW, settingsFieldH, 8, borderColor);
    drawTextInRect(x, settingsFieldY, settingsFieldW, settingsFieldH, ipFieldText[i], 2, RGB565_WHITE);

    if (i < 3) {
      int dotX = x + settingsFieldW + 4;
      drawTextInRect(dotX, settingsFieldY, settingsFieldGap, settingsFieldH, ".", 2, RGB565_WHITE);
    }
  }
}

void drawSettingsKeypad() {
  const char *labels[12] = {
    "1", "2", "3",
    "4", "5", "6",
    "7", "8", "9",
    "DEL", "0", "NEXT"
  };

  for (int i = 0; i < 12; i++) {
    int col = i % 3;
    int row = i / 3;
    int x = keyPadX + col * (keyPadW + keyPadGapX);
    int y = keyPadY + row * (keyPadH + keyPadGapY);

    uint16_t fillColor = RGB565_BLUE;
    uint16_t textColor = RGB565_WHITE;

    if (i == 9) fillColor = RGB565_RED;
    if (i == 11) {
      fillColor = RGB565_GREEN;
      textColor = RGB565_BLACK;
    }

    drawButton(x, y, keyPadW, keyPadH, fillColor, RGB565_WHITE, textColor, labels[i], 2);
  }
}

void drawJoinKeypad() {
  const char *labels[12] = {
    "1", "2", "3",
    "4", "5", "6",
    "7", "8", "9",
    "DEL", "0", "NEXT"
  };

  for (int i = 0; i < 12; i++) {
    int col = i % 3;
    int row = i / 3;
    int x = joinKeyPadX + col * (joinKeyPadW + joinKeyPadGapX);
    int y = joinKeyPadY + row * (joinKeyPadH + joinKeyPadGapY);

    uint16_t fillColor = RGB565_BLUE;
    uint16_t textColor = RGB565_WHITE;

    if (i == 9) fillColor = RGB565_RED;
    if (i == 11) {
      fillColor = RGB565_GREEN;
      textColor = RGB565_BLACK;
    }

    drawButton(x, y, joinKeyPadW, joinKeyPadH, fillColor, RGB565_WHITE, textColor, labels[i], 2);
  }
}

void drawJoinNetworkList() {
  // Shows one page of scanned SSIDs. Empty rows remain visible to keep layout
  // stable when fewer than eight networks are found.
  for (int i = 0; i < MAX_JOIN_NETWORKS_VISIBLE; i++) {
    int networkIndex = joinNetworkListOffset + i;
    int y = joinNetworkY + i * (joinNetworkH + joinNetworkGap);
    uint16_t fillColor = (networkIndex == selectedJoinNetwork) ? RGB565_GREEN : RGB565_BLUE;
    uint16_t textColor = (networkIndex == selectedJoinNetwork) ? RGB565_BLACK : RGB565_WHITE;
    char label[32];

    if (networkIndex < joinNetworkCount) {
      snprintf(label, sizeof(label), "%d %s", networkIndex + 1, joinNetworks[networkIndex].c_str());
    } else {
      snprintf(label, sizeof(label), "-");
      fillColor = RGB565_BLACK;
      textColor = RGB565_WHITE;
    }

    drawButton(joinNetworkX, y, joinNetworkW, joinNetworkH,
               fillColor, RGB565_WHITE, textColor, label, 1);
  }
}

void drawHostSSIDList() {
  // Shows one page of selectable host SSID names from epicSSIDList.
  for (int i = 0; i < MAX_HOST_SSID_VISIBLE; i++) {
    int ssidIndex = hostSSIDListOffset + i;
    int y = hostSSIDY + i * (hostSSIDH + hostSSIDGap);
    uint16_t fillColor = (ssidIndex == selectedHostSSIDIndex) ? RGB565_GREEN : RGB565_BLUE;
    uint16_t textColor = (ssidIndex == selectedHostSSIDIndex) ? RGB565_BLACK : RGB565_WHITE;
    char label[36];

    if (ssidIndex < EPIC_SSID_COUNT) {
      snprintf(label, sizeof(label), "%d %s", ssidIndex + 1, epicSSIDList[ssidIndex]);
    } else {
      snprintf(label, sizeof(label), "-");
      fillColor = RGB565_BLACK;
      textColor = RGB565_WHITE;
    }

    drawButton(hostSSIDX, y, hostSSIDW, hostSSIDH,
               fillColor, RGB565_WHITE, textColor, label, 1);
  }
}

// ============================================================================
// GAME LOGIC
// ============================================================================
// Pure game rules and asset-name lookup helpers. These functions do not handle
// touch routing; they only update game state or answer rule questions. This
// block starts with Tic Tac Toe rules, then RPSLS rule/result image helpers.
void clearBoard() {
  for (int r = 0; r < 3; r++) {
    for (int c = 0; c < 3; c++) {
      board[r][c] = ' ';
    }
  }
}

void resetGameLogic() {
  clearBoard();
  currentPlayer = 'X';
  gameOver = false;
  winner = ' ';
  myTurn = localGame || (myPlayer == 'X');
}

bool boardFull() {
  for (int r = 0; r < 3; r++) {
    for (int c = 0; c < 3; c++) {
      if (board[r][c] == ' ') return false;
    }
  }

  return true;
}

char checkWinner() {
  for (int r = 0; r < 3; r++) {
    if (board[r][0] != ' ' &&
        board[r][0] == board[r][1] &&
        board[r][1] == board[r][2]) {
      return board[r][0];
    }
  }

  for (int c = 0; c < 3; c++) {
    if (board[0][c] != ' ' &&
        board[0][c] == board[1][c] &&
        board[1][c] == board[2][c]) {
      return board[0][c];
    }
  }

  if (board[0][0] != ' ' &&
      board[0][0] == board[1][1] &&
      board[1][1] == board[2][2]) {
    return board[0][0];
  }

  if (board[0][2] != ' ' &&
      board[0][2] == board[1][1] &&
      board[1][1] == board[2][0]) {
    return board[0][2];
  }

  if (boardFull()) return 'D';

  return ' ';
}

bool rpsChoiceBeats(int firstChoice, int secondChoice) {
  // RPSLS win table: each choice beats exactly two other choices.
  if (firstChoice == 0) return secondChoice == 2 || secondChoice == 3;
  if (firstChoice == 1) return secondChoice == 0 || secondChoice == 4;
  if (firstChoice == 2) return secondChoice == 1 || secondChoice == 3;
  if (firstChoice == 3) return secondChoice == 1 || secondChoice == 4;
  if (firstChoice == 4) return secondChoice == 0 || secondChoice == 2;

  return false;
}

int calculateRpsWinner(int p1Choice, int p2Choice) {
  if (p1Choice == p2Choice) return 0;
  if (rpsChoiceBeats(p1Choice, p2Choice)) return 1;
  return 2;
}

void resetRpsRound() {
  rpsP1Choice = -1;
  rpsP2Choice = -1;
  rpsWinner = 0;
}

const char *getRpsWinImageBaseName(int winningChoice, int losingChoice) {
  // Maps a winning pair to the RAW filename stem used on SD.
  if (winningChoice == 0 && losingChoice == 2) return "win_rock_crushes_scissors";
  if (winningChoice == 0 && losingChoice == 3) return "win_rock_crushes_lizard";
  if (winningChoice == 1 && losingChoice == 0) return "win_paper_covers_rock";
  if (winningChoice == 1 && losingChoice == 4) return "win_paper_releases_spock";
  if (winningChoice == 2 && losingChoice == 1) return "win_scissors_cuts_paper";
  if (winningChoice == 2 && losingChoice == 3) return "win_scissors_cuts_lizard";
  if (winningChoice == 3 && losingChoice == 1) return "win_lizard_eats_paper";
  if (winningChoice == 3 && losingChoice == 4) return "win_lizard_poisons_spock";
  if (winningChoice == 4 && losingChoice == 0) return "win_spock_vaporizes_rock";
  if (winningChoice == 4 && losingChoice == 2) return "win_spock_smashes_scissors";

  return nullptr;
}

const char *getRpsLoseImageBaseName(int winningChoice, int losingChoice) {
  // Network RPSLS is viewpoint-specific. The losing player sees a lose_ image
  // for the same winning pair.
  if (winningChoice == 0 && losingChoice == 2) return "lose_scissors_to_rock";
  if (winningChoice == 0 && losingChoice == 3) return "lose_lizard_to_rock";
  if (winningChoice == 1 && losingChoice == 0) return "lose_rock_to_paper";
  if (winningChoice == 1 && losingChoice == 4) return "lose_spock_to_paper";
  if (winningChoice == 2 && losingChoice == 1) return "lose_paper_to_scissors";
  if (winningChoice == 2 && losingChoice == 3) return "lose_lizard_to_scissors";
  if (winningChoice == 3 && losingChoice == 1) return "lose_paper_to_lizard";
  if (winningChoice == 3 && losingChoice == 4) return "lose_spock_to_lizard";
  if (winningChoice == 4 && losingChoice == 0) return "lose_rock_to_spock";
  if (winningChoice == 4 && losingChoice == 2) return "lose_scissors_to_spock";

  return nullptr;
}

const char *getRpsDrawImageBaseName(int choice) {
  if (choice == 0) return "draw_rock";
  if (choice == 1) return "draw_paper";
  if (choice == 2) return "draw_scissors";
  if (choice == 3) return "draw_lizard";
  if (choice == 4) return "draw_spock";

  return nullptr;
}

bool drawRpsRawResultImage(const char *folder, const char *baseName) {
  if (!sdReady || !baseName) return false;

  char path[96];
  snprintf(path, sizeof(path), "%s/%s.raw", folder, baseName);

  if (!SD.exists(path)) {
    Serial.print("Missing RPSLS result image: ");
    Serial.println(path);
    return false;
  }

  return drawRaw565ImageFromSD(path, 0, 0, screenW, screenH);
}

bool drawRpsDrawImage() {
  if (rpsWinner != 0) return false;

  return drawRpsRawResultImage(rpsDrawPath, getRpsDrawImageBaseName(rpsP1Choice));
}

bool drawRpsWinningImage() {
  if (!sdReady || rpsWinner == 0) return false;

  int winningChoice = (rpsWinner == 1) ? rpsP1Choice : rpsP2Choice;
  int losingChoice = (rpsWinner == 1) ? rpsP2Choice : rpsP1Choice;

  if (!localGame && (myPlayer == '1' || myPlayer == '2')) {
    // In network mode each device sees the result from its own perspective.
    bool localPlayerWon = (myPlayer == '1' && rpsWinner == 1) ||
                          (myPlayer == '2' && rpsWinner == 2);
    const char *baseName = localPlayerWon
                           ? getRpsWinImageBaseName(winningChoice, losingChoice)
                           : getRpsLoseImageBaseName(winningChoice, losingChoice);
    const char *folder = localPlayerWon ? rpsNetworkWinPath : rpsNetworkLosePath;

    return drawRpsRawResultImage(folder, baseName);
  }

  const char *baseName = getRpsWinImageBaseName(winningChoice, losingChoice);
  const char *folder = (rpsWinner == 1) ? rpsPlayer1WinsPath : rpsPlayer2WinsPath;

  return drawRpsRawResultImage(folder, baseName);
}

// ============================================================================
// GAME DRAWING
// ============================================================================
// Rendering helpers for Tic Tac Toe, RPSLS, and Tanks Wars gameplay.
// Tic Tac Toe: grid, X/O marks, and the score/turn bar.
void drawX(int cx, int cy) {
  int margin = 20;

  int x0 = boardX + cx * cellSize + margin;
  int y0 = boardY + cy * cellSize + margin;
  int x1 = boardX + (cx + 1) * cellSize - margin;
  int y1 = boardY + (cy + 1) * cellSize - margin;

  for (int i = -2; i <= 2; i++) {
    gfx->drawLine(x0 + i, y0, x1 + i, y1, RGB565_RED);
    gfx->drawLine(x0 + i, y1, x1 + i, y0, RGB565_RED);
  }
}

void drawO(int cx, int cy) {
  int centerX = boardX + cx * cellSize + cellSize / 2;
  int centerY = boardY + cy * cellSize + cellSize / 2;
  int radius = cellSize / 2 - 20;

  for (int i = 0; i < 4; i++) {
    gfx->drawCircle(centerX, centerY, radius - i, RGB565_CYAN);
  }
}

void drawSingleMark(int col, int row, char player) {
  if (player == 'X') drawX(col, row);
  if (player == 'O') drawO(col, row);
}

void drawGrid() {
  gfx->fillRect(boardX - 2, boardY - 2, boardSize + 4, boardSize + 4, RGB565_WHITE);
  gfx->fillRect(boardX, boardY, boardSize, boardSize, RGB565_BLACK);

  gfx->fillRect(boardX + cellSize - 2, boardY, 4, boardSize, RGB565_WHITE);
  gfx->fillRect(boardX + 2 * cellSize - 2, boardY, 4, boardSize, RGB565_WHITE);

  gfx->fillRect(boardX, boardY + cellSize - 2, boardSize, 4, RGB565_WHITE);
  gfx->fillRect(boardX, boardY + 2 * cellSize - 2, boardSize, 4, RGB565_WHITE);
}

void drawAllMarks() {
  for (int r = 0; r < 3; r++) {
    for (int c = 0; c < 3; c++) {
      if (board[r][c] == 'X' || board[r][c] == 'O') {
        drawSingleMark(c, r, board[r][c]);
      }
    }
  }
}

void drawScoreBar() {
  gfx->fillRect(0, 0, screenW, topBarH, RGB565_BLACK);
  gfx->drawLine(0, topBarH - 1, screenW, topBarH - 1, RGB565_WHITE);

  char scoreLine[48];
  snprintf(scoreLine, sizeof(scoreLine), "Score X:%d  O:%d  D:%d", scoreX, scoreO, scoreDraw);
  drawCenteredText(scoreLine, 10, 2, RGB565_WHITE);

  char turnLine[48];

  if (gameOver) {
    snprintf(turnLine, sizeof(turnLine), "Game over");
  } else if (localGame) {
    snprintf(turnLine, sizeof(turnLine), "Turn: %c", currentPlayer);
  } else if (myTurn) {
    snprintf(turnLine, sizeof(turnLine), "Your turn: %c", myPlayer);
  } else {
    snprintf(turnLine, sizeof(turnLine), "Waiting: %c", currentPlayer);
  }

  drawCenteredText(turnLine, 42, 2, (localGame || myTurn) ? RGB565_GREEN : RGB565_YELLOW);
}

// Tanks Wars: terrain lookup, tank drawing, projectile frames, and controls.
int getPocketTanksTerrainY(int x) {
  if (x < 0) x = 0;
  if (x >= PT_TERRAIN_W) x = PT_TERRAIN_W - 1;
  return ptTerrain[x];
}

int getPocketTanksTankY(int tankIndex) {
  int y = getPocketTanksTerrainY(ptTankX[tankIndex]) - ptTankH;

  if (y < 36) y = 36;
  if (y > ptFieldBottom - ptTankH) y = ptFieldBottom - ptTankH;

  return y;
}

uint16_t getPocketTanksTerrainColor(int x) {
  return (x % 3 == 0) ? rgb888to565(80, 164, 74) : rgb888to565(65, 132, 58);
}

void generatePocketTanksTerrain() {
  // Terrain is generated from three random sine waves. This creates smooth hills
  // while still changing the shape every round.
  float phaseA = (float)random(0, 6283) / 1000.0f;
  float phaseB = (float)random(0, 6283) / 1000.0f;
  float phaseC = (float)random(0, 6283) / 1000.0f;
  float freqA = (float)random(24, 47) / 1000.0f;
  float freqB = (float)random(58, 106) / 1000.0f;
  float freqC = (float)random(12, 22) / 1000.0f;
  float ampA = (float)random(16, 32);
  float ampB = (float)random(7, 18);
  float ampC = (float)random(8, 20);
  int baseY = random(278, 306);

  for (int x = 0; x < PT_TERRAIN_W; x++) {
    float waveA = sin((float)x * freqA + phaseA) * ampA;
    float waveB = sin((float)x * freqB + phaseB) * ampB;
    float waveC = sin((float)x * freqC + phaseC) * ampC;
    int y = baseY + (int)waveA + (int)waveB + (int)waveC;

    if (y < 242) y = 242;
    if (y > ptFieldBottom - 18) y = ptFieldBottom - 18;

    ptTerrain[x] = y;
  }

  for (int tank = 0; tank < 2; tank++) {
    // Flatten a small platform under each tank so the starting shot is readable.
    int platformY = ptTerrain[ptTankX[tank]] + random(-8, 9);

    if (platformY < 258) platformY = 258;
    if (platformY > ptFieldBottom - 34) platformY = ptFieldBottom - 34;

    for (int dx = -18; dx <= 18; dx++) {
      int x = ptTankX[tank] + dx;
      if (x >= 0 && x < PT_TERRAIN_W) {
        ptTerrain[x] = platformY;
      }
    }
  }
}

void drawPocketTanksHeader() {
  gfx->fillRect(0, 0, screenW, 54, RGB565_BLACK);

  char scoreLine[48];
  snprintf(scoreLine, sizeof(scoreLine), "P1:%d   P2:%d", ptScoreP1, ptScoreP2);
  drawCenteredText(scoreLine, 8, 1, RGB565_WHITE);

  char turnLine[32];

  if (!localGame && activeNetworkGame == NETWORK_GAME_PT) {
    snprintf(turnLine, sizeof(turnLine), myTurn ? "YOUR TURN P%d" : "WAIT P%d", ptCurrentPlayer + 1);
  } else {
    snprintf(turnLine, sizeof(turnLine), "PLAYER %d TURN", ptCurrentPlayer + 1);
  }

  drawCenteredText(turnLine, 26, 2, (localGame || myTurn) ? RGB565_GREEN : RGB565_YELLOW);
}

void drawPocketTanksTerrain() {
  for (int x = 0; x < PT_TERRAIN_W; x++) {
    int y = ptTerrain[x];
    gfx->fillRect(x, y, 1, ptFieldBottom - y, getPocketTanksTerrainColor(x));
  }
}

void drawPocketTanksTank(int tankIndex) {
  // The active player gets a yellow turret so turn ownership is visible.
  int x = ptTankX[tankIndex];
  int y = getPocketTanksTankY(tankIndex);
  uint16_t bodyColor = (tankIndex == 0) ? RGB565_RED : RGB565_BLUE;
  uint16_t turretColor = (tankIndex == ptCurrentPlayer) ? RGB565_YELLOW : RGB565_WHITE;
  int dir = (tankIndex == 0) ? 1 : -1;
  float angleRad = (float)ptAngle[tankIndex] * 0.01745329252f;
  int barrelX = x + (int)(cos(angleRad) * 23.0f * dir);
  int barrelY = y - 1 - (int)(sin(angleRad) * 23.0f);

  gfx->fillRoundRect(x - ptTankW / 2, y, ptTankW, ptTankH, 4, bodyColor);
  gfx->drawRoundRect(x - ptTankW / 2, y, ptTankW, ptTankH, 4, RGB565_WHITE);
  gfx->fillCircle(x, y, 5, turretColor);

  for (int offset = -1; offset <= 1; offset++) {
    gfx->drawLine(x, y - 1 + offset, barrelX, barrelY + offset, turretColor);
  }
}

void redrawPocketTanksBackgroundArea(int left, int top, int right, int bottom) {
  // Restores only a rectangular patch of sky/terrain. This is used to avoid
  // full-screen flicker during projectile movement and angle updates.
  if (right < 0 || left >= screenW || bottom < 0 || top >= ptFieldBottom) return;

  if (left < 0) left = 0;
  if (right >= screenW) right = screenW - 1;
  if (top < 0) top = 0;
  if (bottom >= ptFieldBottom) bottom = ptFieldBottom - 1;

  for (int x = left; x <= right; x++) {
    int terrainY = getPocketTanksTerrainY(x);

    if (top < terrainY) {
      int skyBottom = bottom;
      if (skyBottom >= terrainY) skyBottom = terrainY - 1;

      if (skyBottom >= top) {
        gfx->fillRect(x, top, 1, skyBottom - top + 1, RGB565_BLACK);
      }
    }

    if (bottom >= terrainY) {
      int groundTop = top;
      if (groundTop < terrainY) groundTop = terrainY;

      if (groundTop <= bottom) {
        gfx->fillRect(x, groundTop, 1, bottom - groundTop + 1, getPocketTanksTerrainColor(x));
      }
    }
  }
}

void redrawPocketTanksTankArea(int tankIndex, int oldAngle, int newAngle) {
  // Clears the bounding box that contains both the old and new barrel positions,
  // then redraws only the affected tank.
  int x = ptTankX[tankIndex];
  int y = getPocketTanksTankY(tankIndex);
  int dir = (tankIndex == 0) ? 1 : -1;
  float oldAngleRad = (float)oldAngle * 0.01745329252f;
  float newAngleRad = (float)newAngle * 0.01745329252f;
  int oldBarrelX = x + (int)(cos(oldAngleRad) * 25.0f * dir);
  int oldBarrelY = y - 1 - (int)(sin(oldAngleRad) * 25.0f);
  int newBarrelX = x + (int)(cos(newAngleRad) * 25.0f * dir);
  int newBarrelY = y - 1 - (int)(sin(newAngleRad) * 25.0f);
  int left = x - ptTankW / 2 - 6;
  int right = x + ptTankW / 2 + 6;
  int top = y - 32;
  int bottom = y + ptTankH + 6;

  if (oldBarrelX < left) left = oldBarrelX - 6;
  if (oldBarrelX > right) right = oldBarrelX + 6;
  if (oldBarrelY < top) top = oldBarrelY - 6;
  if (oldBarrelY > bottom) bottom = oldBarrelY + 6;

  if (newBarrelX < left) left = newBarrelX - 6;
  if (newBarrelX > right) right = newBarrelX + 6;
  if (newBarrelY < top) top = newBarrelY - 6;
  if (newBarrelY > bottom) bottom = newBarrelY + 6;

  redrawPocketTanksBackgroundArea(left, top, right, bottom);
  drawPocketTanksTank(tankIndex);
}

void redrawPocketTanksProjectileArea(int centerX, int centerY) {
  // Restores the old projectile position and then redraws both tanks because the
  // projectile can pass over a tank sprite.
  int patchRadius = ptProjectileRadius + 3;
  int left = centerX - patchRadius;
  int right = centerX + patchRadius;
  int top = centerY - patchRadius;
  int bottom = centerY + patchRadius;

  redrawPocketTanksBackgroundArea(left, top, right, bottom);

  if (top < 54) {
    drawPocketTanksHeader();
  }

  drawPocketTanksTank(0);
  drawPocketTanksTank(1);
}

void drawPocketTanksProjectileFrame(int previousX, int previousY, int currentX, int currentY) {
  // Animation frame path: restore previous dot, draw current dot. The terrain
  // and controls stay untouched for a stable frame rate.
  if (previousX >= 0 && previousY >= 0) {
    redrawPocketTanksProjectileArea(previousX, previousY);
  }

  if (currentX >= 0 && currentX < screenW && currentY >= 0 && currentY < ptFieldBottom) {
    gfx->fillCircle(currentX, currentY, ptProjectileRadius, RGB565_YELLOW);
  }
}
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
void loop() {
  // Network polling is non-blocking so menu touch, game animation, and TCP/ESP-NOW
  // traffic can all progress in the same main loop.
  checkHostClient();
  checkJoinConnection();
  pollNetwork();
  updateFroggerEspNowNetwork();

  int tx, ty;
  bool touched = readTouchScreen(tx, ty);

  // Breakout and Pong need continuous touch position for paddle control.
  breakoutTouchDown = touched;
  if (touched) {
    breakoutTouchX = tx;
    breakoutTouchY = ty;
  }

  pongTouchDown = touched;
  if (touched) {
    pongTouchX = tx;
    pongTouchY = ty;
  }

  if (touched && !touchWasDown) {
    unsigned long now = millis();

    if (now - lastTouchTime > touchDebounceMs) {
      lastTouchTime = now;
      touchWasDown = true;

      Serial.print("Touch: ");
      Serial.print(tx);
      Serial.print(", ");
      Serial.println(ty);

      handleTouch(tx, ty);
    }
  }

  if (!touched) {
    touchWasDown = false;
  }

  // Menu music only runs outside gameplay; game update calls are internally
  // gated by appState, so inactive games return immediately.
  updateMenuMusic();

  updateBreakoutGame();
  updatePongGame();
  updateSnakeGame();
  updateRanchRushGame();
  updateFroggerGame();
  updateHexPipesGame();

  delay(10);
}
